freeDSP/freeDSP-OCTAVIA/SOURCES/Documents/Figures/24bitADC.png

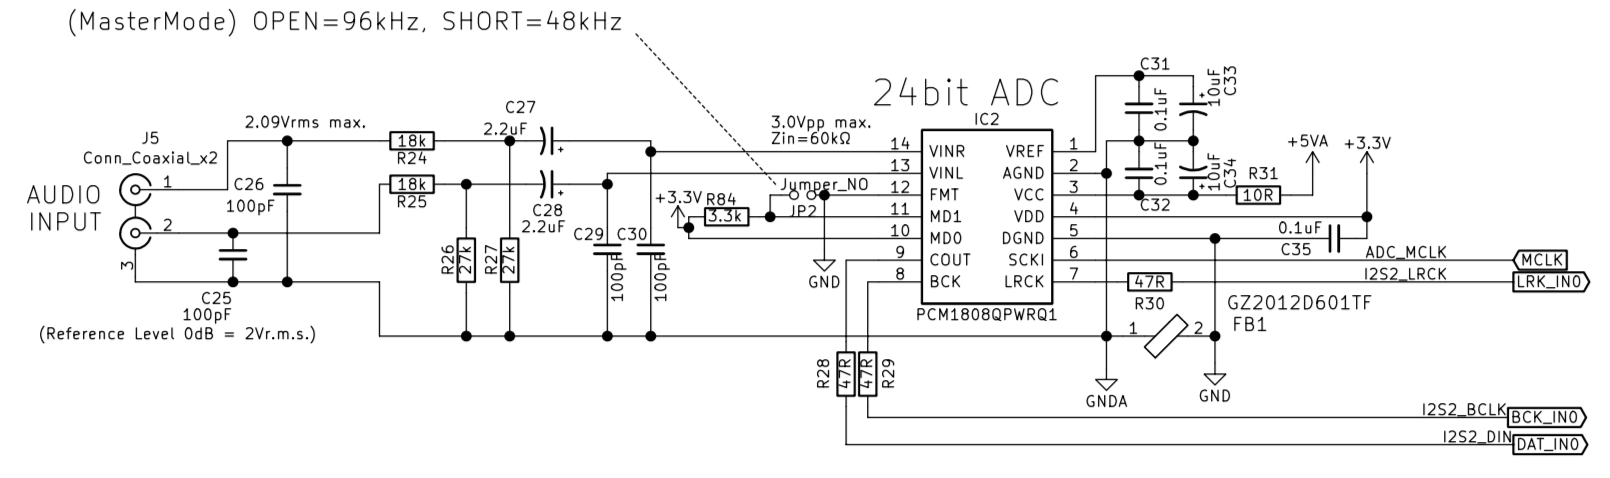
SOURCES/Documents/Figures/24bitADC.png
