freeDSP/freeDSP-OCTAVIA/SOURCES/Documents/Figures/amaneo.jpg

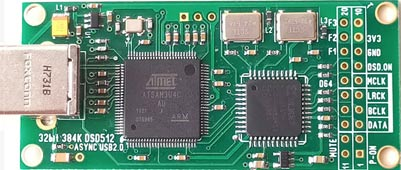
SOURCES/Documents/Figures/amaneo.jpg
