freeDSP/freeDSP-OCTAVIA/SOURCES/Documents/Figures/AnodeCommonRGB-LED.png

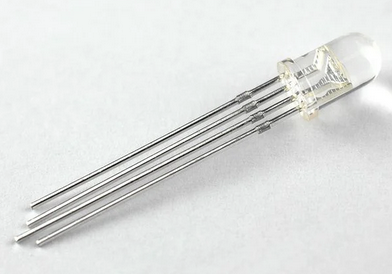
SOURCES/Documents/Figures/AnodeCommonRGB-LED.png
