freeDSP/freeDSP-OCTAVIA/SOURCES/Documents/Figures/ASRC_Setting.gif

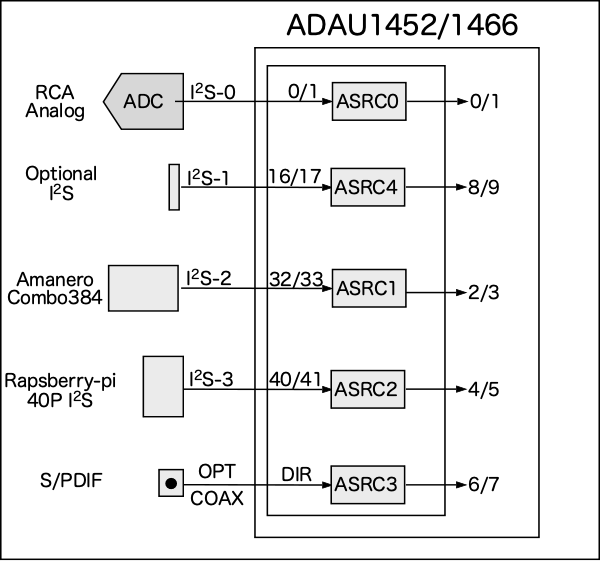
SOURCES/Documents/Figures/ASRC_Setting.gif
