freeDSP/freeDSP-OCTAVIA/SOURCES/Documents/Figures/AUX-ADC_Pots.png

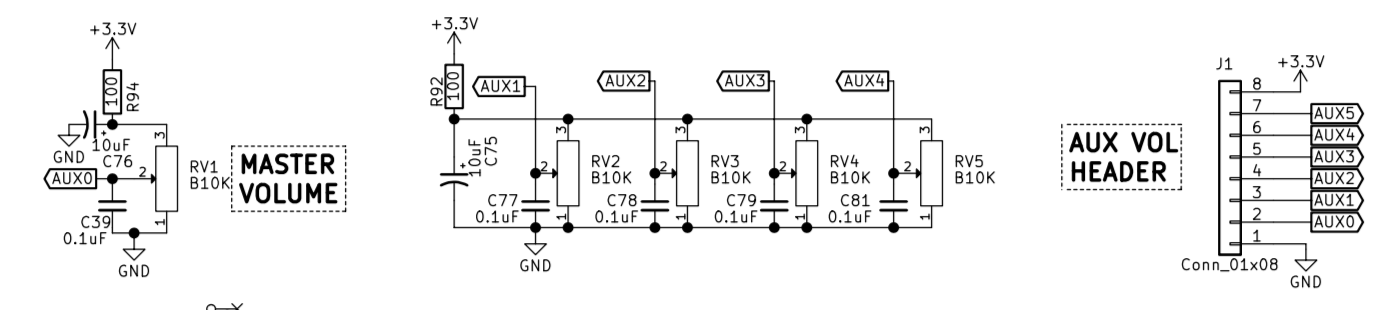
SOURCES/Documents/Figures/AUX-ADC_Pots.png
