freeDSP/freeDSP-OCTAVIA/SOURCES/Documents/Figures/Block_AmaneroCombo384Slot.png

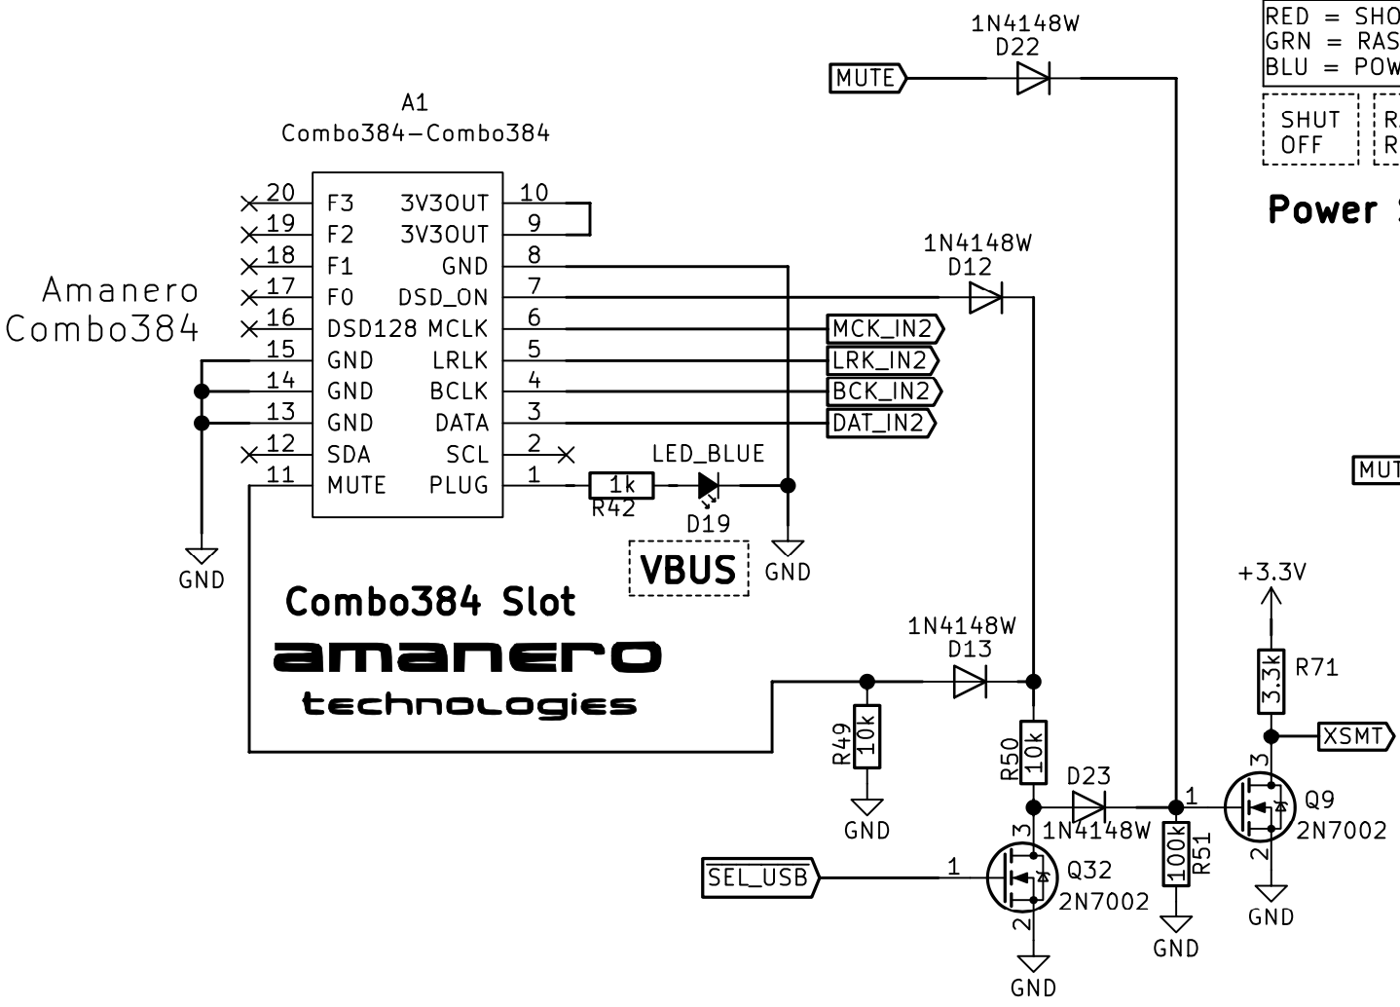
SOURCES/Documents/Figures/Block_AmaneroCombo384Slot.png
