freeDSP/freeDSP-OCTAVIA/SOURCES/Documents/Figures/Block_PowerStatusLED.png

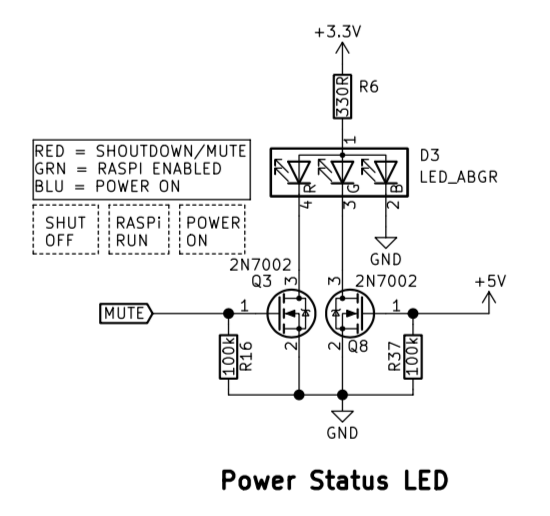
SOURCES/Documents/Figures/Block_PowerStatusLED.png
