freeDSP/freeDSP-OCTAVIA/SOURCES/Documents/Figures/Block_PSU2.png

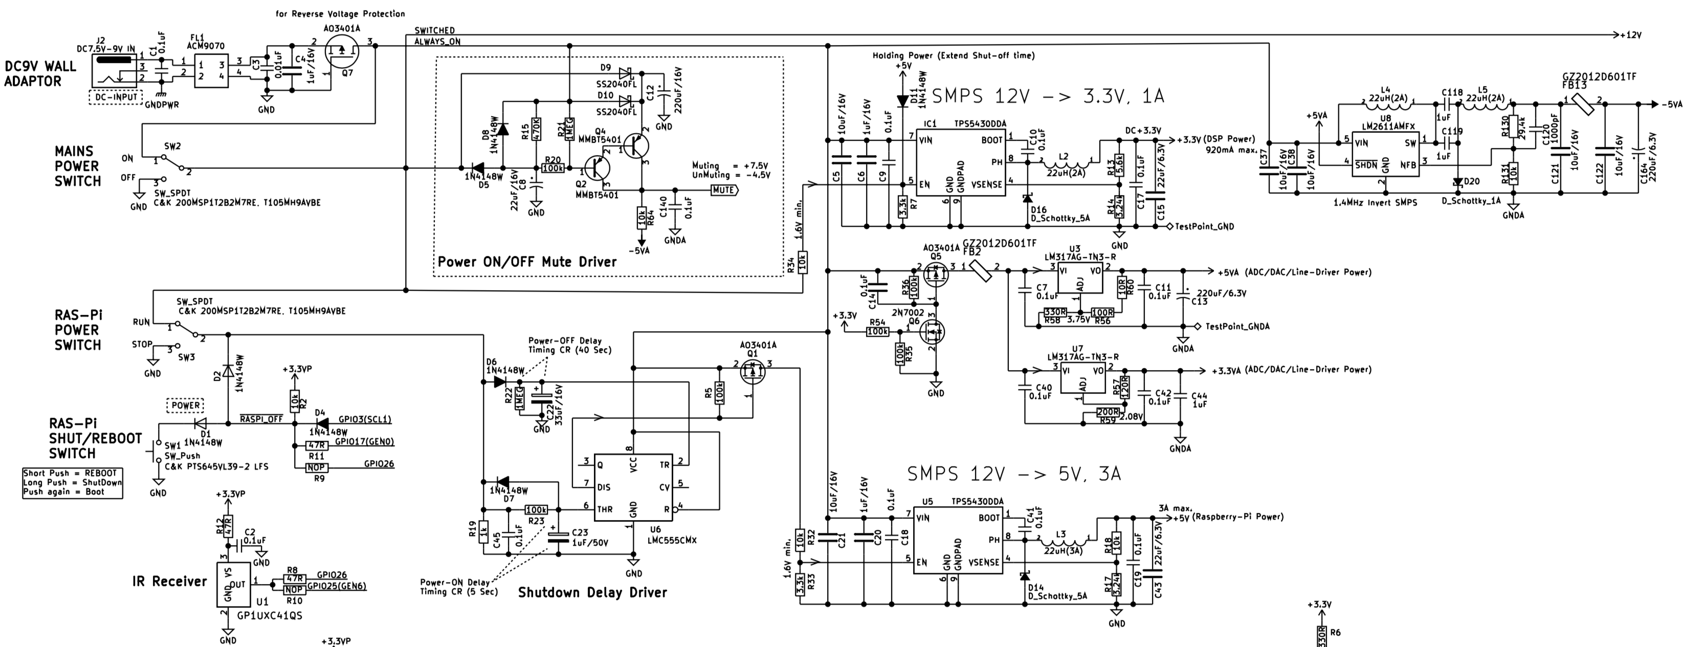
SOURCES/Documents/Figures/Block_PSU2.png
