freeDSP/freeDSP-OCTAVIA/SOURCES/Documents/Figures/Block_PSU.png

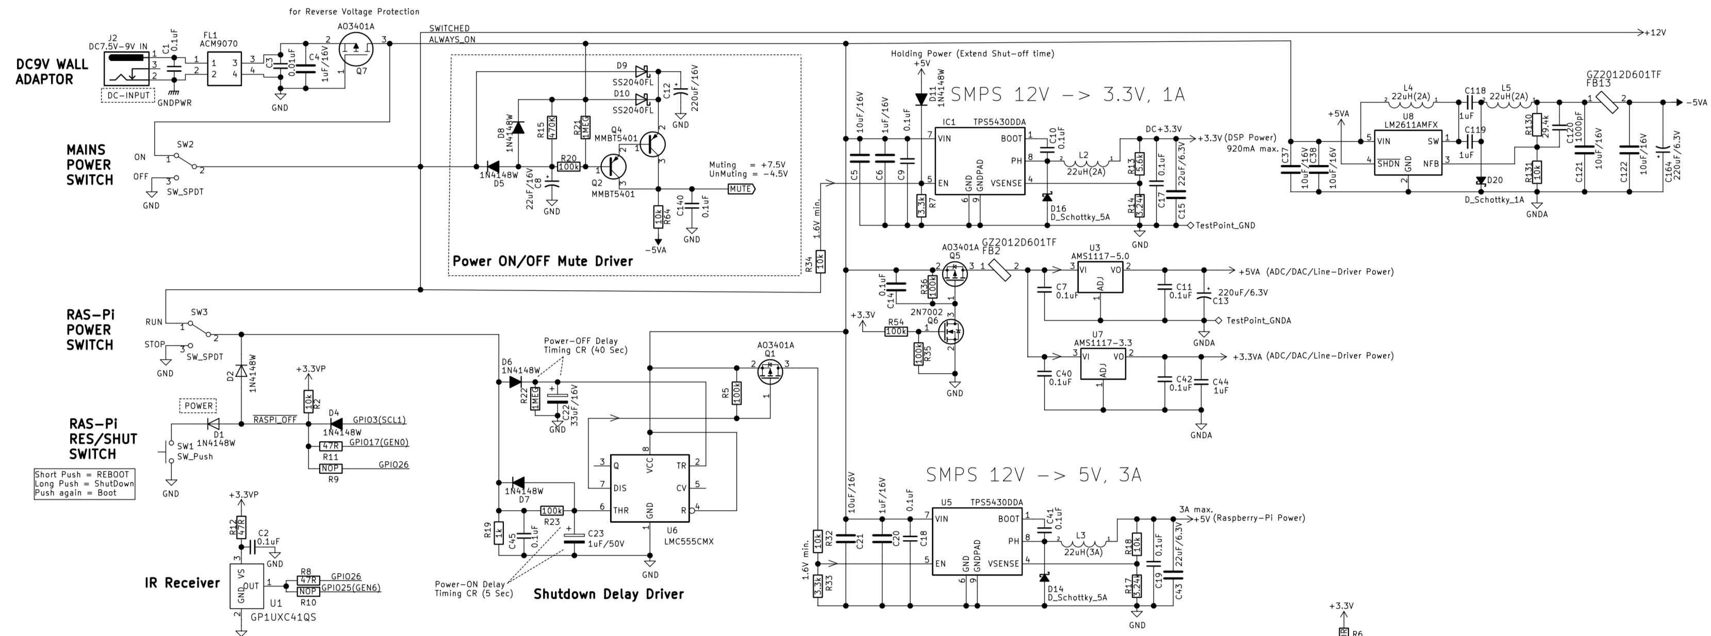
SOURCES/Documents/Figures/Block_PSU.png
