freeDSP/freeDSP-OCTAVIA/SOURCES/Documents/Figures/Block_RaspberryPiSolot.png

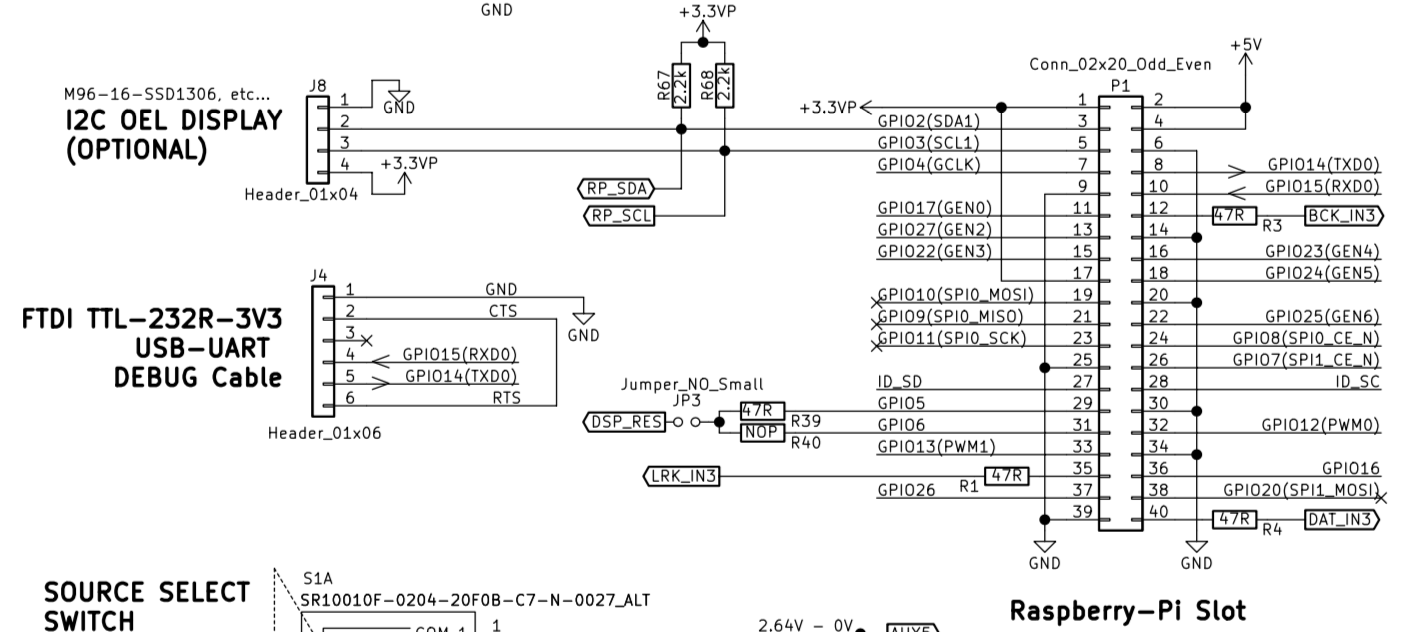
SOURCES/Documents/Figures/Block_RaspberryPiSolot.png
