freeDSP/freeDSP-OCTAVIA/SOURCES/Documents/Figures/bravo.jpg

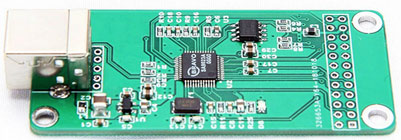
SOURCES/Documents/Figures/bravo.jpg
