freeDSP/freeDSP-OCTAVIA/SOURCES/Documents/Figures/Brovo2.jpg

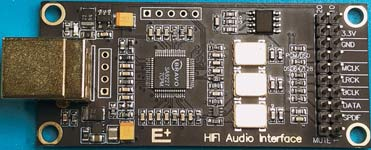
SOURCES/Documents/Figures/Brovo2.jpg
