freeDSP/freeDSP-OCTAVIA/SOURCES/Documents/Figures/C24Removed.jpg

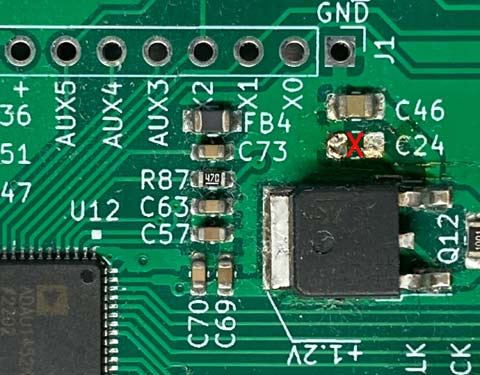
SOURCES/Documents/Figures/C24Removed.jpg
