freeDSP/freeDSP-OCTAVIA/SOURCES/Documents/Figures/Changed_R7_R33.jpg

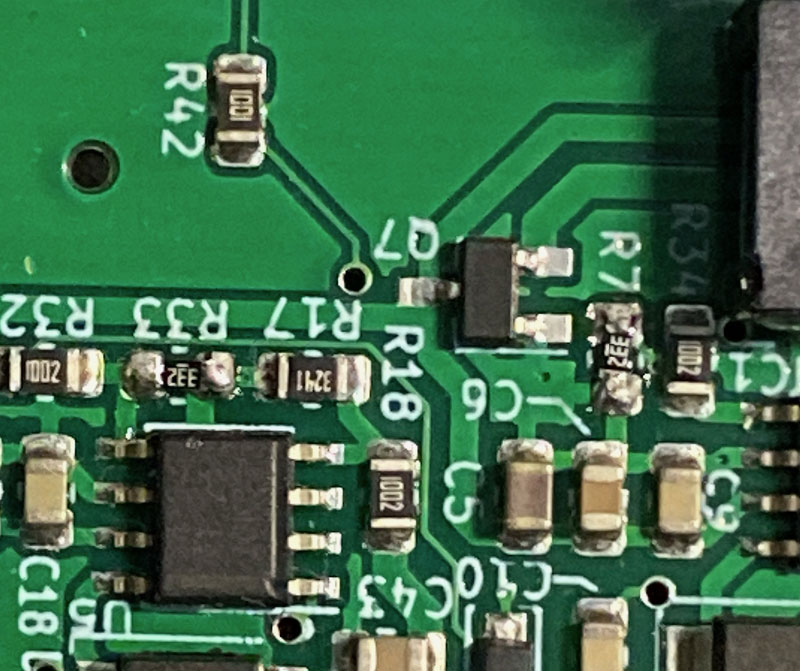
SOURCES/Documents/Figures/Changed_R7_R33.jpg
