freeDSP/freeDSP-OCTAVIA/SOURCES/Documents/Figures/ChangeR76.jpg

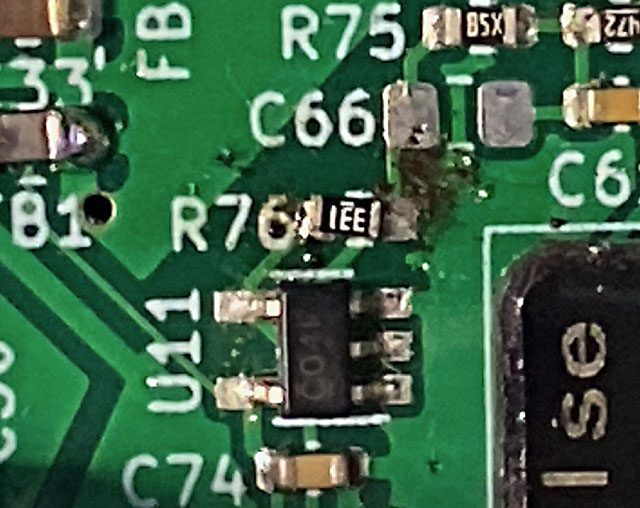
SOURCES/Documents/Figures/ChangeR76.jpg
