freeDSP/freeDSP-OCTAVIA/SOURCES/Documents/Figures/CompileLinkDownloadButton.gif

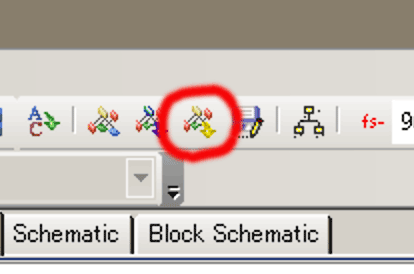
SOURCES/Documents/Figures/CompileLinkDownloadButton.gif
