freeDSP/freeDSP-OCTAVIA/SOURCES/Documents/Figures/DAC_Output.png

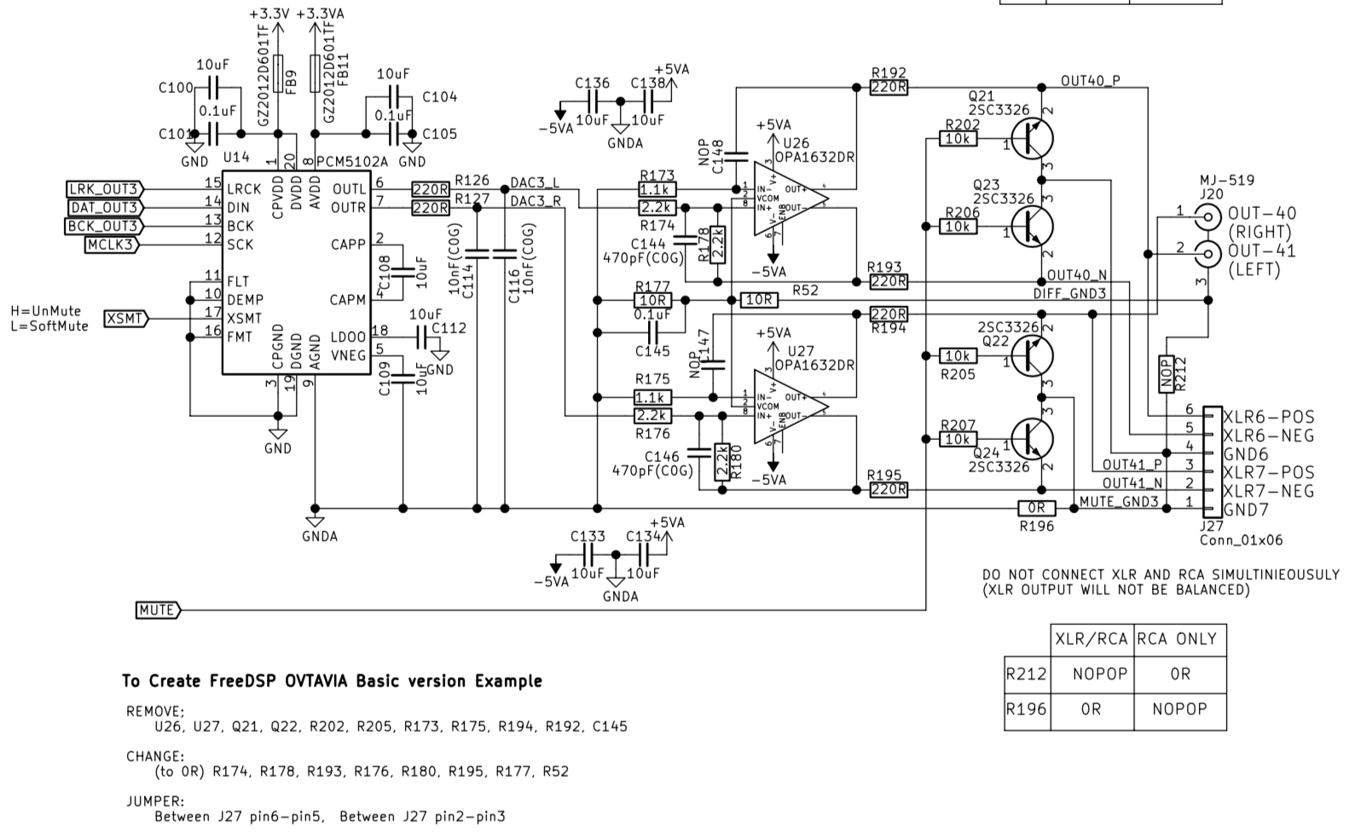
SOURCES/Documents/Figures/DAC_Output.png
