freeDSP/freeDSP-OCTAVIA/SOURCES/Documents/Figures/Diode_D4.png

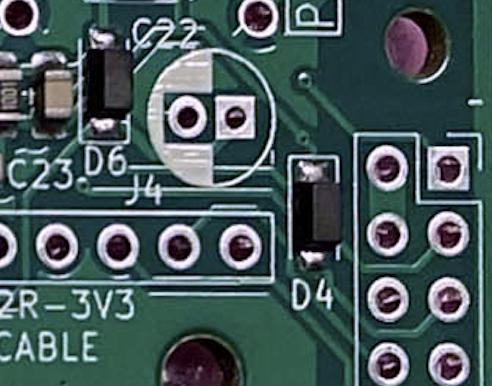
SOURCES/Documents/Figures/Diode_D4.png
