freeDSP/freeDSP-OCTAVIA/SOURCES/Documents/Figures/DSP-OCTAVIA_2wayCrossover_Trim.gif

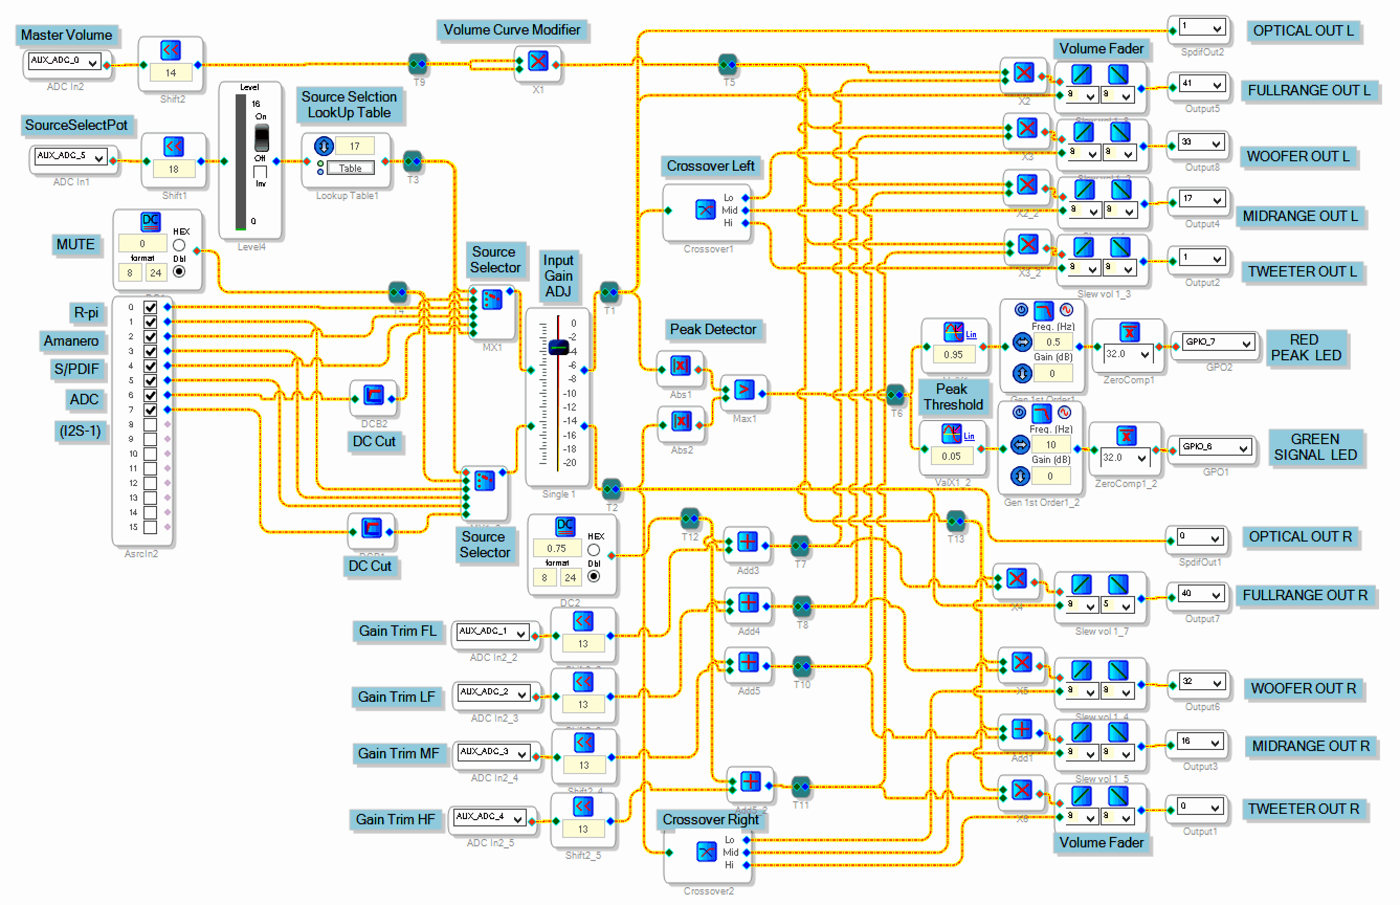
SOURCES/Documents/Figures/DSP-OCTAVIA_2wayCrossover_Trim.gif
