freeDSP/freeDSP-OCTAVIA/SOURCES/Documents/Figures/DSP-OCTAVIA_2wayCrossover_with_Sub_DelayTrim.gif

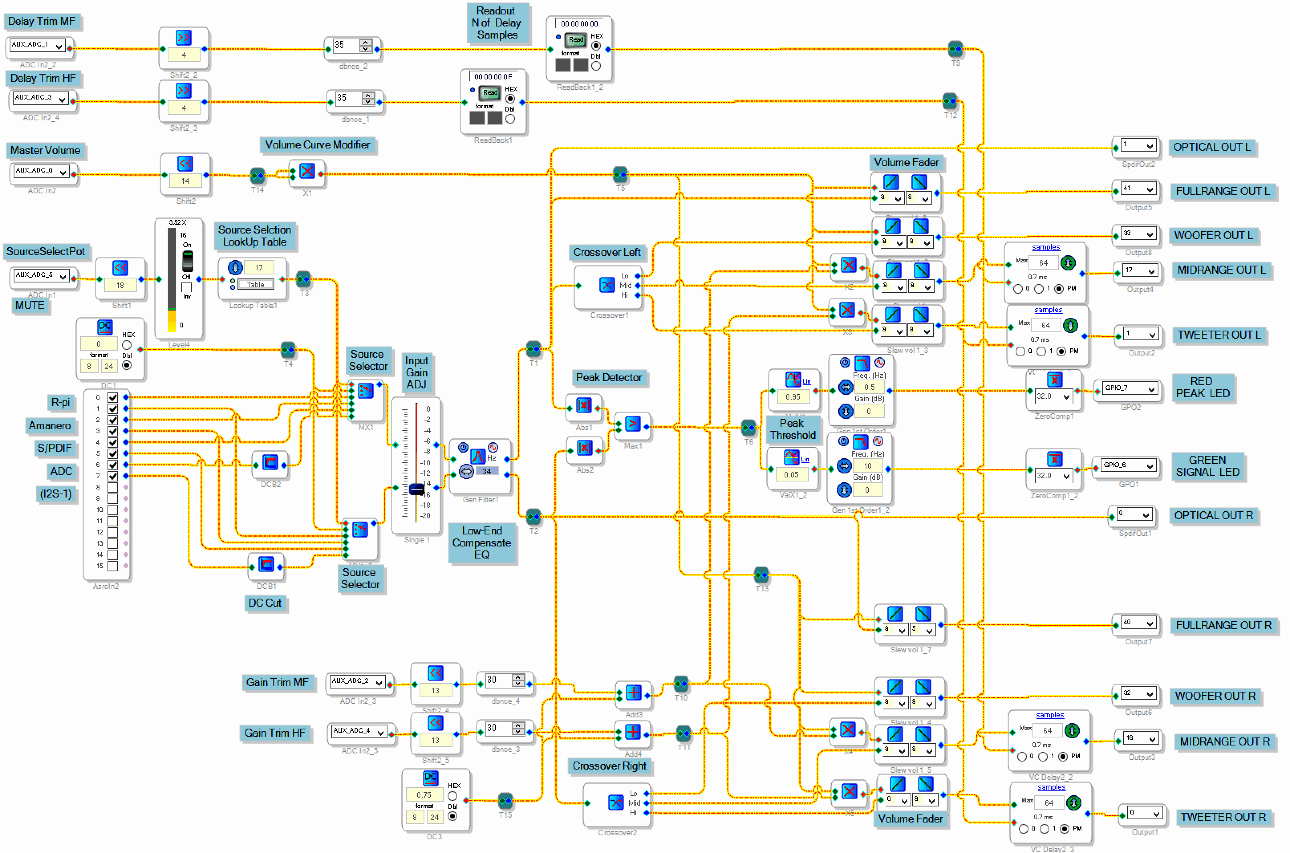
SOURCES/Documents/Figures/DSP-OCTAVIA_2wayCrossover_with_Sub_DelayTrim.gif
