freeDSP/freeDSP-OCTAVIA/SOURCES/Documents/Figures/DSP-OCTAVIA_3wayCrossover_DelayTrim.gif

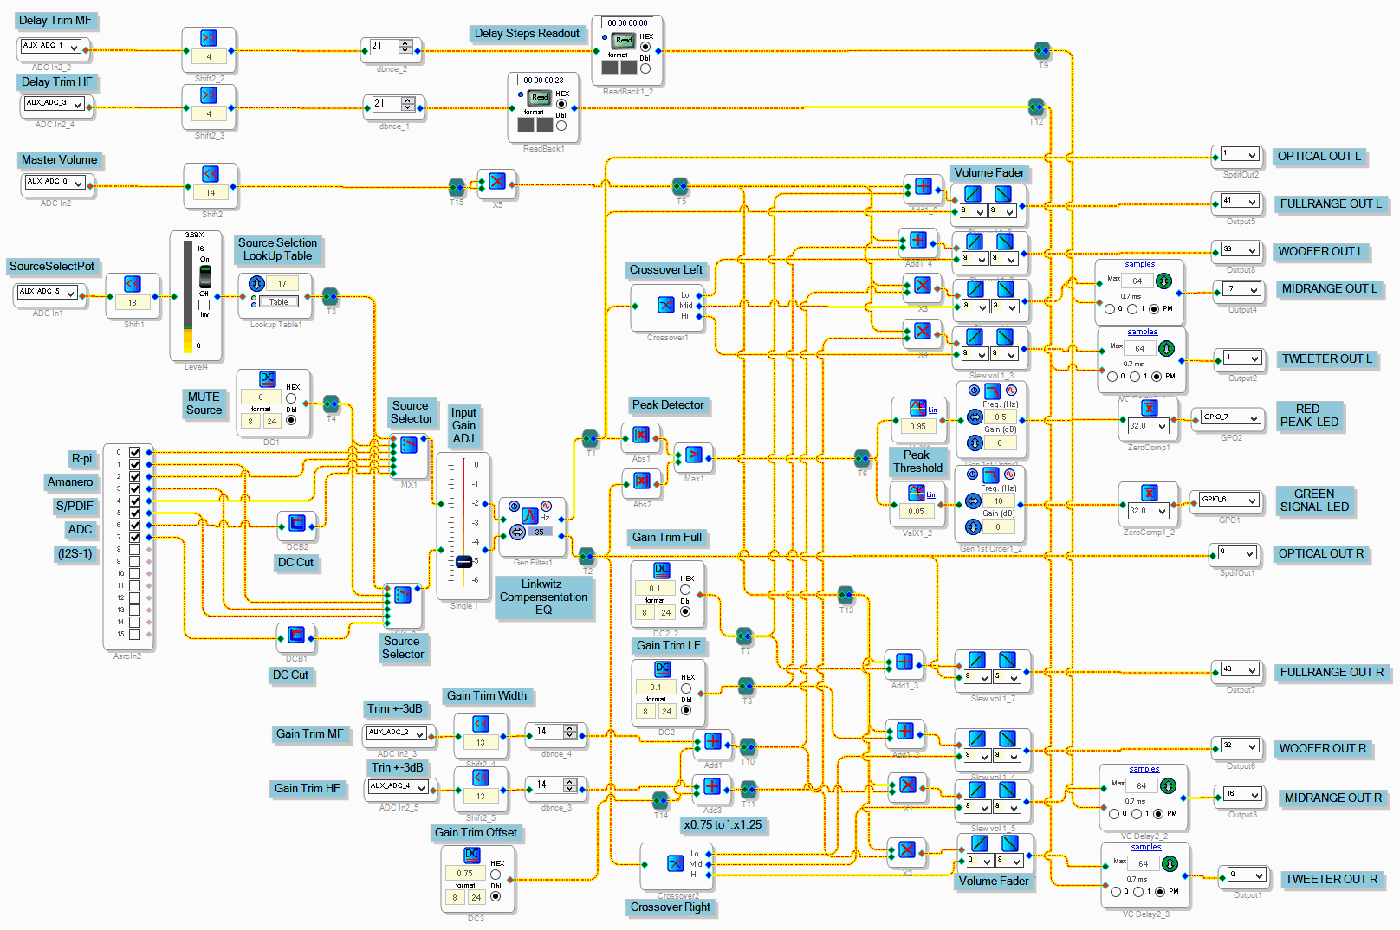
SOURCES/Documents/Figures/DSP-OCTAVIA_3wayCrossover_DelayTrim.gif
