freeDSP/freeDSP-OCTAVIA/SOURCES/Documents/Figures/DSP-OCTAVIA_3wayCrossover_Trim.gif

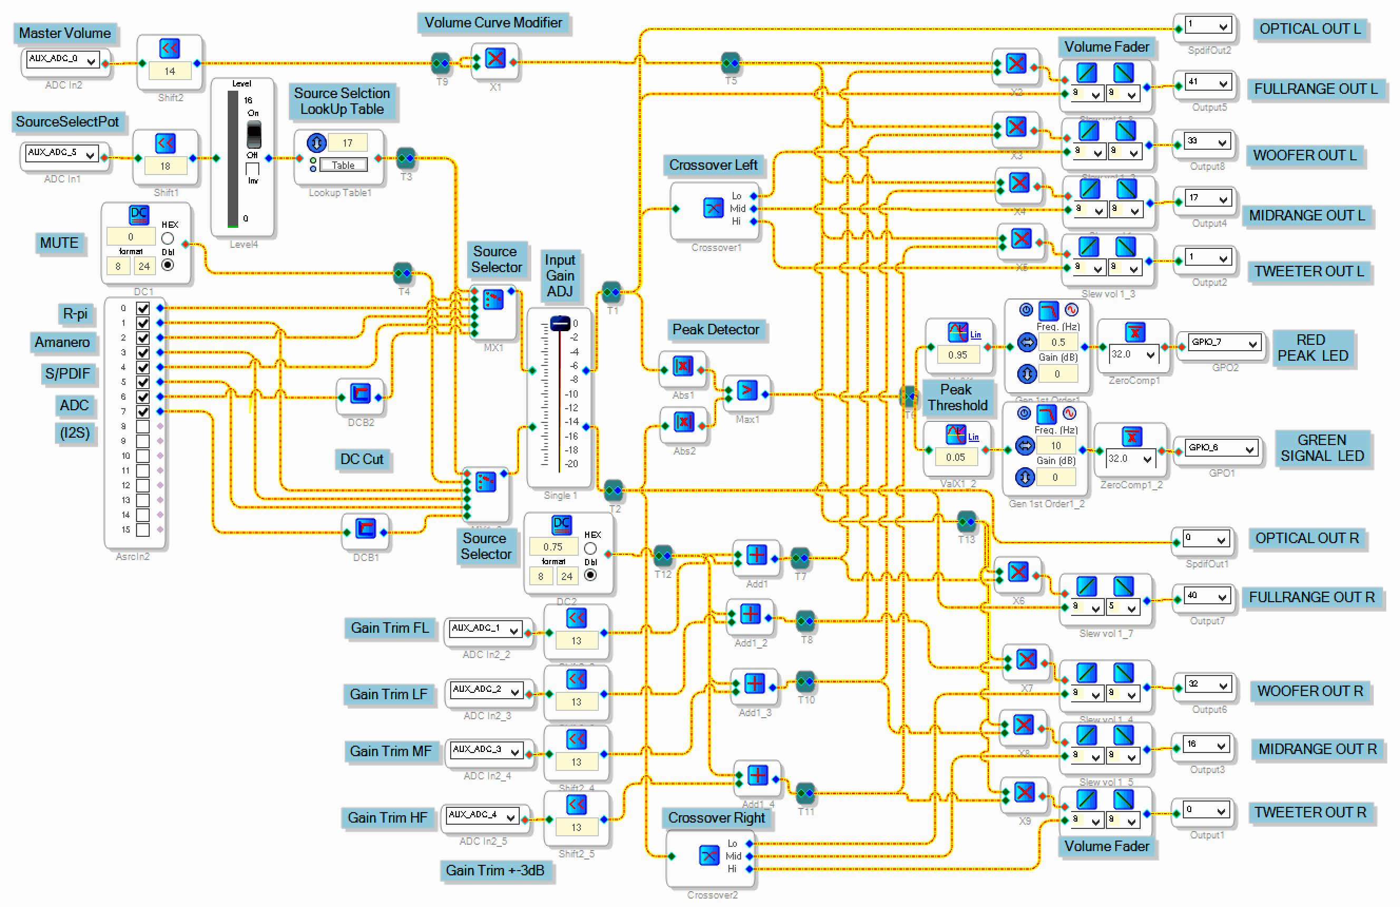
SOURCES/Documents/Figures/DSP-OCTAVIA_3wayCrossover_Trim.gif
