freeDSP/freeDSP-OCTAVIA/SOURCES/Documents/Figures/DSP-OCTAVIA_Thru-Trim.gif

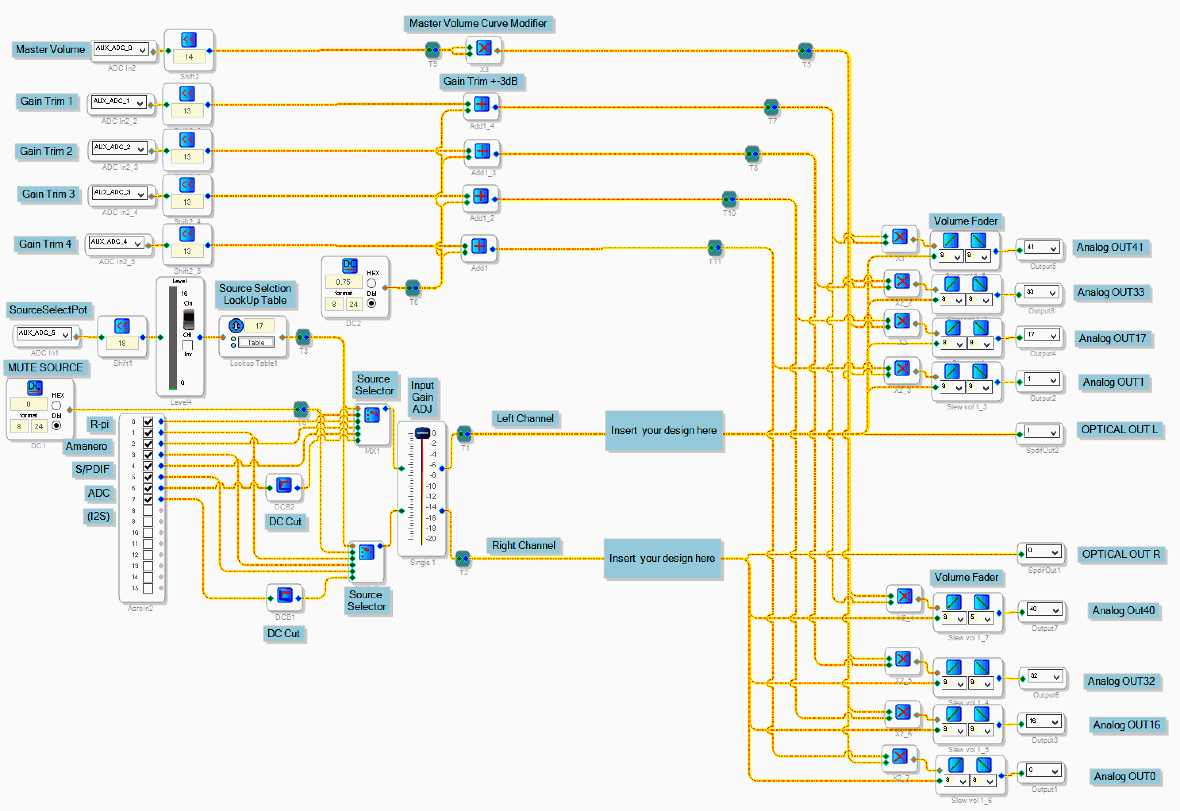
SOURCES/Documents/Figures/DSP-OCTAVIA_Thru-Trim.gif
