freeDSP/freeDSP-OCTAVIA/SOURCES/Documents/Figures/DSP-ResetButton.png

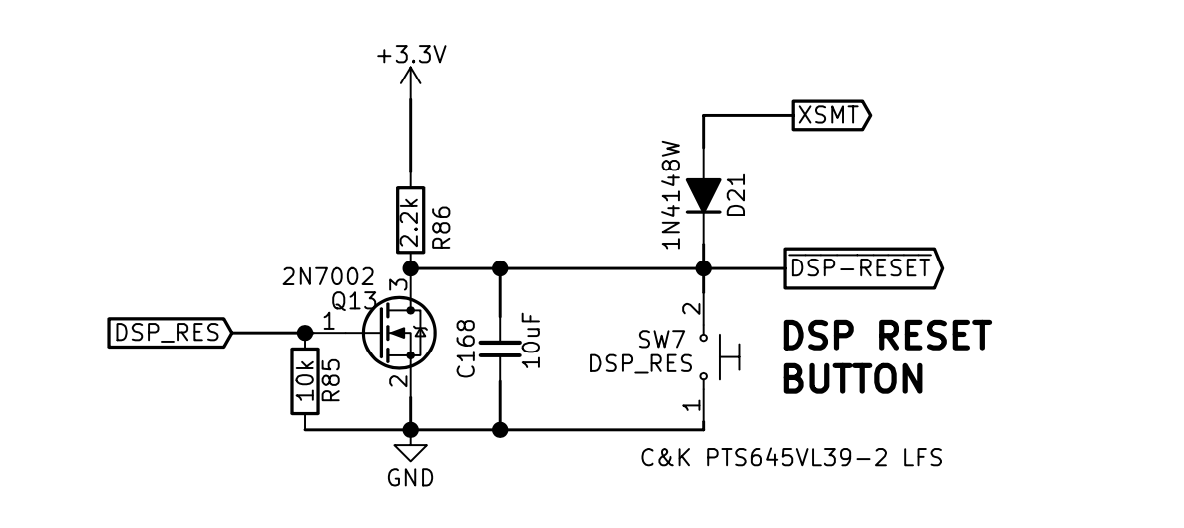
SOURCES/Documents/Figures/DSP-ResetButton.png
