freeDSP/freeDSP-OCTAVIA/SOURCES/Documents/Figures/EEPROM-I2C-USBi.png

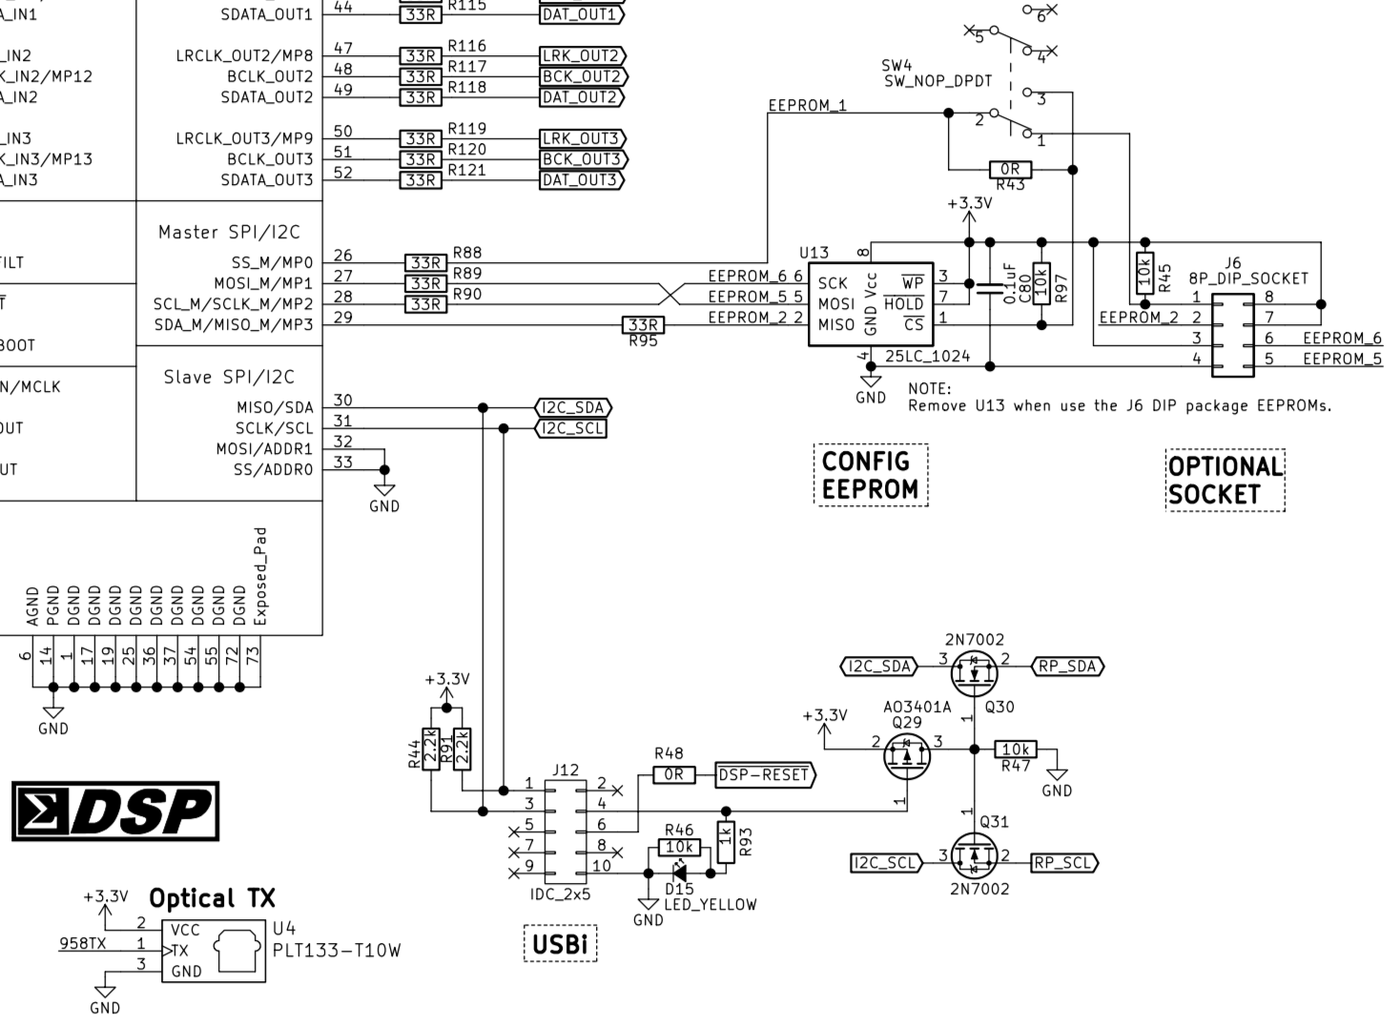
SOURCES/Documents/Figures/EEPROM-I2C-USBi.png
