freeDSP/freeDSP-OCTAVIA/SOURCES/Documents/Figures/Enclosure Coner Photo.JPG

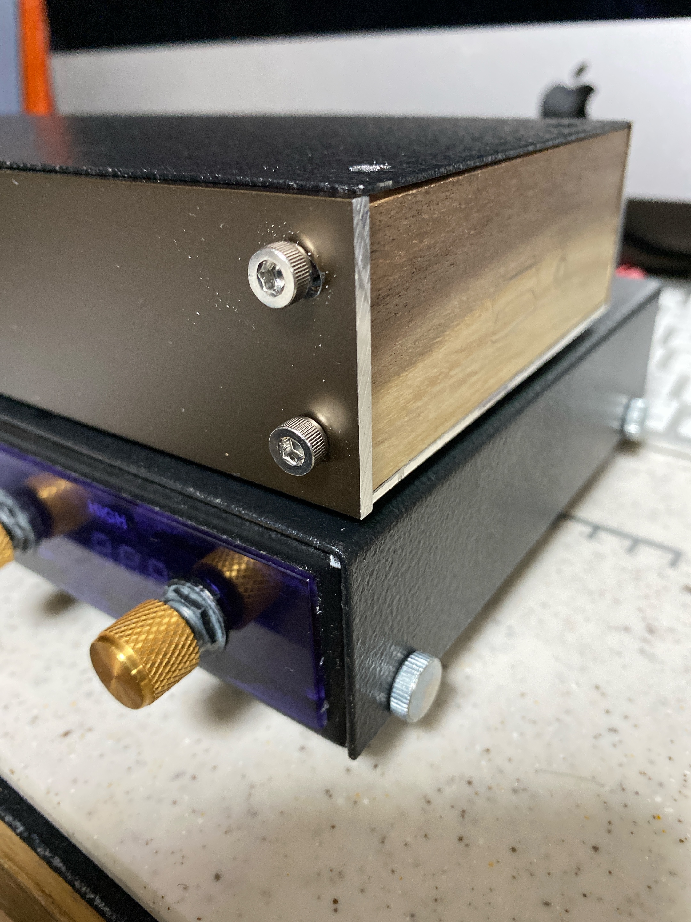
SOURCES/Documents/Figures/Enclosure Coner Photo.JPG
