freeDSP/freeDSP-OCTAVIA/SOURCES/Documents/Figures/Extra-I2S_Input.png

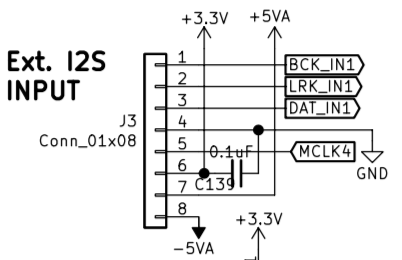
SOURCES/Documents/Figures/Extra-I2S_Input.png
