freeDSP/freeDSP-OCTAVIA/SOURCES/Documents/Figures/FillingResinIntoLED-Hall.JPG

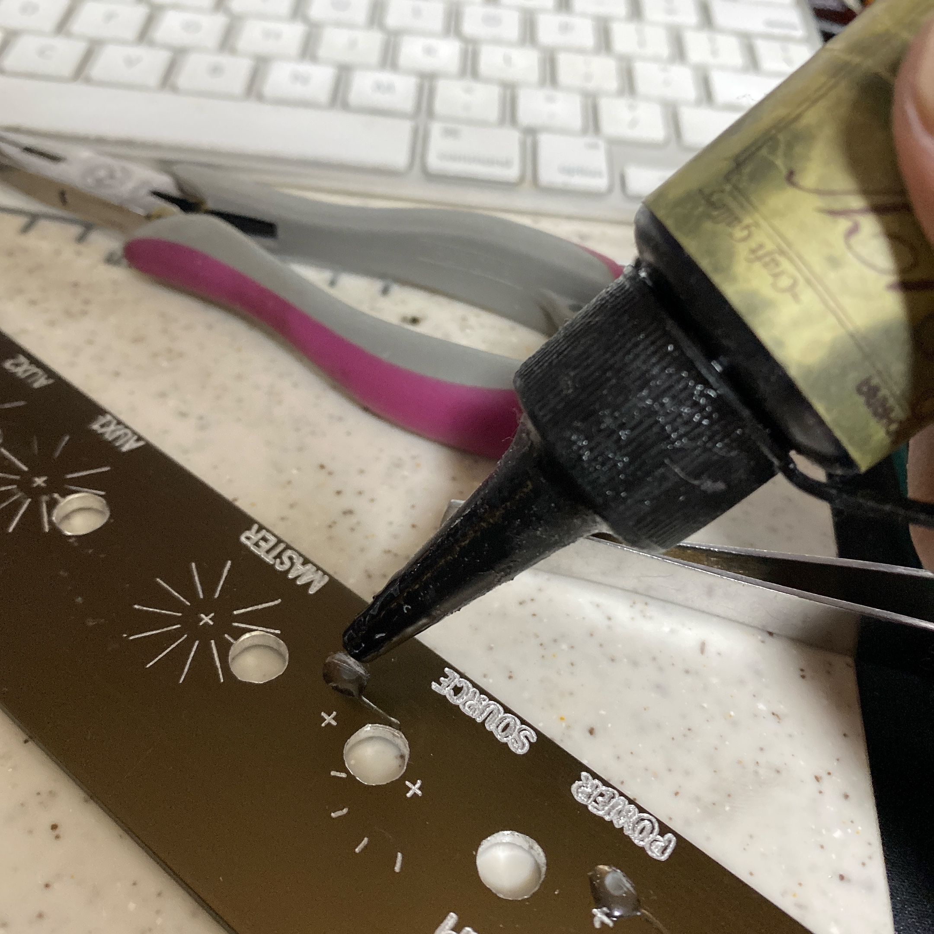
SOURCES/Documents/Figures/FillingResinIntoLED-Hall.JPG
