freeDSP/freeDSP-OCTAVIA/SOURCES/Documents/Figures/FreeDSP OCTAVIA Blanced-out Block Diagram2.gif

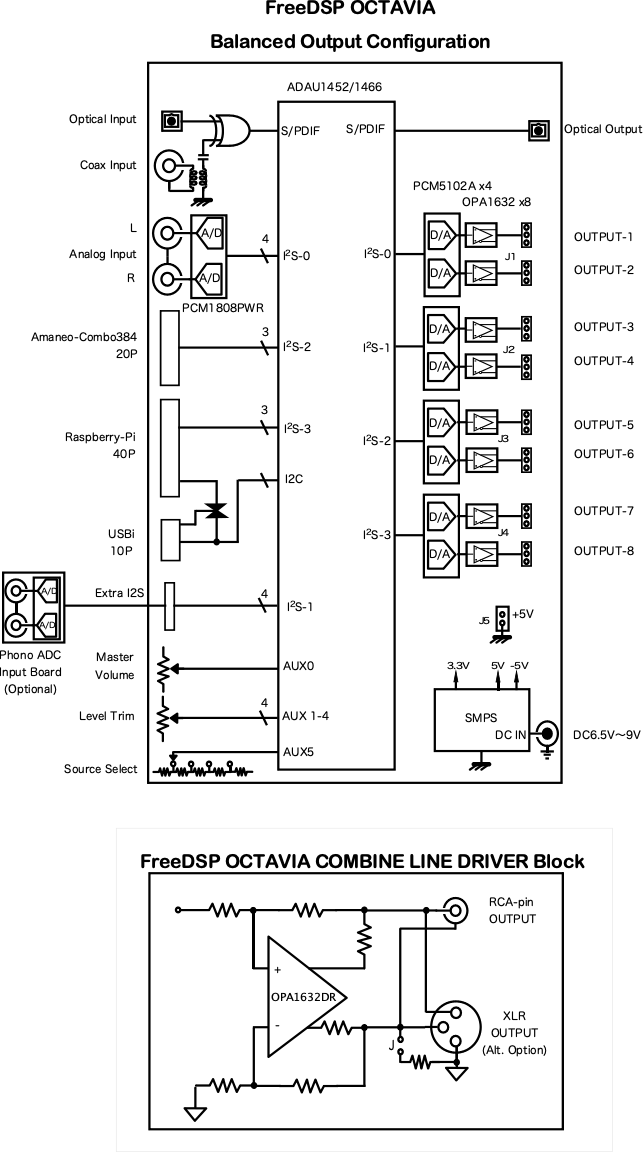
SOURCES/Documents/Figures/FreeDSP OCTAVIA Blanced-out Block Diagram2.gif
