freeDSP/freeDSP-OCTAVIA/SOURCES/Documents/Figures/FreeDSP OCTAVIA Combined-out Block Diagram.png

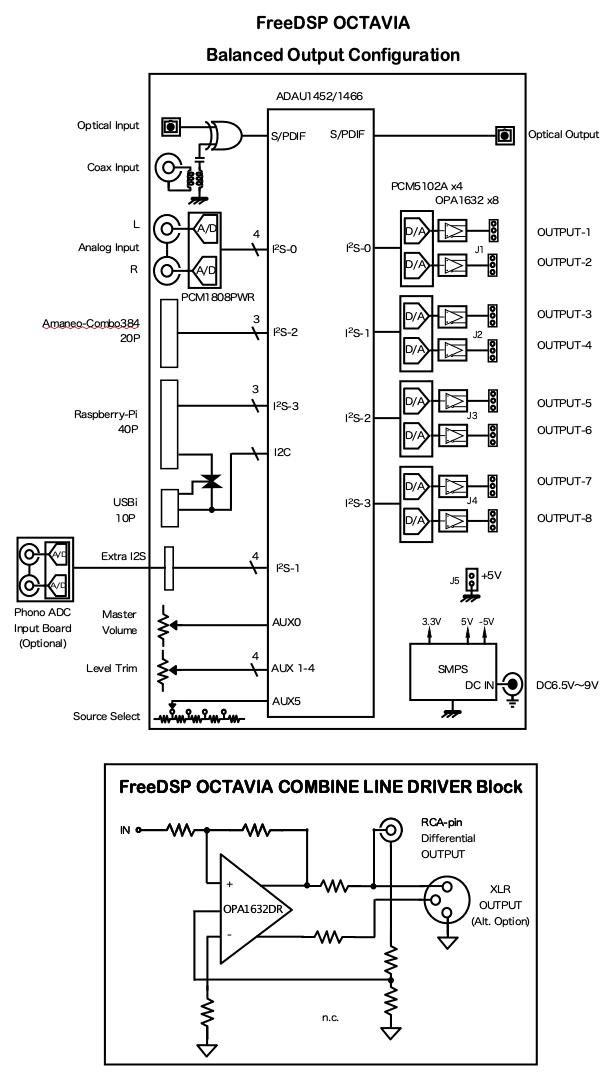
SOURCES/Documents/Figures/FreeDSP OCTAVIA Combined-out Block Diagram.png
