freeDSP/freeDSP-OCTAVIA/SOURCES/Documents/Figures/FreeDSP OCTAVIA Differential-out Block Diagram2.gif

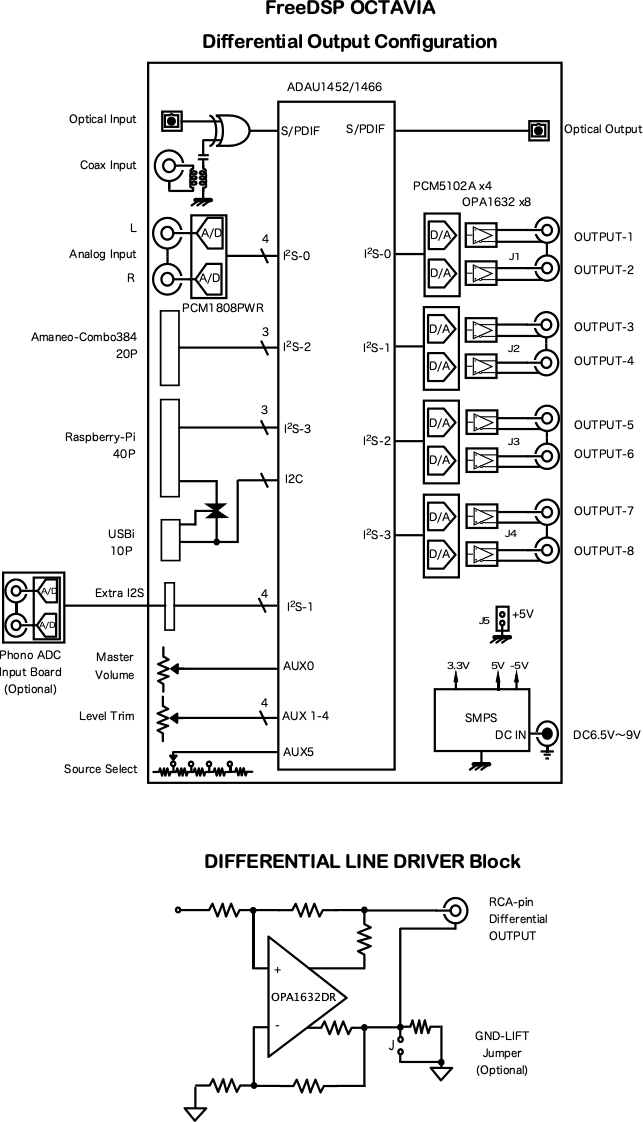
SOURCES/Documents/Figures/FreeDSP OCTAVIA Differential-out Block Diagram2.gif
