freeDSP/freeDSP-OCTAVIA/SOURCES/Documents/Figures/FreeDSP OCTAVIA Differential-out Block Diagram2.png

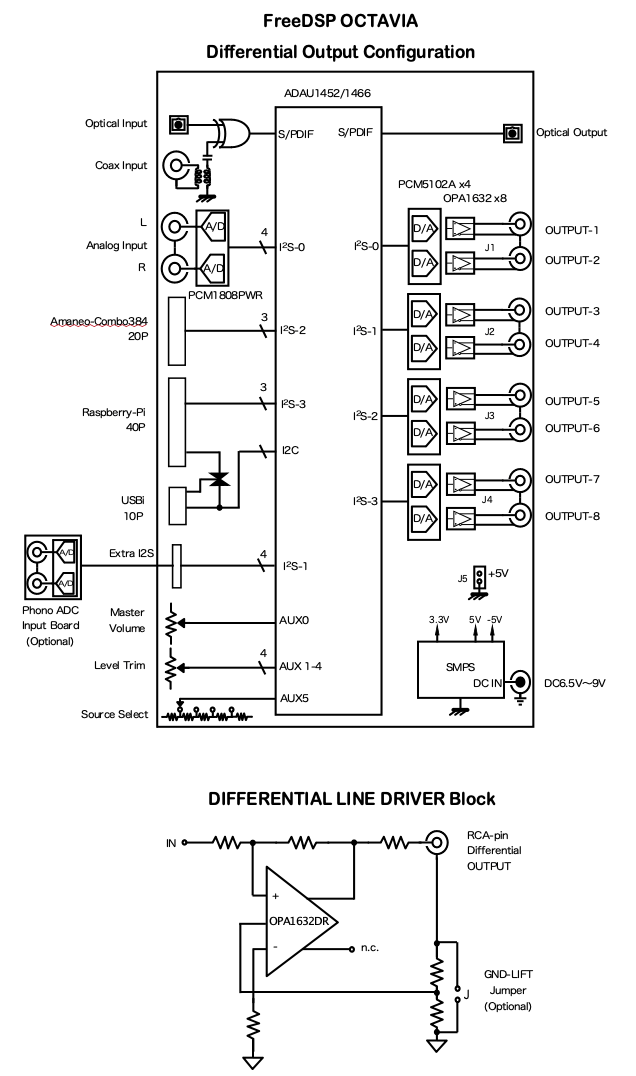
SOURCES/Documents/Figures/FreeDSP OCTAVIA Differential-out Block Diagram2.png
