freeDSP/freeDSP-OCTAVIA/SOURCES/Documents/Figures/FreeDSP OCTAVIA Line Driver Block Diagram.gif

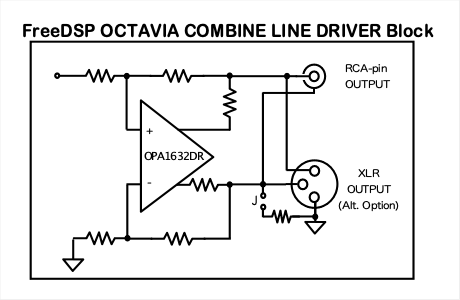
SOURCES/Documents/Figures/FreeDSP OCTAVIA Line Driver Block Diagram.gif
