freeDSP/freeDSP-OCTAVIA/SOURCES/Documents/Figures/FreeDSP OCTAVIA Main Block Diagram.gif

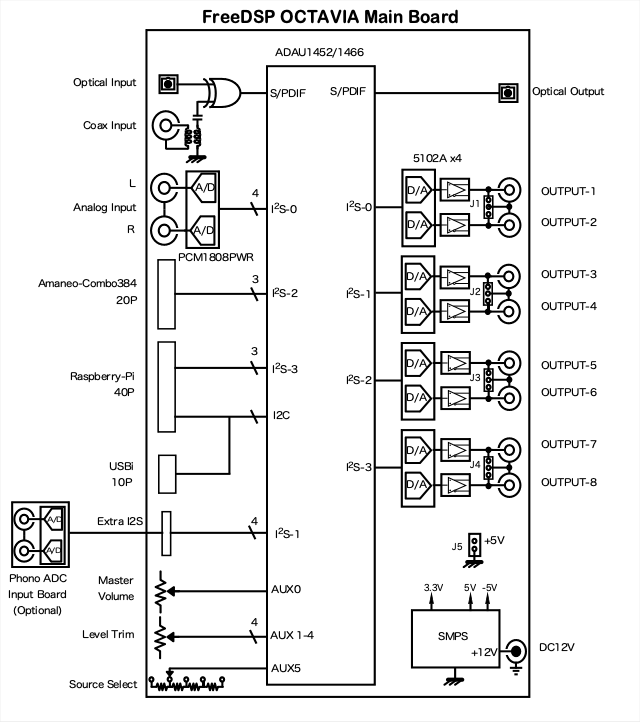
SOURCES/Documents/Figures/FreeDSP OCTAVIA Main Block Diagram.gif
