freeDSP/freeDSP-OCTAVIA/SOURCES/Documents/Figures/FreeDSP OCTAVIA QuadStereoDAC Block Diagram2.gif

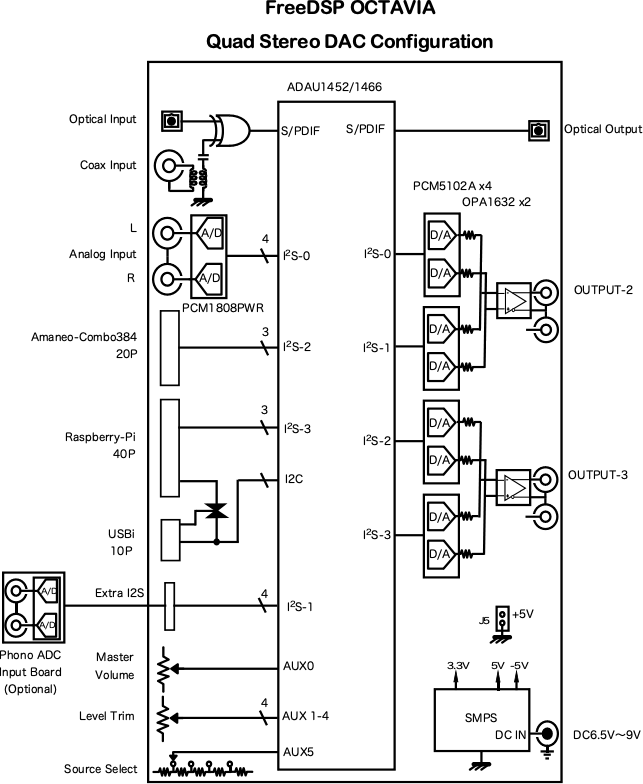
SOURCES/Documents/Figures/FreeDSP OCTAVIA QuadStereoDAC Block Diagram2.gif
