freeDSP/freeDSP-OCTAVIA/SOURCES/Documents/Figures/FreeDSP_OCTAVIA_0v2_PCB-BOTTOMVIEW.jpg

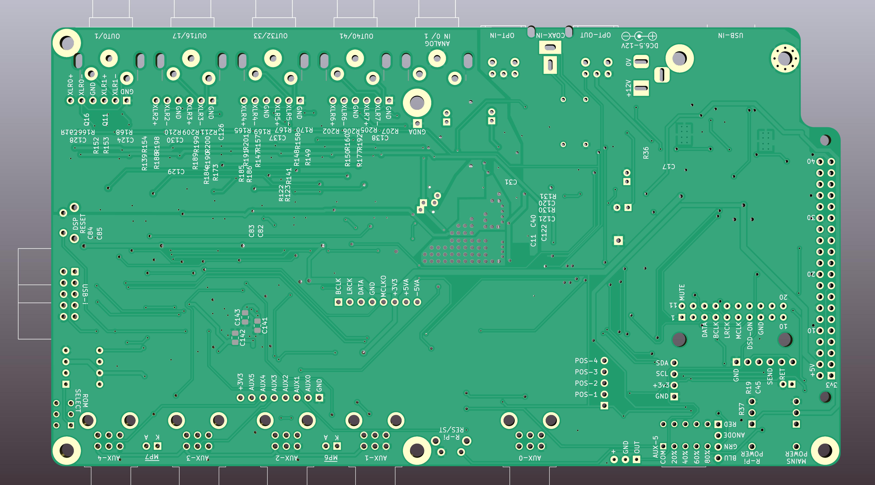
SOURCES/Documents/Figures/FreeDSP_OCTAVIA_0v2_PCB-BOTTOMVIEW.jpg
