freeDSP/freeDSP-OCTAVIA/SOURCES/Documents/Figures/FreeDSP_OCTAVIA_0v2_PCB-TOPVIEW.jpg

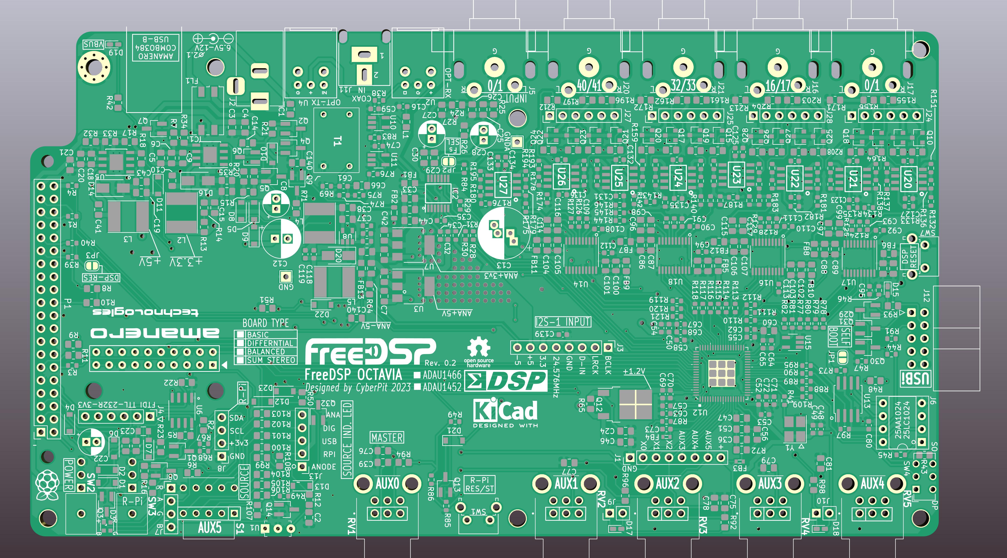
SOURCES/Documents/Figures/FreeDSP_OCTAVIA_0v2_PCB-TOPVIEW.jpg
