freeDSP/freeDSP-OCTAVIA/SOURCES/Documents/Figures/FreeDSP_OCTAVIA_0v3_ParseView.jpg

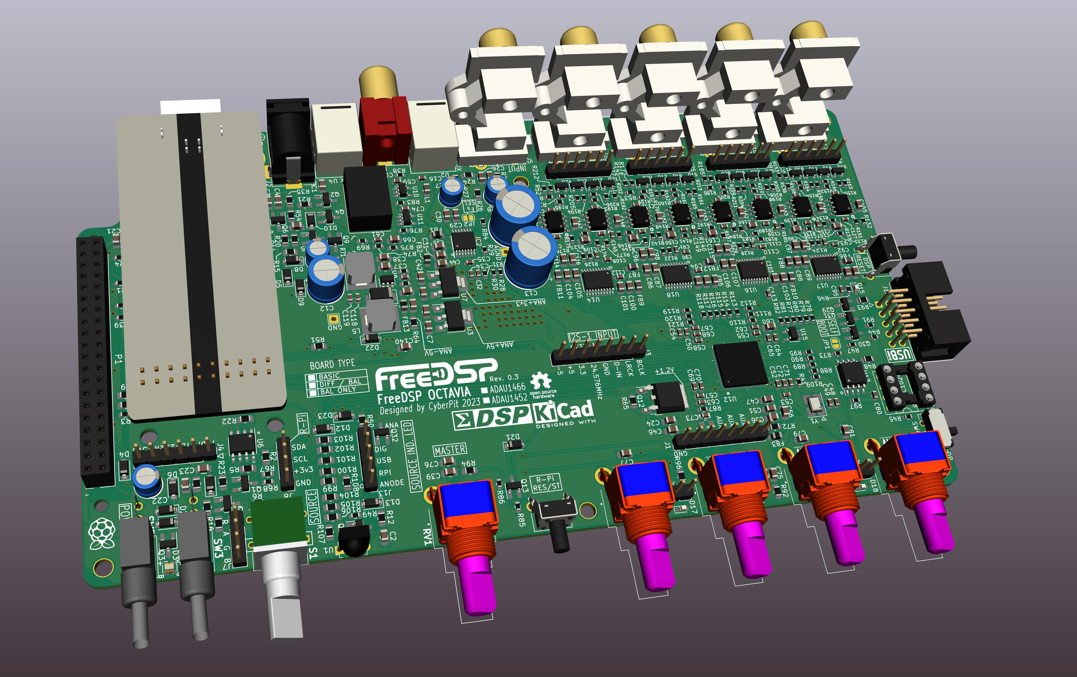
SOURCES/Documents/Figures/FreeDSP_OCTAVIA_0v3_ParseView.jpg
