freeDSP/freeDSP-OCTAVIA/SOURCES/Documents/Figures/FreeDSP_OCTAVIA_0v3_TopVIewPatterns.png

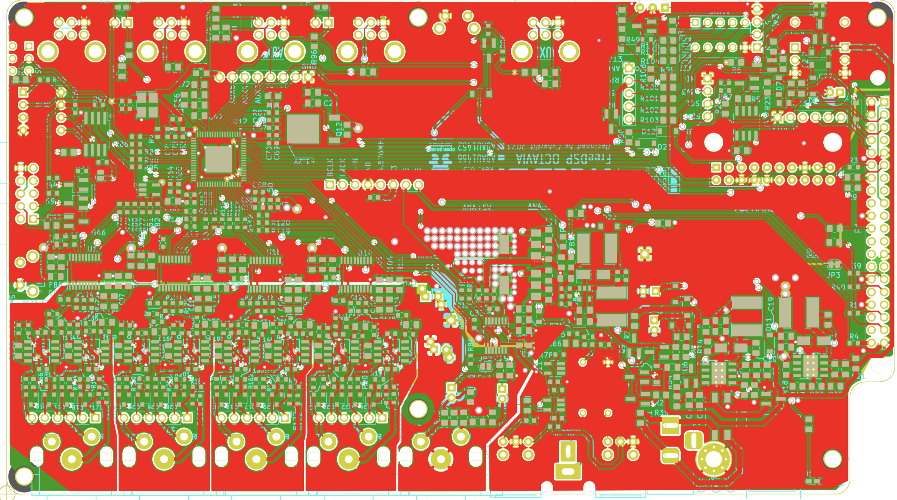
SOURCES/Documents/Figures/FreeDSP_OCTAVIA_0v3_TopVIewPatterns.png
