freeDSP/freeDSP-OCTAVIA/SOURCES/Documents/Figures/FreeDSP_OCTAVIA_0v3_TopVIewRender.jpg

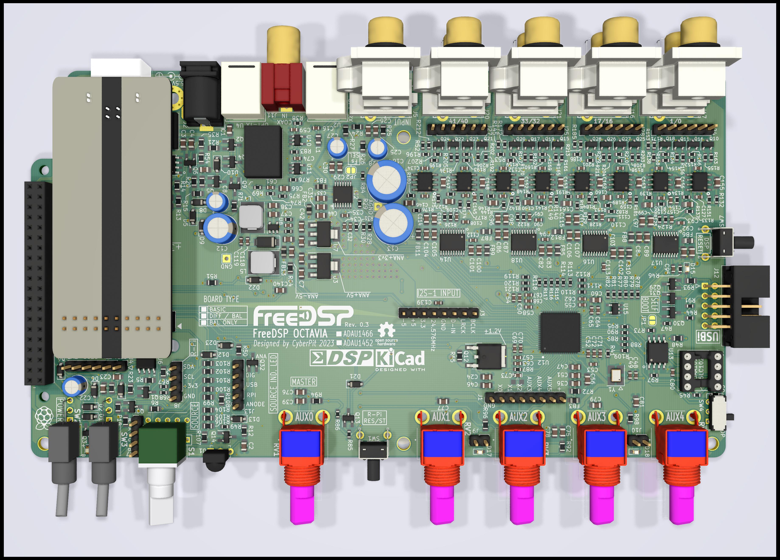
SOURCES/Documents/Figures/FreeDSP_OCTAVIA_0v3_TopVIewRender.jpg
