freeDSP/freeDSP-OCTAVIA/SOURCES/Documents/Figures/HeatsinkAdded_U3U7.jpg

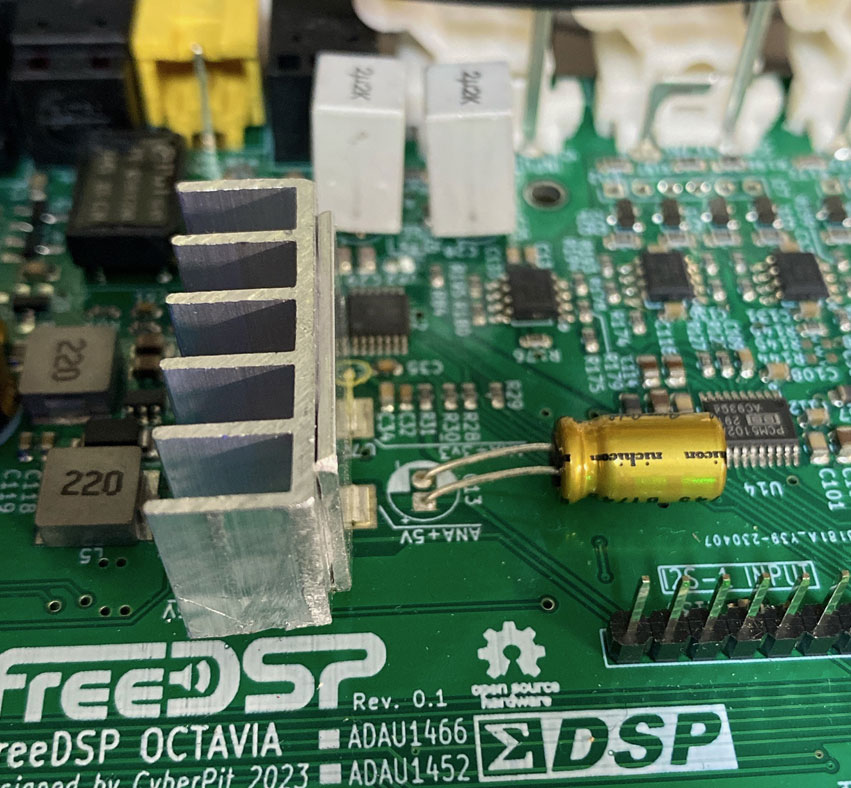
SOURCES/Documents/Figures/HeatsinkAdded_U3U7.jpg
