freeDSP/freeDSP-OCTAVIA/SOURCES/Documents/Figures/IMG_6224.jpg

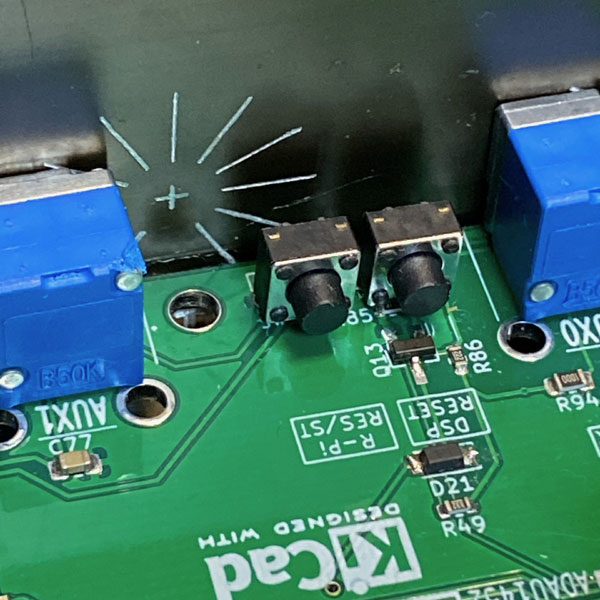
SOURCES/Documents/Figures/IMG_6224.jpg
