freeDSP/freeDSP-OCTAVIA/SOURCES/Documents/Figures/IR_Image.png

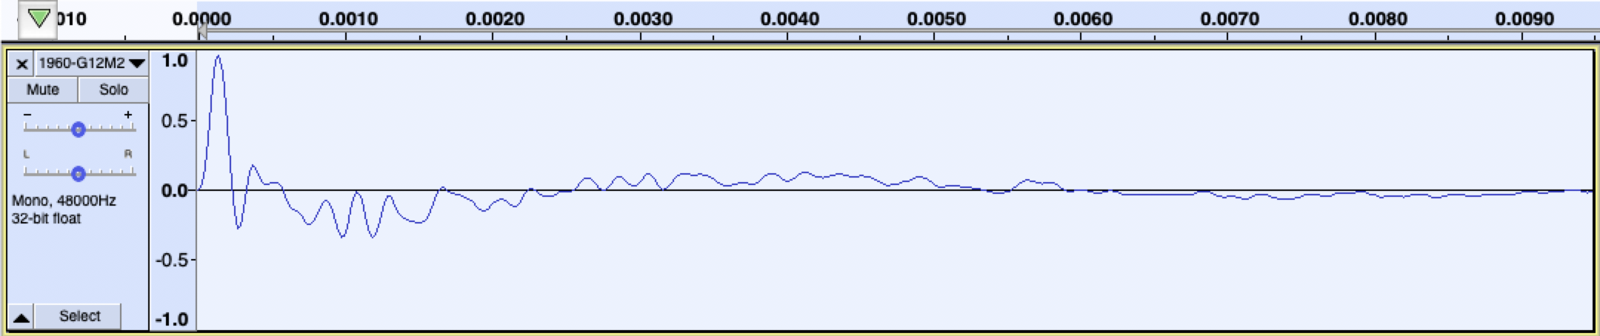
SOURCES/Documents/Figures/IR_Image.png
