freeDSP/freeDSP-OCTAVIA/SOURCES/Documents/Figures/LED-Indicators.png

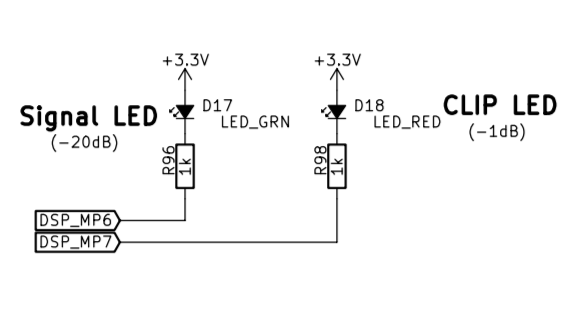
SOURCES/Documents/Figures/LED-Indicators.png
