freeDSP/freeDSP-OCTAVIA/SOURCES/Documents/Figures/MasterClockDriver.png

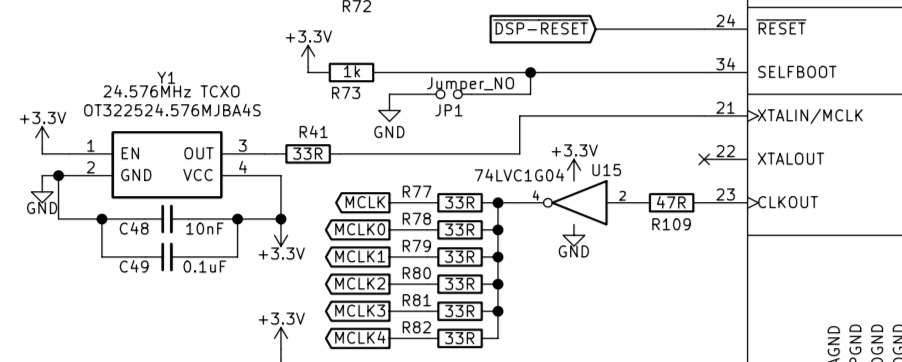
SOURCES/Documents/Figures/MasterClockDriver.png
