freeDSP/freeDSP-OCTAVIA/SOURCES/Documents/Figures/MilledPanels.JPG

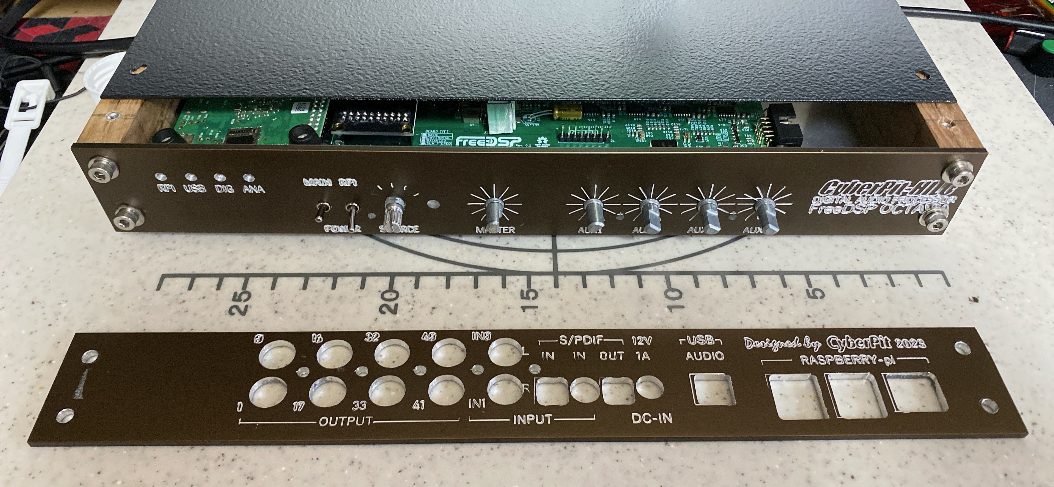
SOURCES/Documents/Figures/MilledPanels.JPG
