freeDSP/freeDSP-OCTAVIA/SOURCES/Documents/Figures/OCTAVIA_3wayp1_1k9_9K6_EQ_BalanceTimeAdj.png

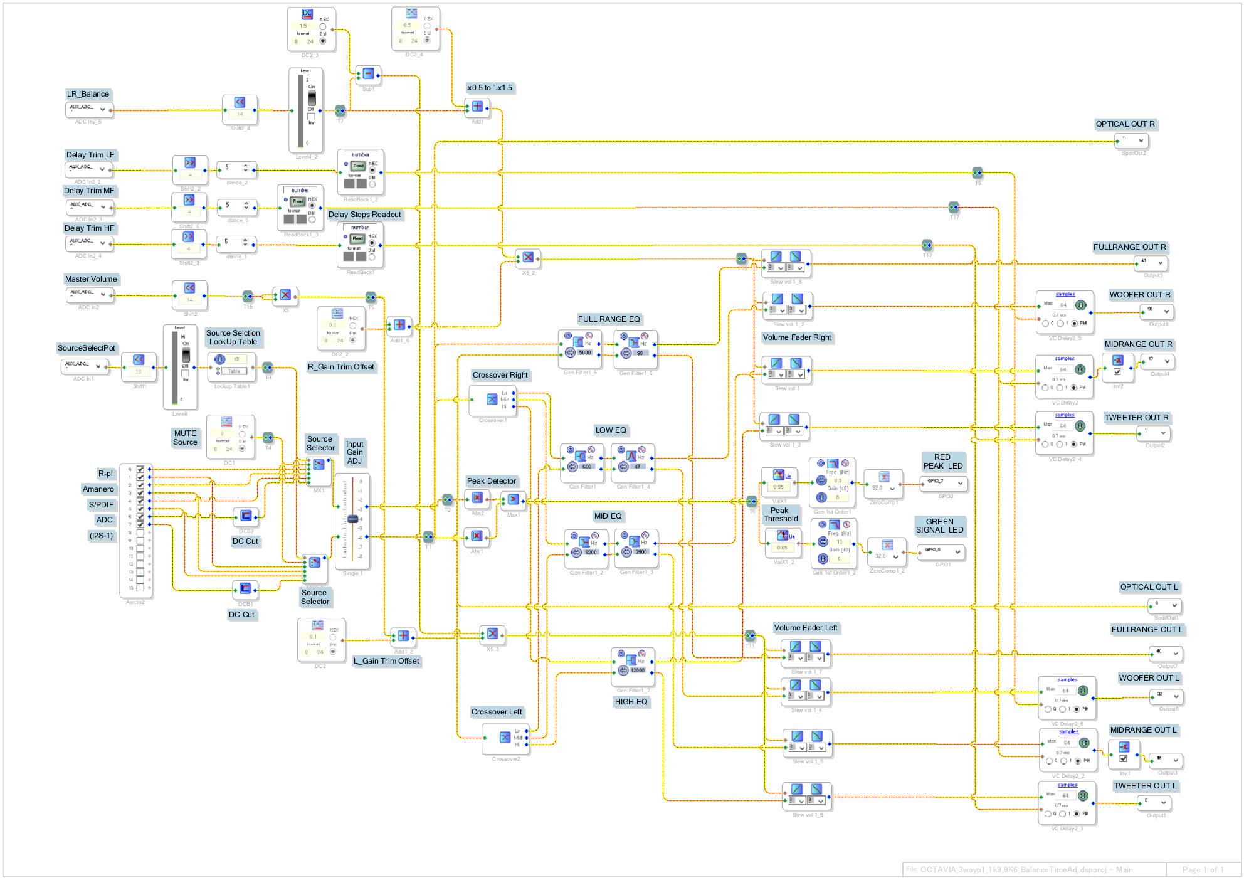
SOURCES/Documents/Figures/OCTAVIA_3wayp1_1k9_9K6_EQ_BalanceTimeAdj.png
