freeDSP/freeDSP-OCTAVIA/SOURCES/Documents/Figures/Offset_C13.jpg

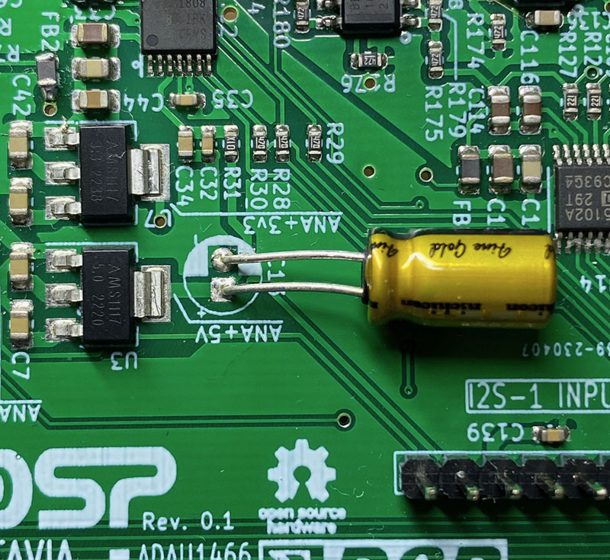
SOURCES/Documents/Figures/Offset_C13.jpg
