freeDSP/freeDSP-OCTAVIA/SOURCES/Documents/Figures/OLED_0inch91.jpg

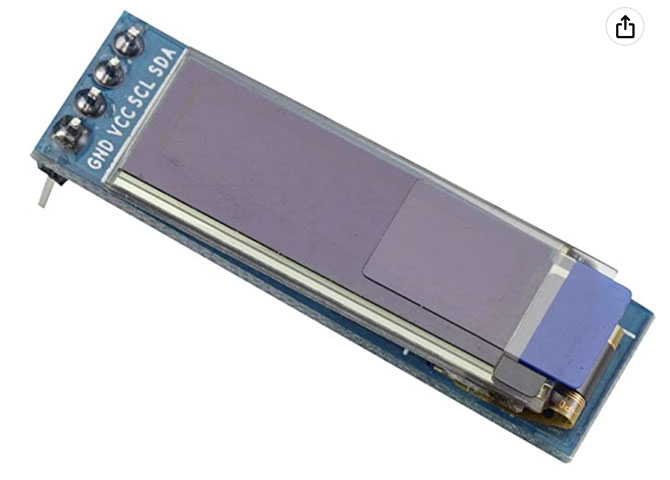
SOURCES/Documents/Figures/OLED_0inch91.jpg
