freeDSP/freeDSP-OCTAVIA/SOURCES/Documents/Figures/OLED_0inchi95.jpg

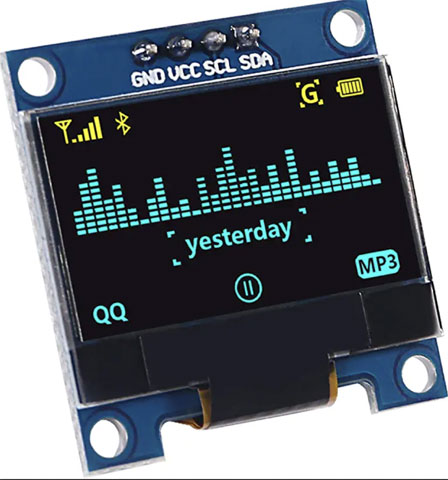
SOURCES/Documents/Figures/OLED_0inchi95.jpg
