freeDSP/freeDSP-OCTAVIA/SOURCES/Documents/Figures/paarameter_for_25AA1024.png

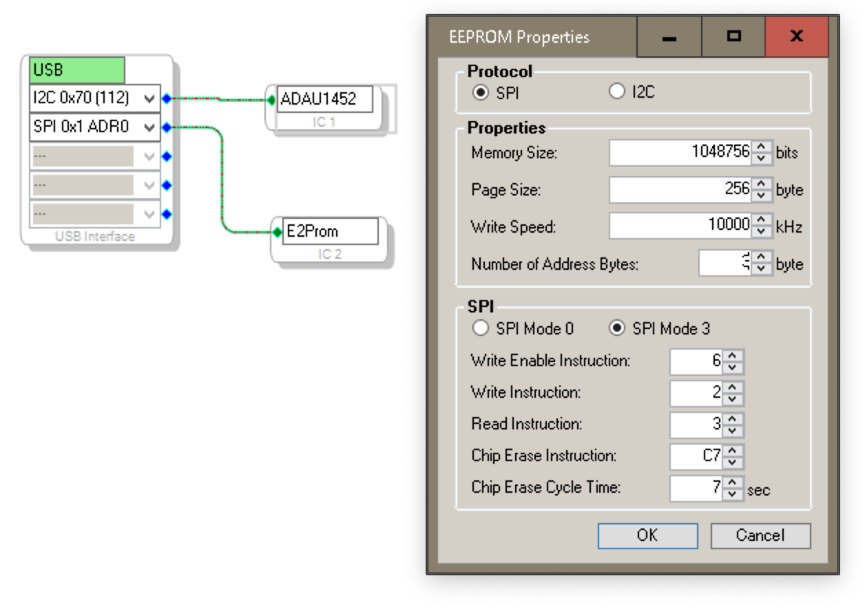
SOURCES/Documents/Figures/paarameter_for_25AA1024.png
