freeDSP/freeDSP-OCTAVIA/SOURCES/Documents/Figures/PCBA基板画像.jpg

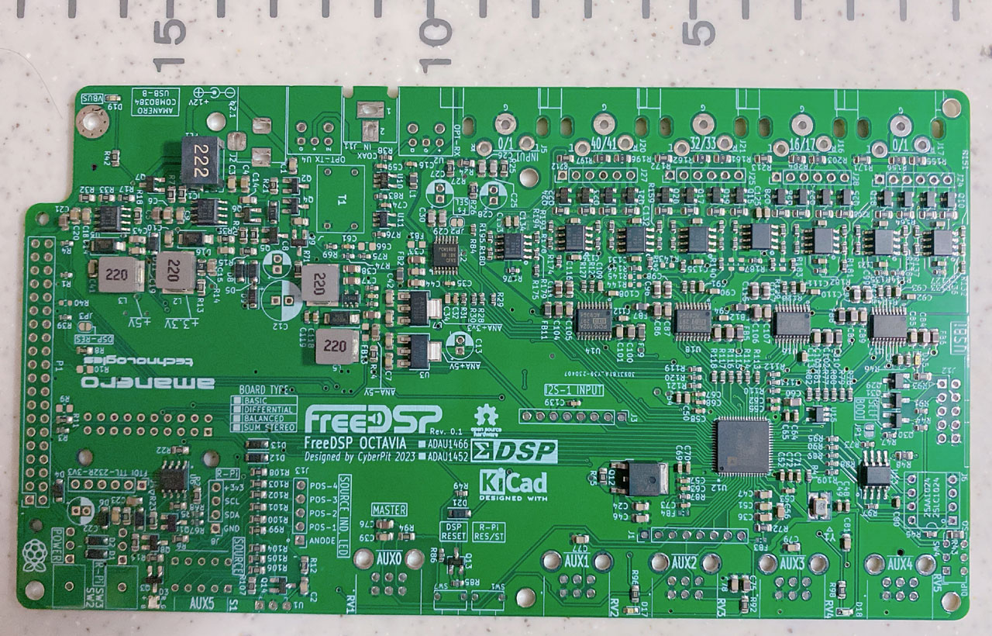
SOURCES/Documents/Figures/PCBA基板画像.jpg
