freeDSP/freeDSP-OCTAVIA/SOURCES/Documents/Figures/PowerRailCheck.jpg

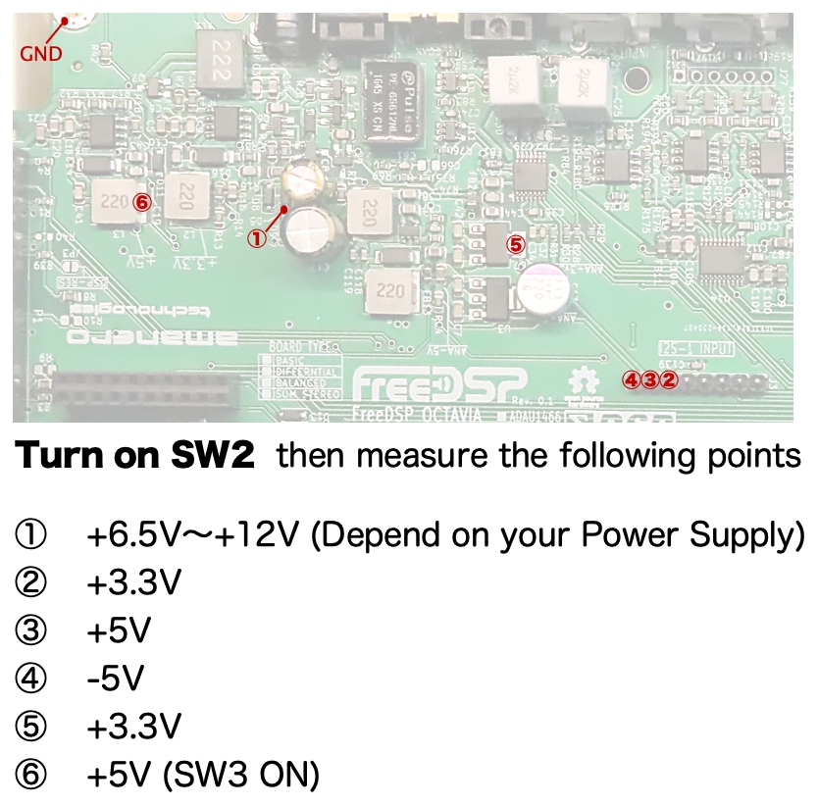
SOURCES/Documents/Figures/PowerRailCheck.jpg
