freeDSP/freeDSP-OCTAVIA/SOURCES/Documents/Figures/Removed_D13.jpg

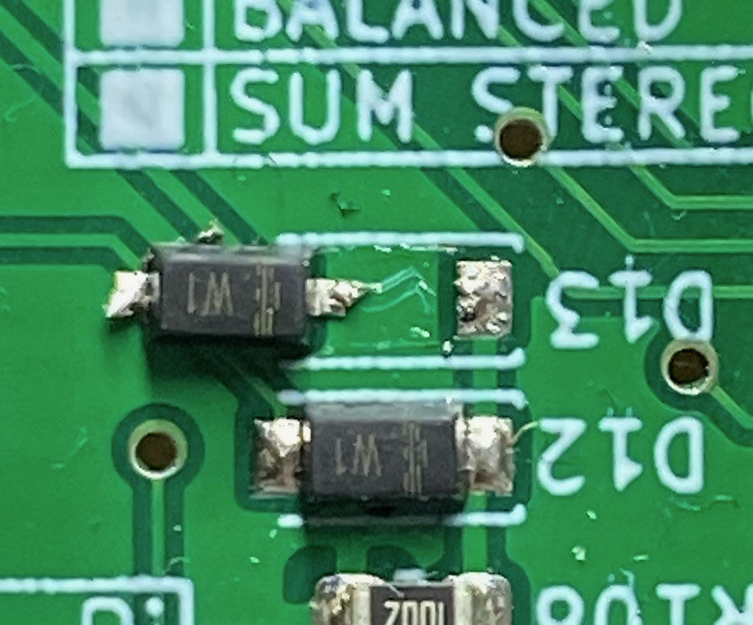
SOURCES/Documents/Figures/Removed_D13.jpg
