freeDSP/freeDSP-OCTAVIA/SOURCES/Documents/Figures/Reversed_D21.jpg

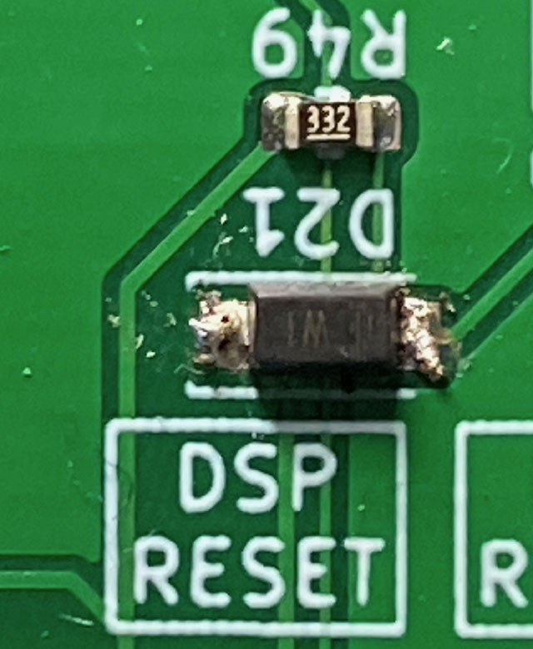
SOURCES/Documents/Figures/Reversed_D21.jpg
