freeDSP/freeDSP-OCTAVIA/SOURCES/Documents/Figures/SDPIF-Inputs.png

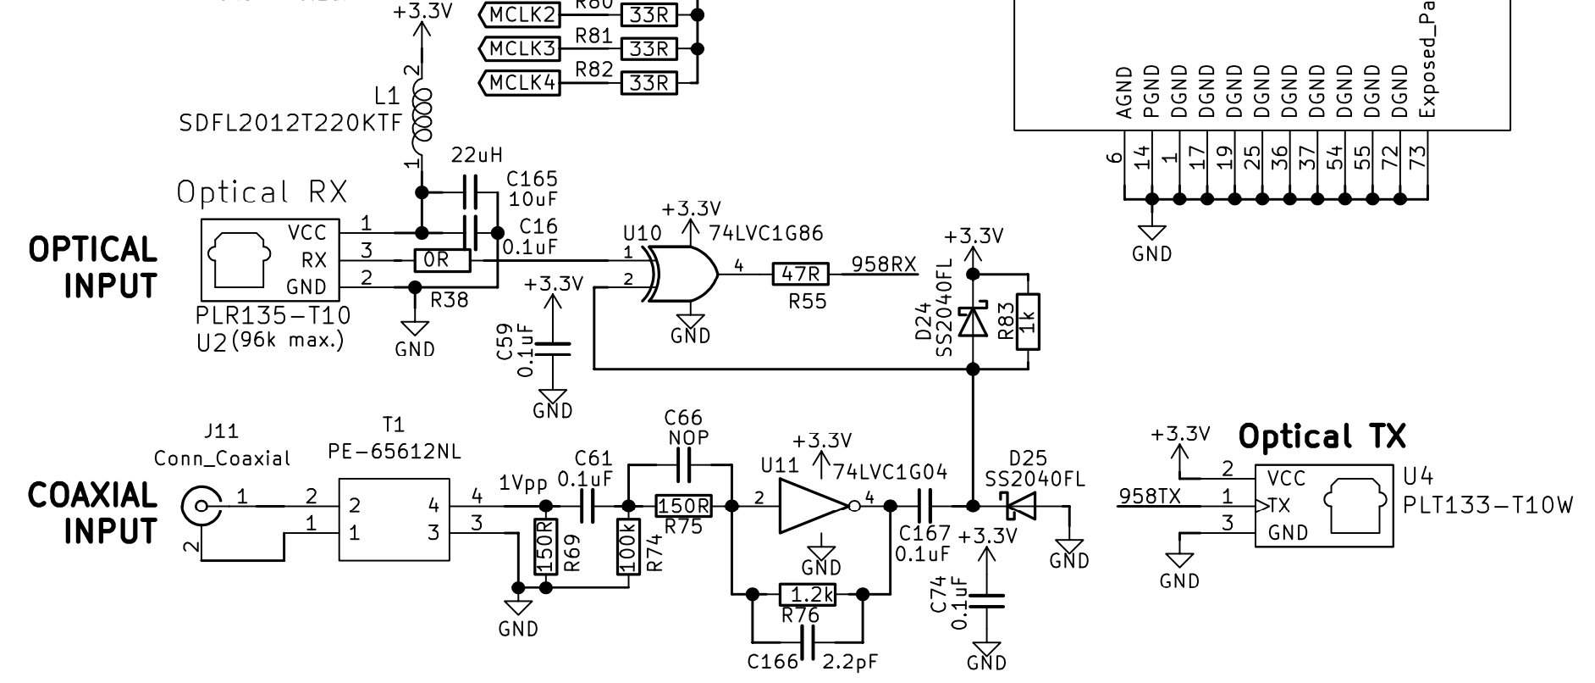
SOURCES/Documents/Figures/SDPIF-Inputs.png
