freeDSP/freeDSP-OCTAVIA/SOURCES/Documents/Figures/Select_USBi_I2C.gif

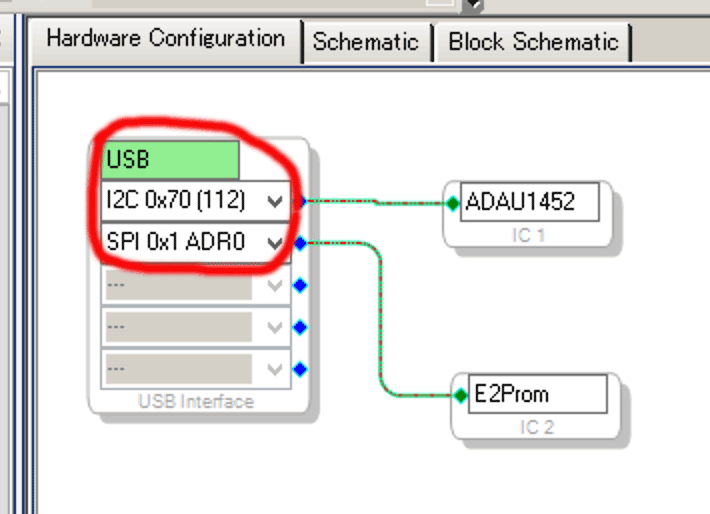
SOURCES/Documents/Figures/Select_USBi_I2C.gif
