freeDSP/freeDSP-OCTAVIA/SOURCES/Documents/Figures/SelectingWriteMenu.gif

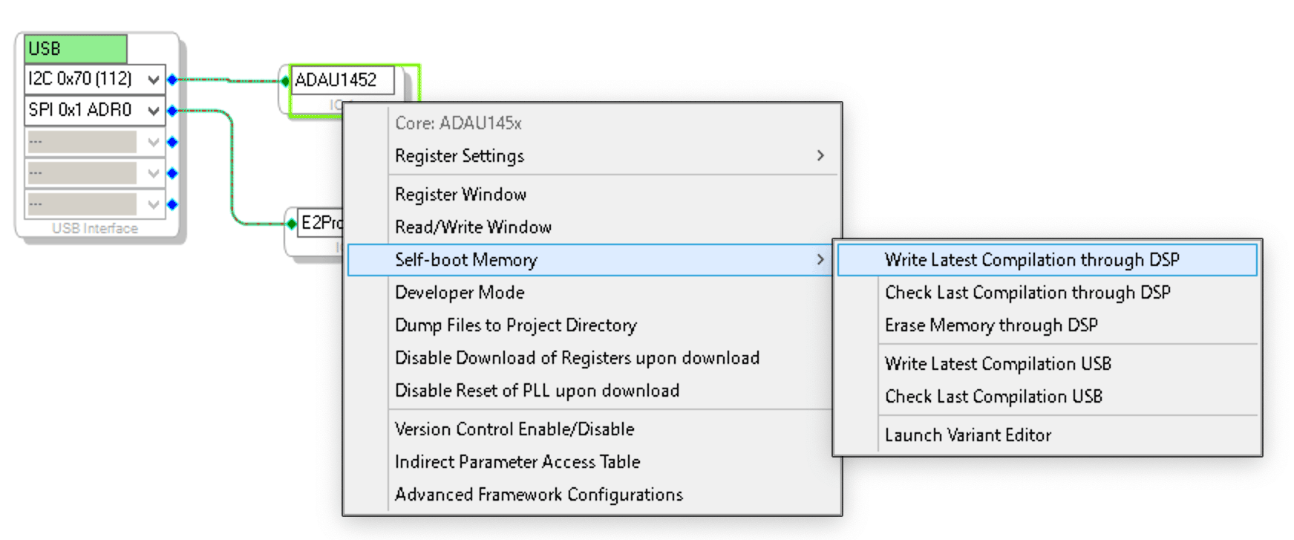
SOURCES/Documents/Figures/SelectingWriteMenu.gif
