freeDSP/freeDSP-OCTAVIA/SOURCES/Documents/Figures/Source-Position-Indicator-L.jpg

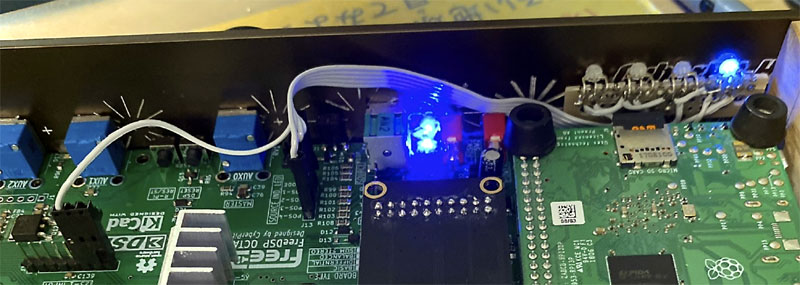
SOURCES/Documents/Figures/Source-Position-Indicator-L.jpg
