freeDSP/freeDSP-OCTAVIA/SOURCES/Documents/Figures/SourceSelectswitch.png

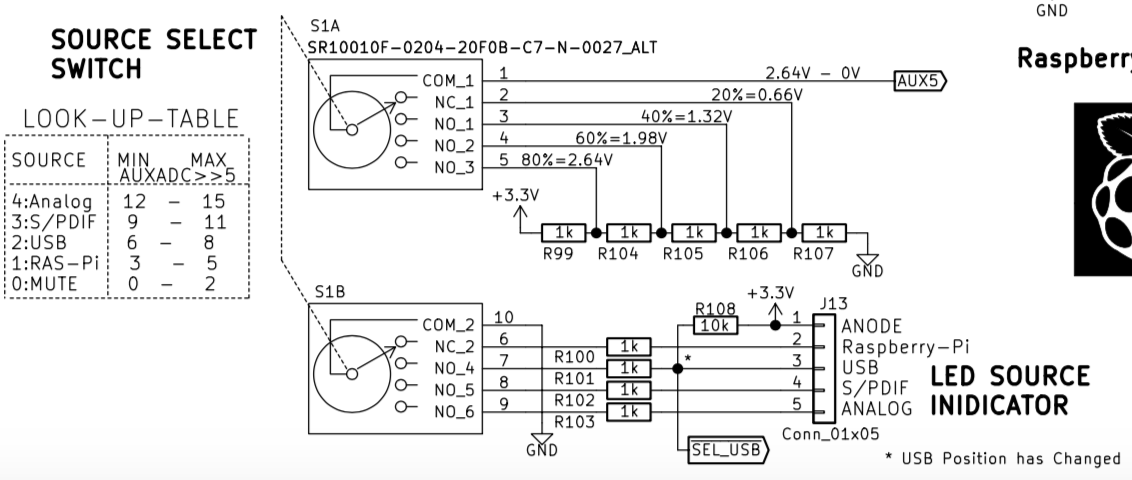
SOURCES/Documents/Figures/SourceSelectswitch.png
