freeDSP/freeDSP-OCTAVIA/SOURCES/Documents/Figures/Using_M95256_EEPROM.png

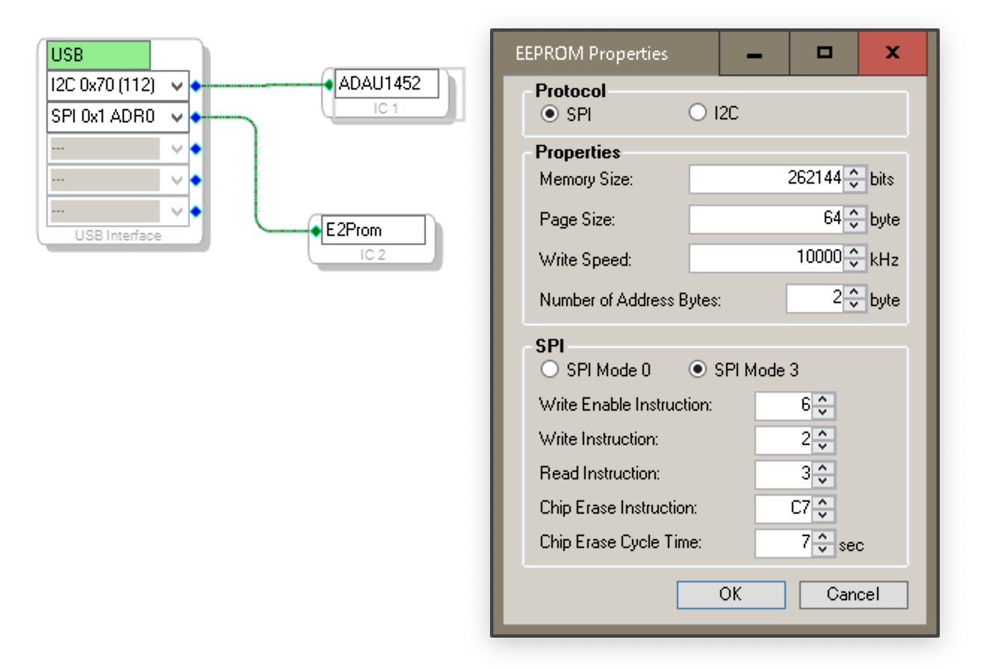
SOURCES/Documents/Figures/Using_M95256_EEPROM.png
