freeDSP/freeDSP-OCTAVIA/SOURCES/Documents/Figures/xmos2.jpg

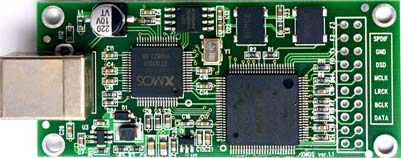
SOURCES/Documents/Figures/xmos2.jpg
