freeDSP/freeDSP-OCTAVIA/SOURCES/Documents/Figures/xmos.jpg

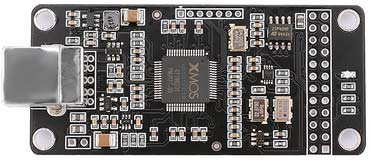
SOURCES/Documents/Figures/xmos.jpg
