freeDSP/freeDSP-OCTAVIA/SOURCES/Documents/Figures/サクル製7v5アダプタ2.jpg

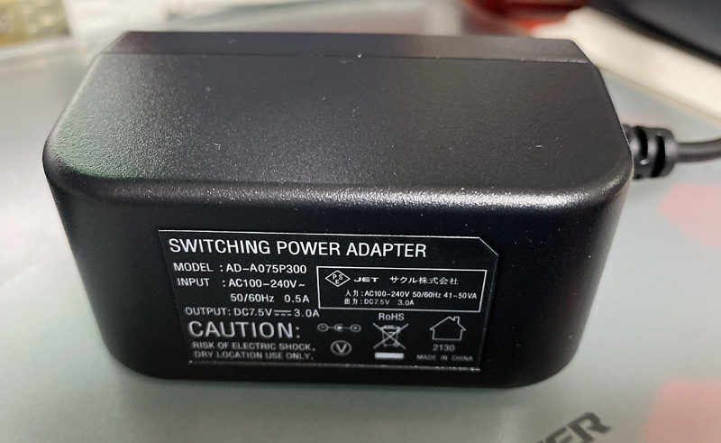
SOURCES/Documents/Figures/サクル製7v5アダプタ2.jpg
