freeDSP/freeDSP-OCTAVIA/SOURCES/Documents/Figures/実装済み基板画像FHD.jpg

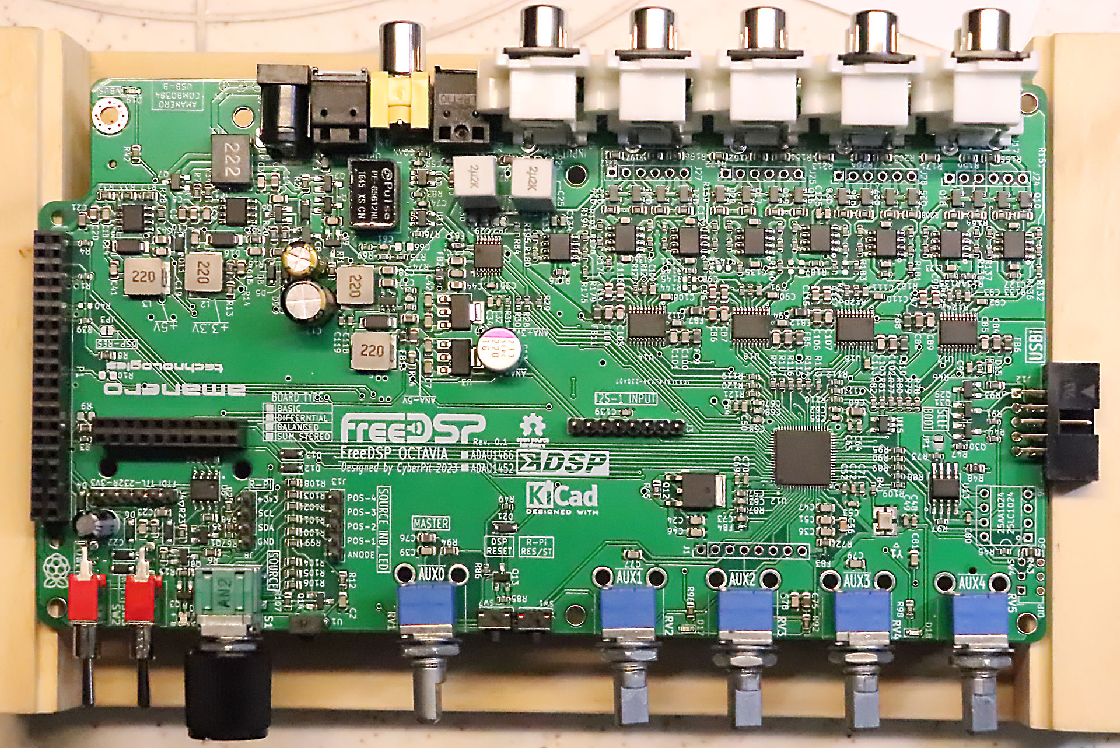
SOURCES/Documents/Figures/実装済み基板画像FHD.jpg
