freeDSP/freeDSP-OCTAVIA/SOURCES/IMAGES/FreeDSP OCTAVIA ParseRearVIew.jpg

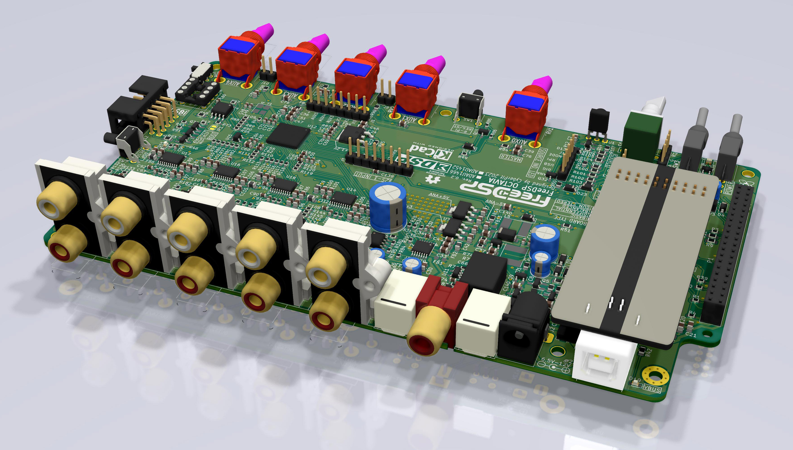
SOURCES/IMAGES/FreeDSP OCTAVIA ParseRearVIew.jpg
