freeDSP/freeDSP-OCTAVIA/SOURCES/IMAGES/FreeDSP OCTAVIA ParseVIew.jpg

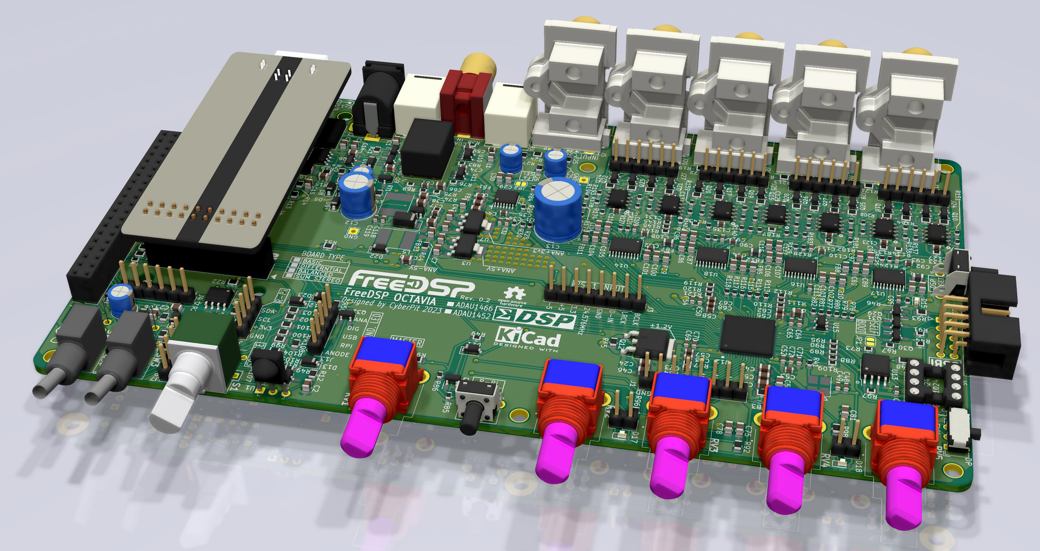
SOURCES/IMAGES/FreeDSP OCTAVIA ParseVIew.jpg
