freeDSP/freeDSP-OCTAVIA/SOURCES/IMAGES/FreeDSP OCTAVIA ParseVIew_L2.jpg

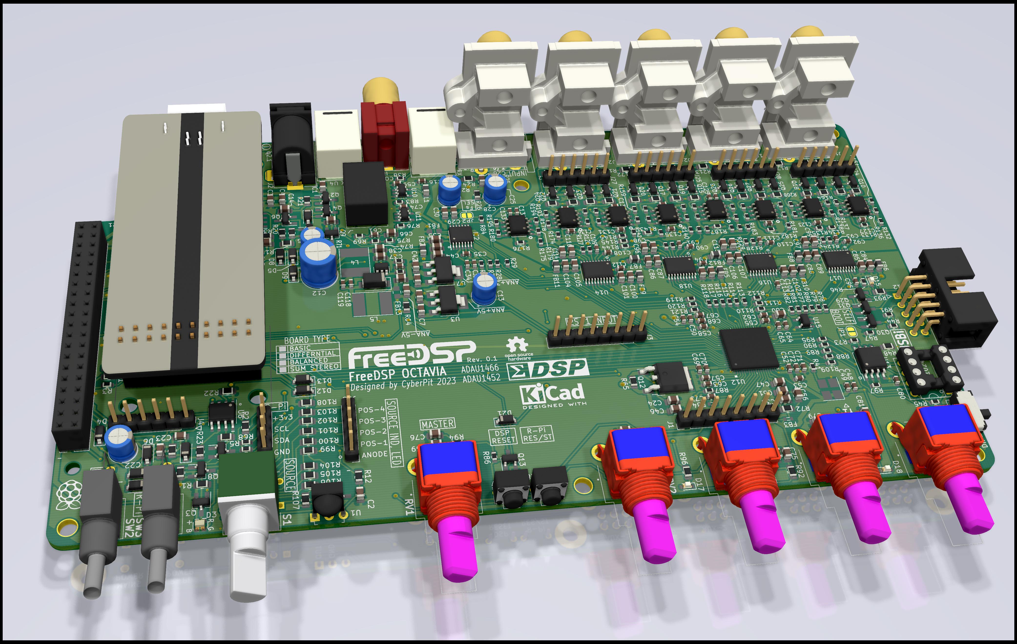
SOURCES/IMAGES/FreeDSP OCTAVIA ParseVIew_L2.jpg
