freeDSP/freeDSP-OCTAVIA/SOURCES/IMAGES/FreeDSP OCTAVIA ParseVIew_L.jpg

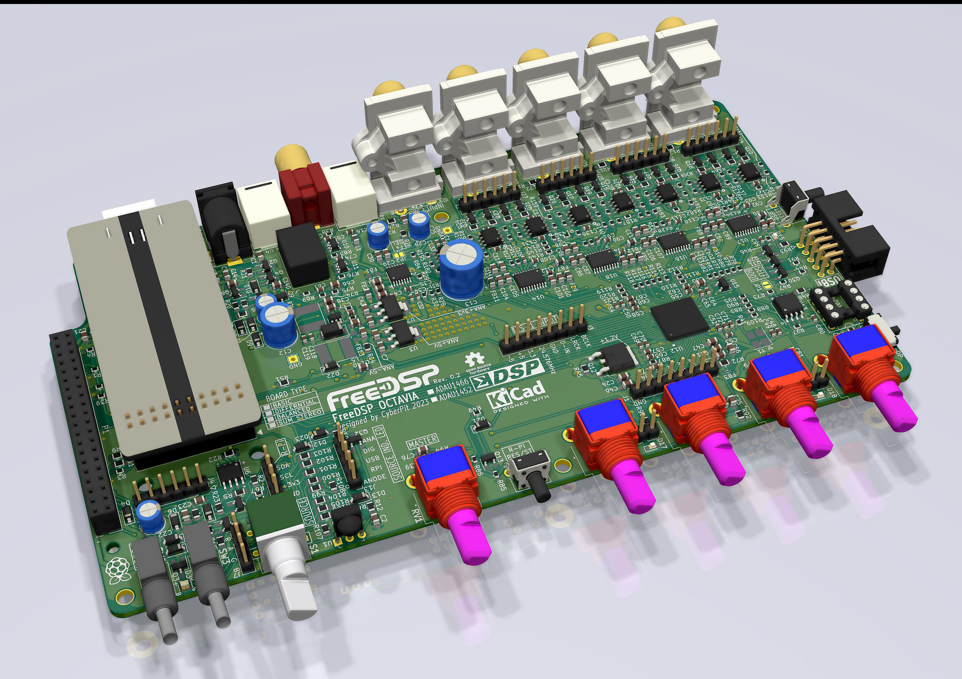
SOURCES/IMAGES/FreeDSP OCTAVIA ParseVIew_L.jpg
