freeDSP/freeDSP-OCTAVIA/SOURCES/IMAGES/FreeDSP_OCTAVIA_0v32_TopView.jpg

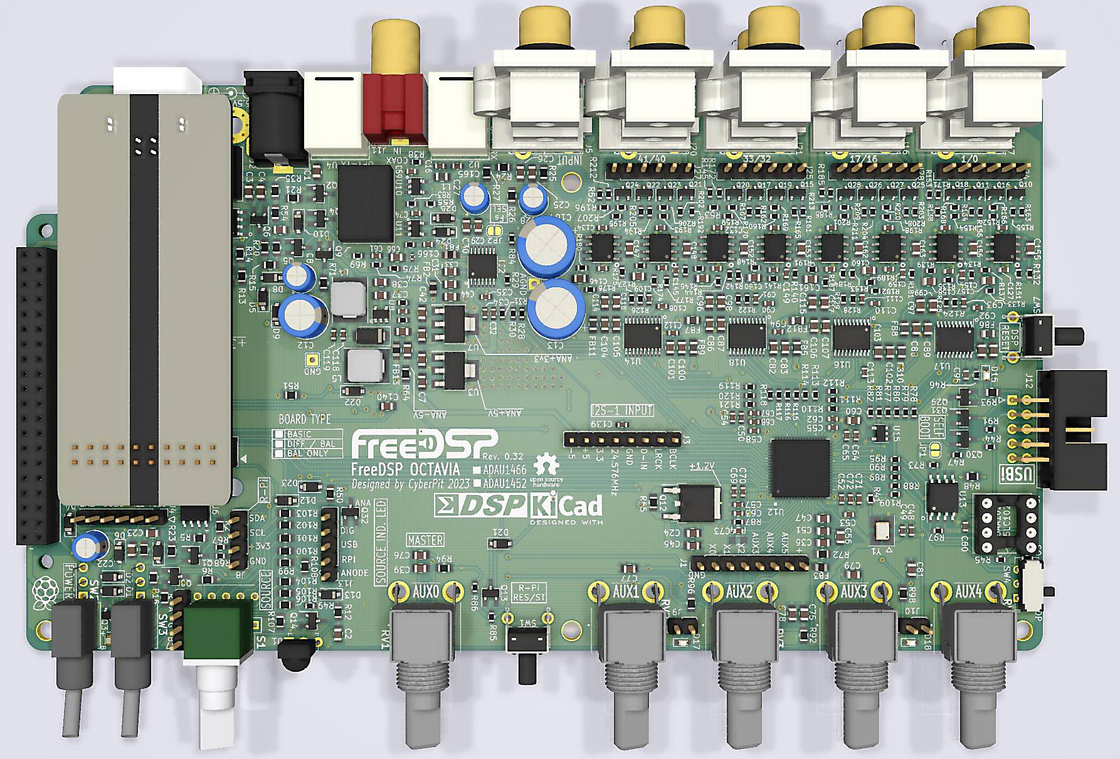
SOURCES/IMAGES/FreeDSP_OCTAVIA_0v32_TopView.jpg
