freeDSP/freeDSP-OCTAVIA/SOURCES/IMAGES/FreeDSP_OCTAVIA_BottomVIewRender.jpg

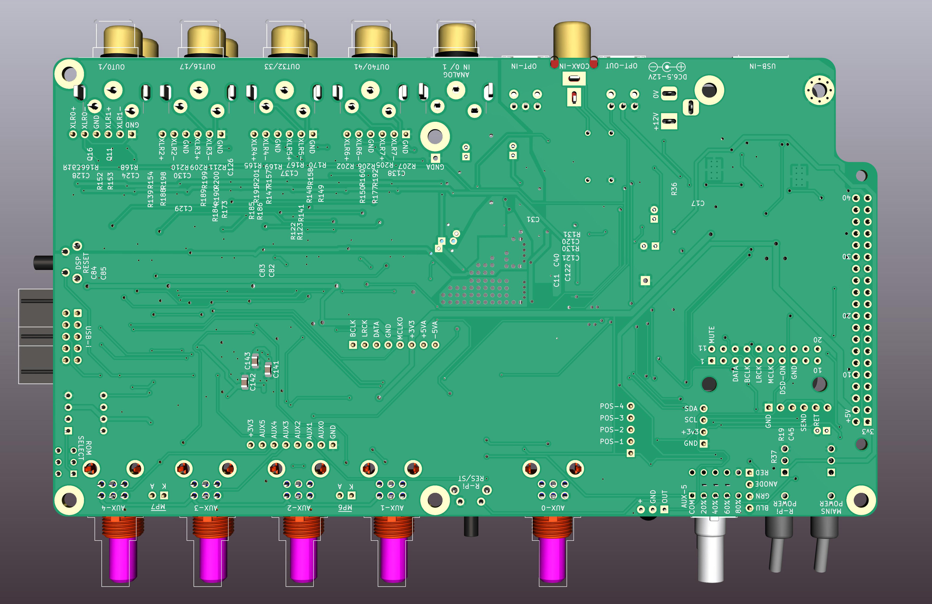
SOURCES/IMAGES/FreeDSP_OCTAVIA_BottomVIewRender.jpg
