freeDSP/freeDSP-OCTAVIA/SOURCES/IMAGES/FreeDSP_OCTAVIA_Running.JPG

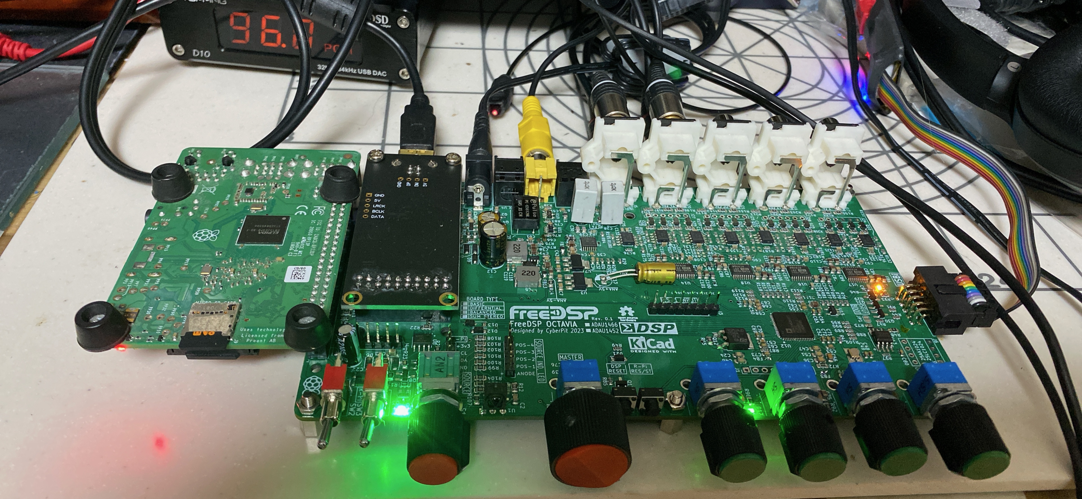
SOURCES/IMAGES/FreeDSP_OCTAVIA_Running.JPG
