freeDSP/freeDSP-OCTAVIA/SOURCES/IMAGES/FreeDSP_OCTAVIA_TopVIewRender.jpg

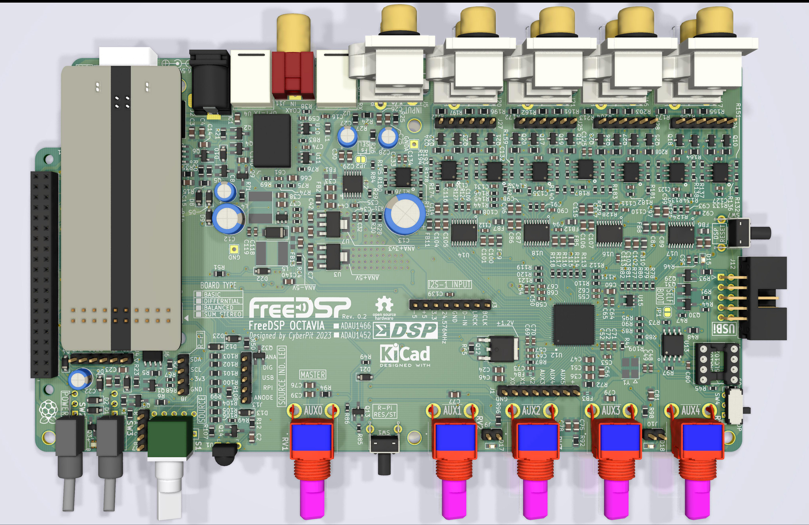
SOURCES/IMAGES/FreeDSP_OCTAVIA_TopVIewRender.jpg
