freeDSP/freeDSP-OCTAVIA/SOURCES/IMAGES/FreeDSP_OCTAVIA_withRPi.jpg

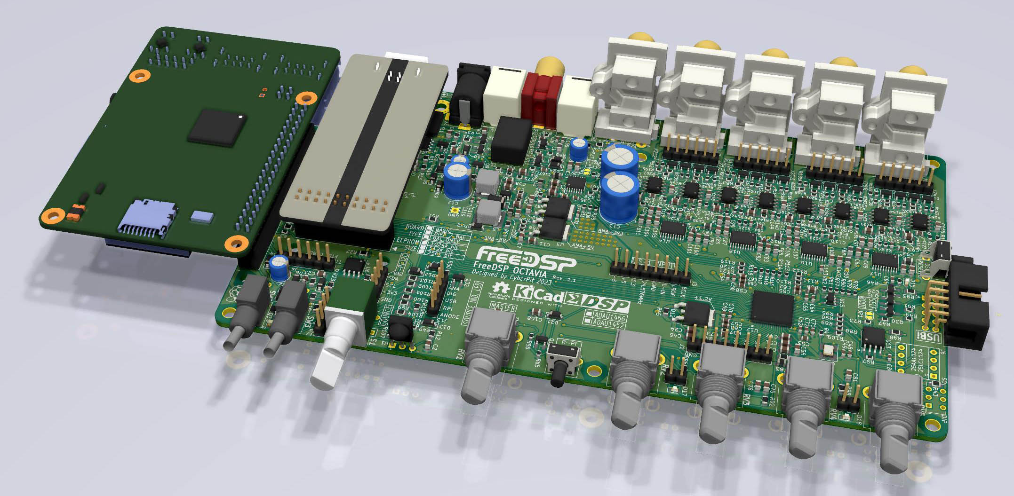
SOURCES/IMAGES/FreeDSP_OCTAVIA_withRPi.jpg
