freeDSP/freeDSP-OCTAVIA/SOURCES/IMAGES/FreeDSP_OCTAVIA_withRPi_FrontFaceView.jpg

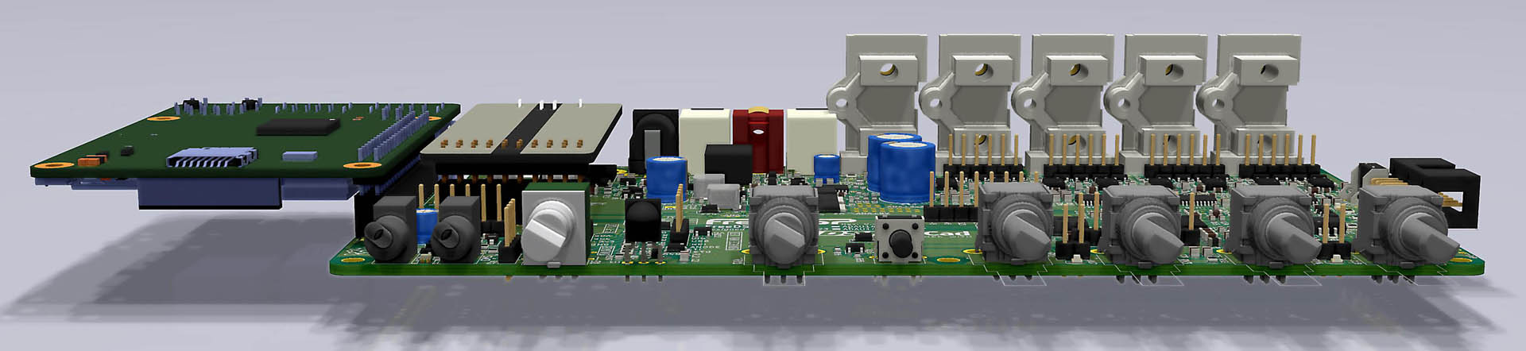
SOURCES/IMAGES/FreeDSP_OCTAVIA_withRPi_FrontFaceView.jpg
