freeDSP/freeDSP-OCTAVIA/SOURCES/IMAGES/FreeDSP_OCTAVIA_withRPi_RearFaceView.jpg

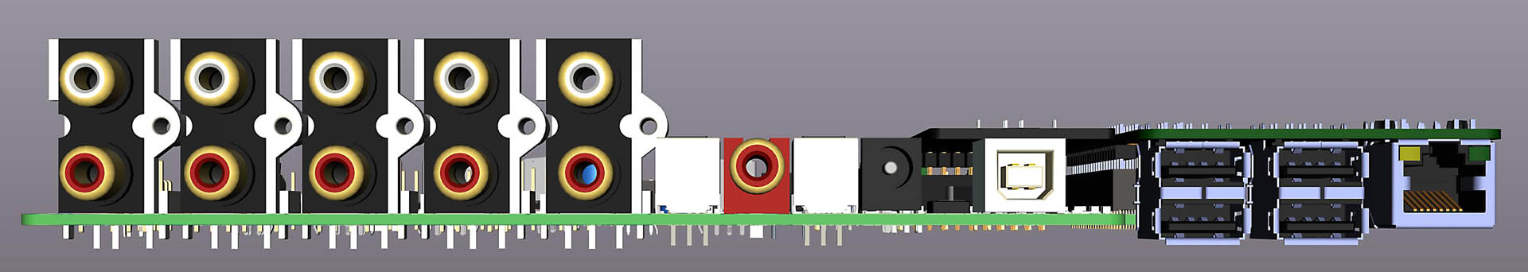
SOURCES/IMAGES/FreeDSP_OCTAVIA_withRPi_RearFaceView.jpg
