freeDSP/freeDSP-OCTAVIA/SOURCES/IMAGES/FreeDSP_OCTAVIA_withRPi_RearView.jpg

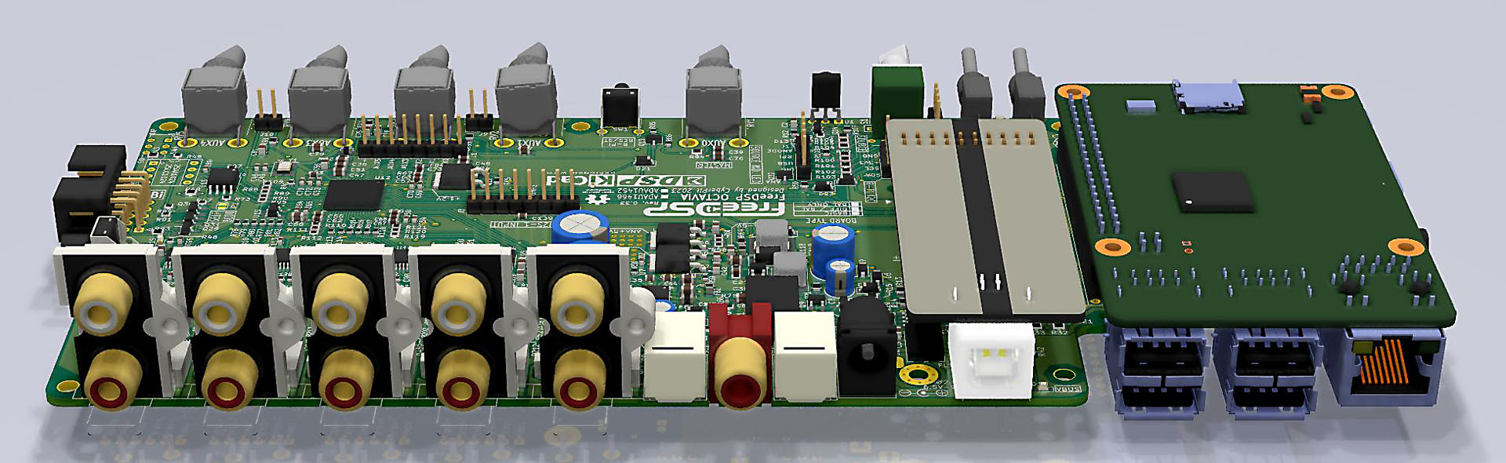
SOURCES/IMAGES/FreeDSP_OCTAVIA_withRPi_RearView.jpg
