freeDSP/freeDSP-OCTAVIA/SOURCES/kiCAD/FreeDSP_OCTAVIA_0v2_Schematic.pdf

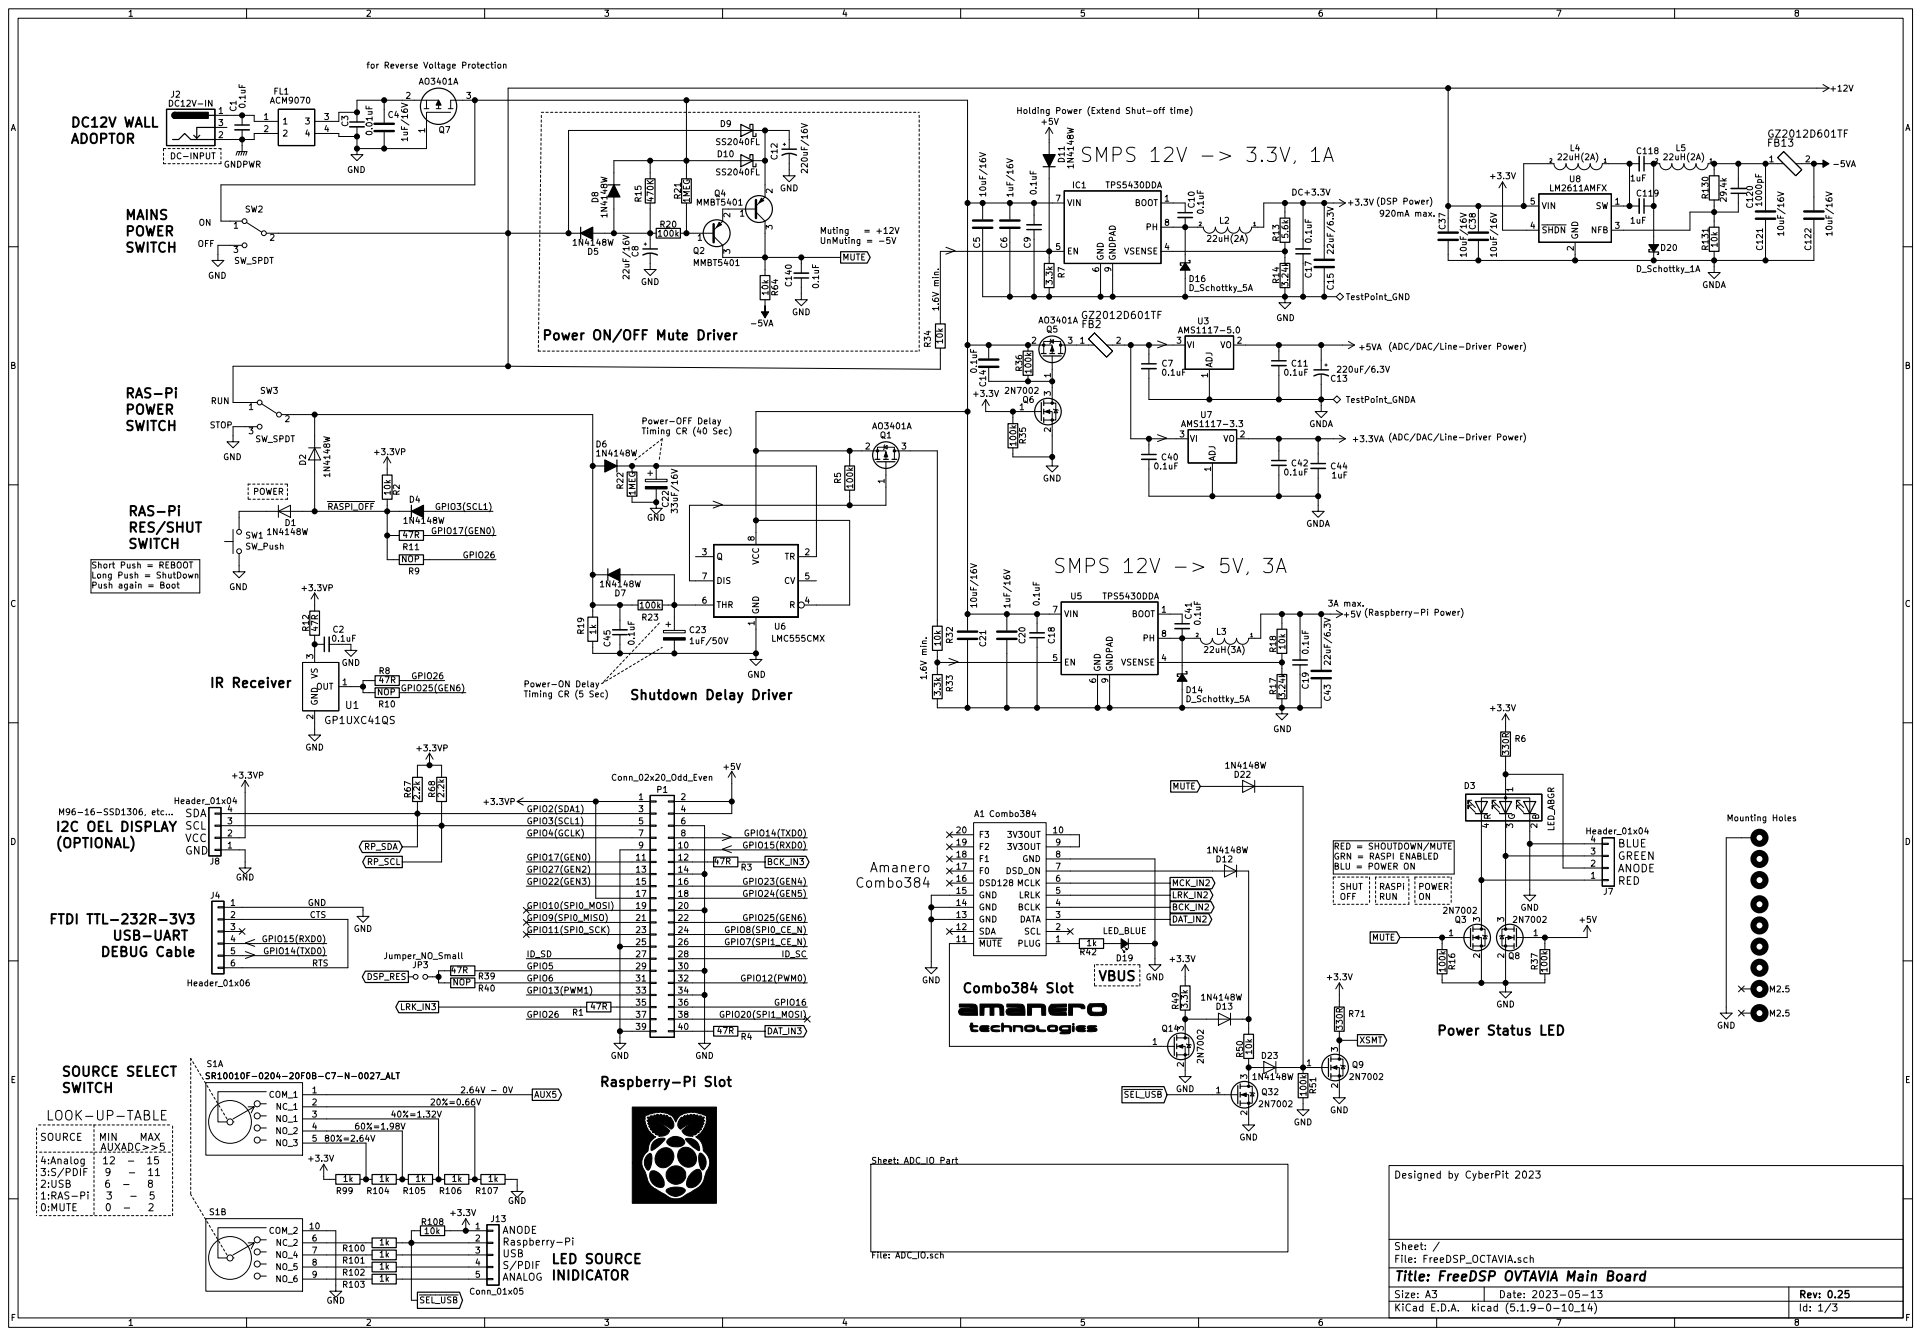
[picture p104: page 1]

for Reverse Voltage Protection

Holding Power (Extend Shut-off time)

Power ON/OFF Mute Driver

(ADC/DAC/Line-Driver Power)

RED = SHOUTDOWN/MUTE GRN = RASPI ENABLED

13 | 14
15 | 16 18 20
17

SOURCE MIN MAX | AUXADC>>5

4:Analog 12 - 15 3:S/PDIF 9 6 1:RAS-Pi 3 0:MUTE 0 - 2 | - 8 - 11 2:USB - 5

File: FreeDSP_OCTAVIA.sch Sheet: / Designed by CyberPit 2023 Sheet: ADC_IO Part File: ADC_IO.sch

Id: 1/3 Title: FreeDSP OVTAVIA Main Board

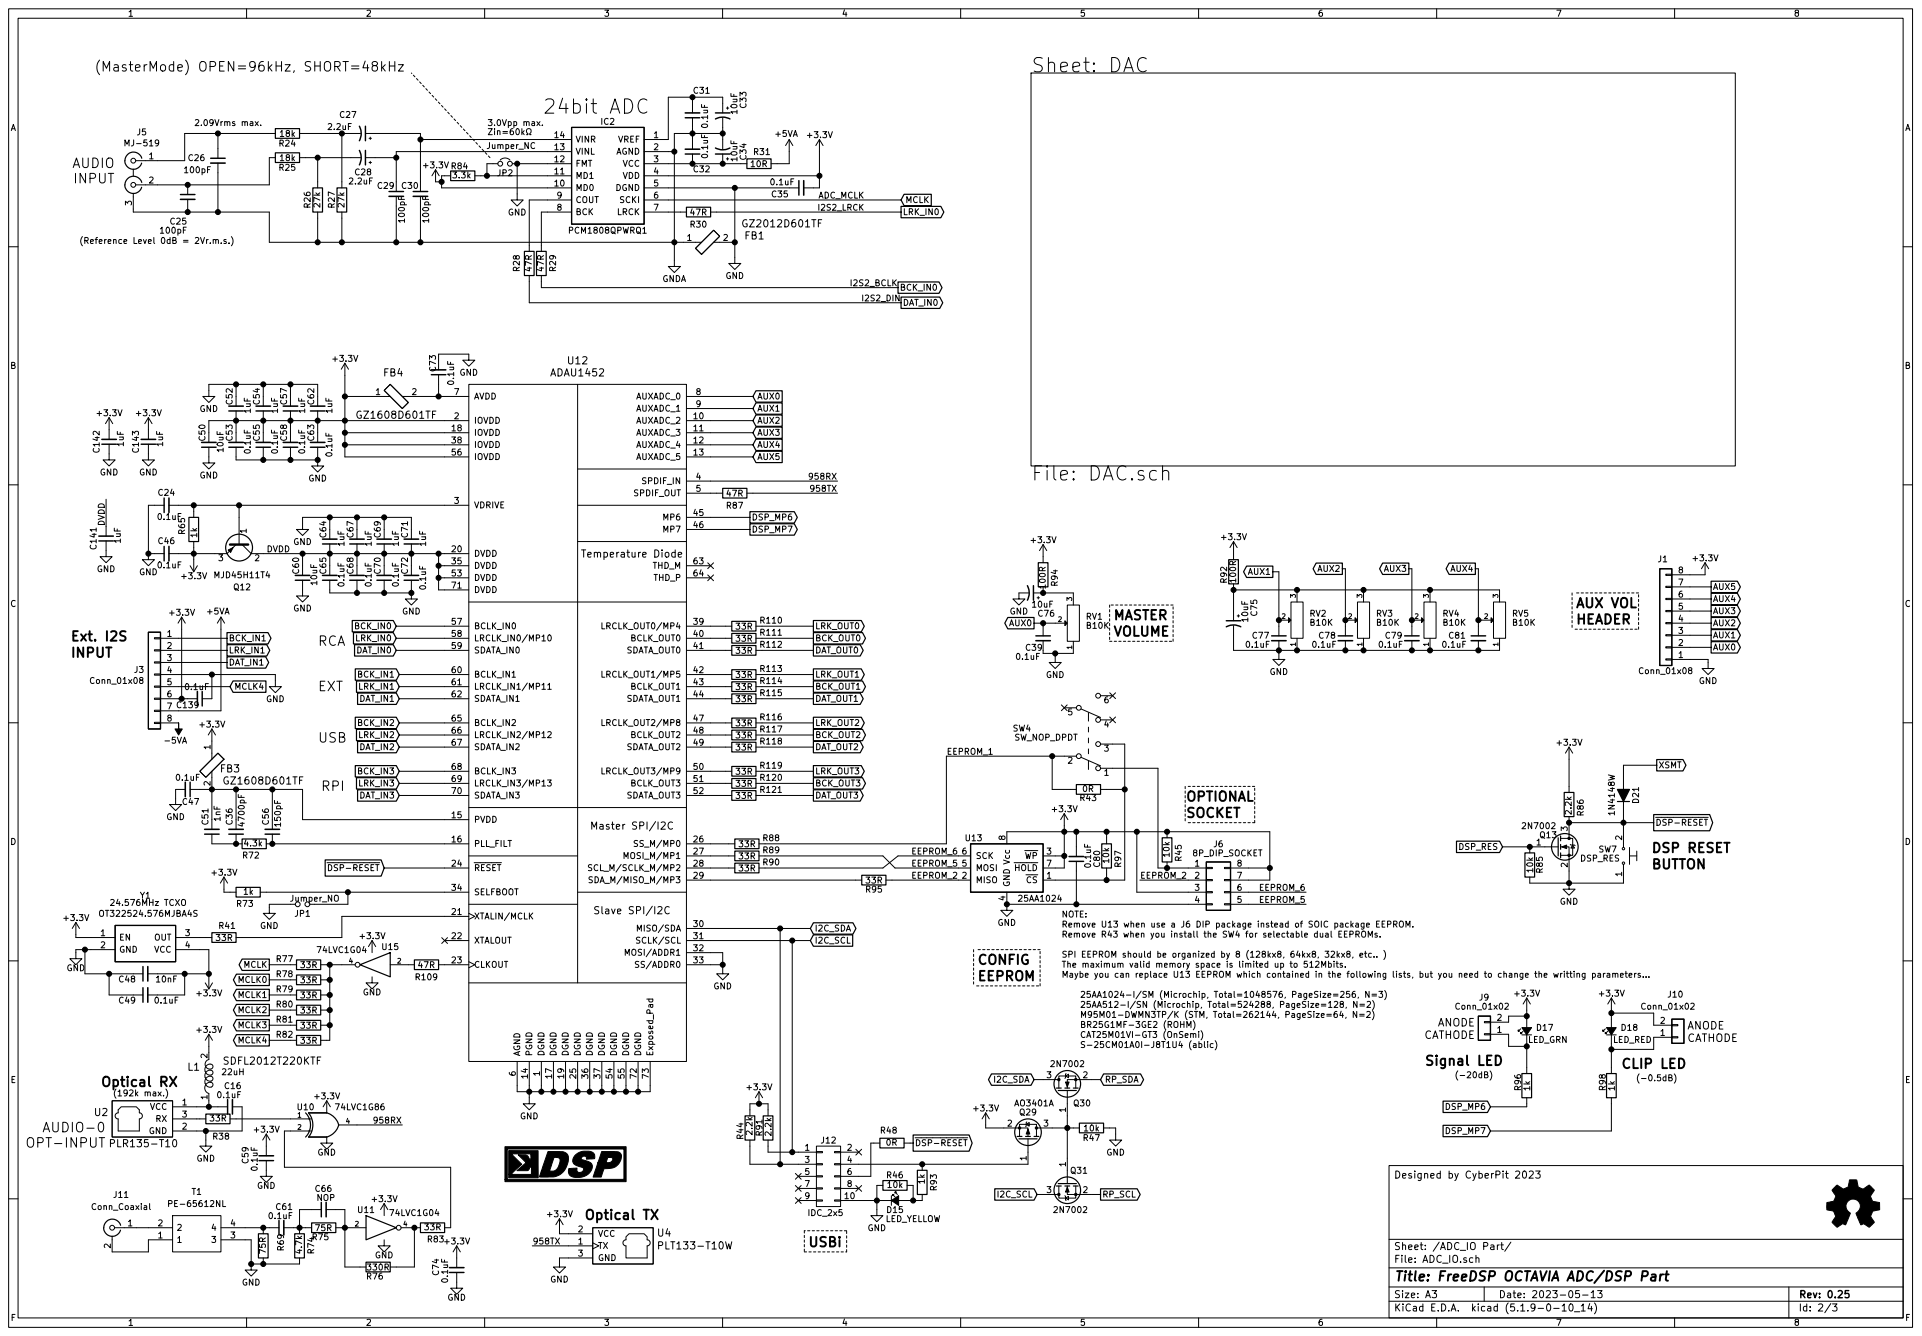
[picture p105: page 2]

6 AVDD 7 AUXADC_0 8 AUXADC_1 9 AUXADC_2 10 DVDD 20 MISO/SDA 30 BCLK_OUT0 40

5 | 0.1uF

4 MOSI 5 SCK 6 HOLD 7 Vcc U13 8

NOTE: Remove U13 when use a J6 DIP package instead of SOIC package EEPROM.

Remove R43 when you install the SW4 for selectable dual EEPROMs.

SPI EEPROM should be organized by 8 (128kx8, 64kx8, 32kx8, etc.. )
The maximum valid memory space is limited up to 512Mbits.
Maybe you can replace U13 EEPROM which contained in the following lists, but you need to change the writting parameters

25AA1024-I/SM (Microchip, Total=1048576, PageSize=256, N=3)
25AA512-I/SN (Microchip, Total=524288, PageSize=128, N=2)
M95M01-DWMN3TP/K (STM, Total=262144, PageSize=64, N=2)
BR25G1MF-3GE2 (ROHM)
CAT25M01VI-GT3 (OnSemi)
S-25CM01A0I-J8T1U4 (ablic)

Sheet: /ADC_IO Part/
File: ADC_IO.sch
Id: 2/3 Title: FreeDSP OCTAVIA ADC/DSP Part

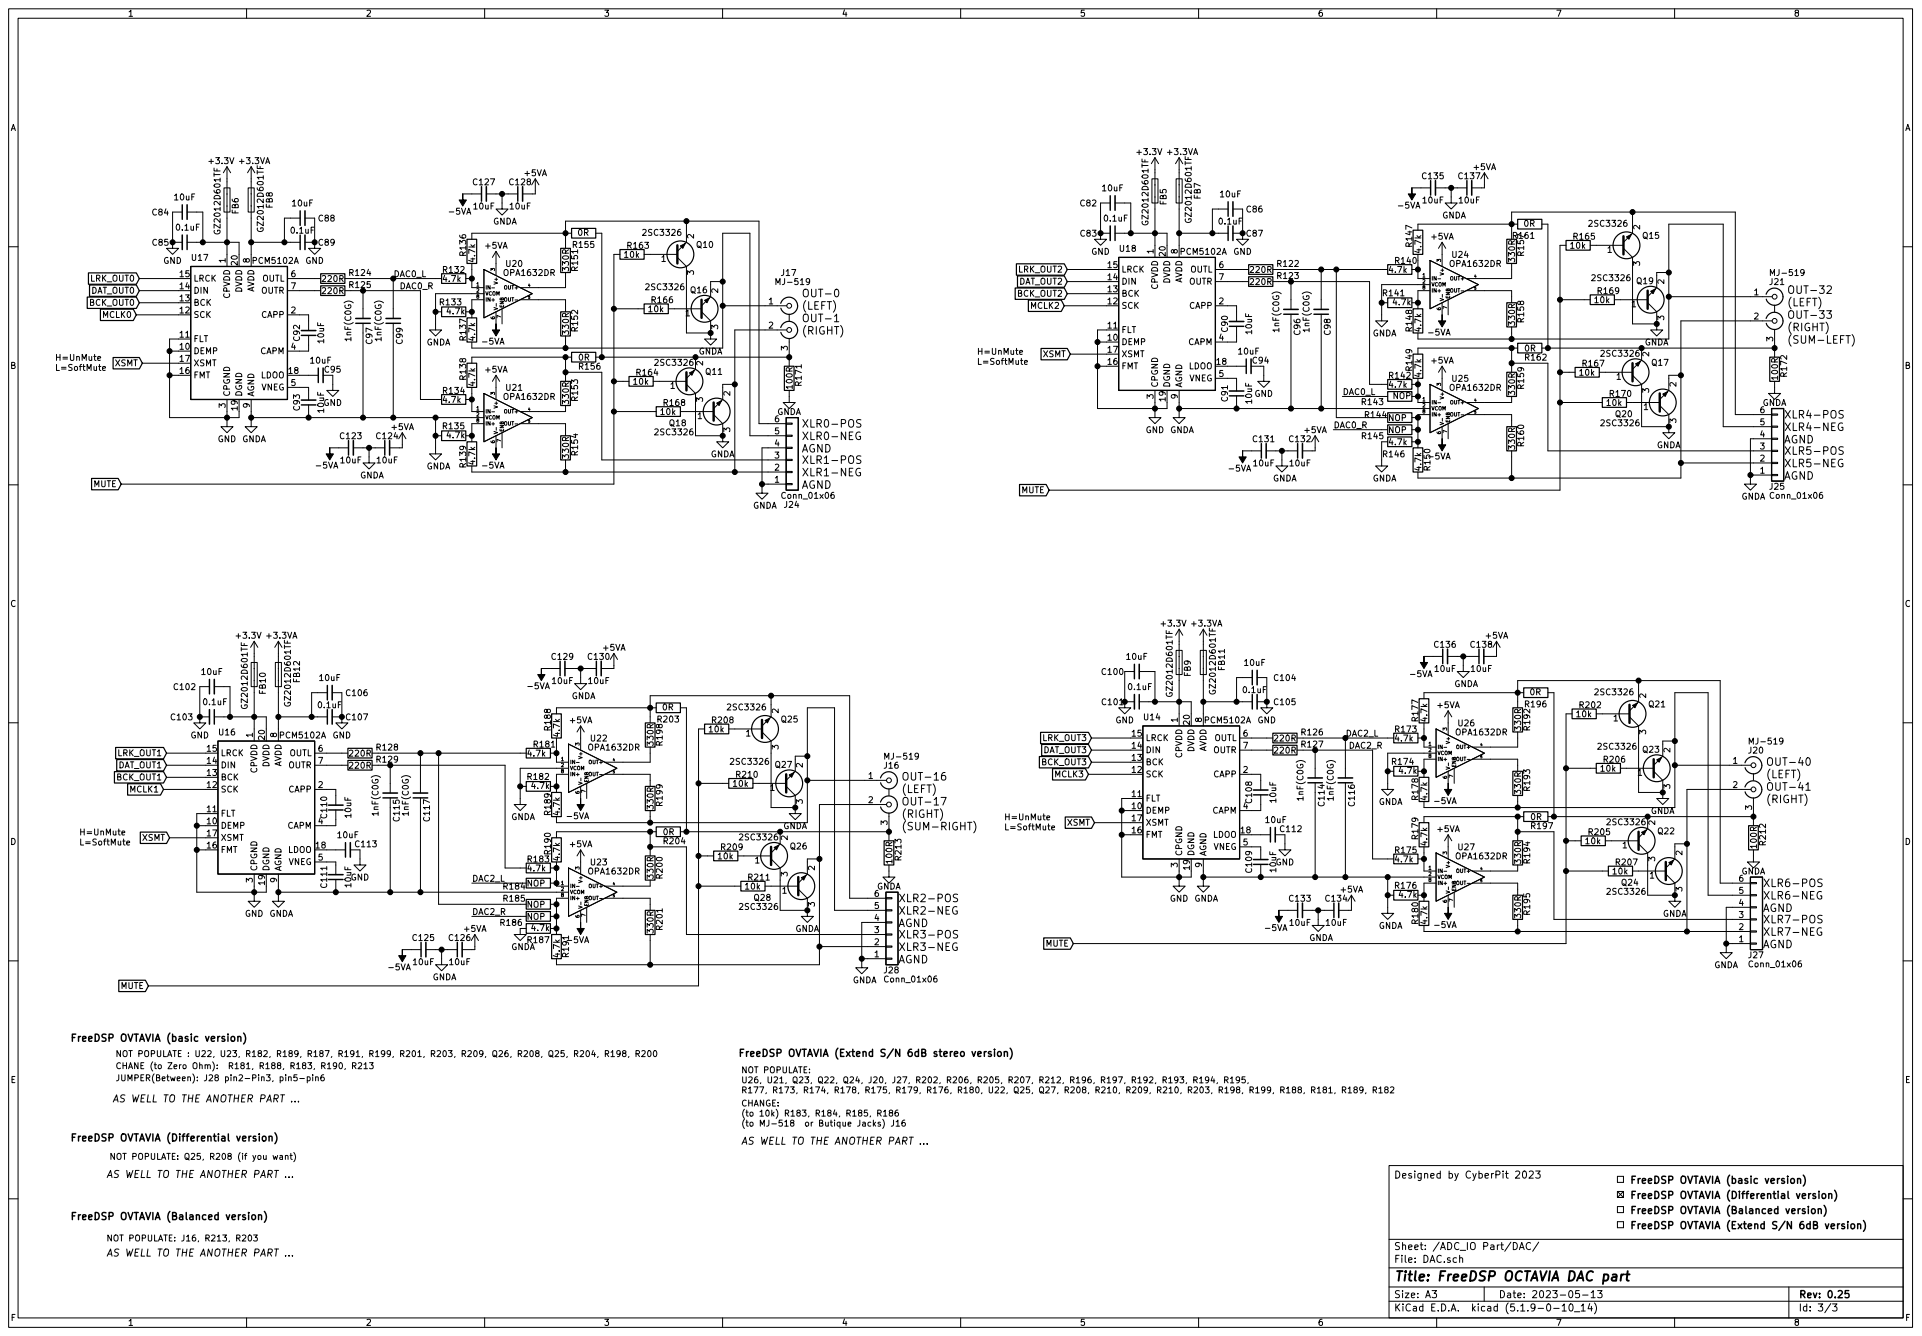
[picture p106: page 3]

1 DEMP 10 FLT 11 SCK 12 BCK 13 DIN 14

3 CAPM 4 VNEG 5 OUTL 6 OUTR 7 AVDD

CHANE (to Zero Ohm): R181, R188, R183, R190, R213 NOT POPULATE : U22, U23, R182, R189, R187, R191, R199, R201, R203, R209, Q26, R208, Q25, R204, R198, R200 FreeDSP OVTAVIA (basic version)

FreeDSP OVTAVIA (Extend S/N 6dB stereo version) NOT POPULATE: U26, U21, Q23, Q22, Q24, J20, J27, R202, R206, R205, R207, R212, R196, R197, R192, R193, R194, R195, R177, R173, R174, R178, R175, R179, R176, R180, U22, Q25, Q27, R208, R210, R209, R210, R203, R198, R199, R188, R181, R189, R182 CHANGE: (to 10k) R183, R184, R185, R186

FreeDSP OVTAVIA (Differential version) NOT POPULATE: J16, R213, R203 NOT POPULATE: Q25, R208 (if you want) AS WELL TO THE ANOTHER PART FreeDSP OVTAVIA (Differential version)

(to MJ-518 or Butique Jacks) J16

FreeDSP OVTAVIA (basic version)

Id: 3/3 Title: FreeDSP OCTAVIA DAC part File: DAC.sch Sheet: /ADC_IO Part/DAC/

AS WELL TO THE ANOTHER PART
