freeDSP/freeDSP-OCTAVIA/SOURCES/Documents/Figures/FreeDSP_OCTAVIA_0v1_Schematic_BW.pdf

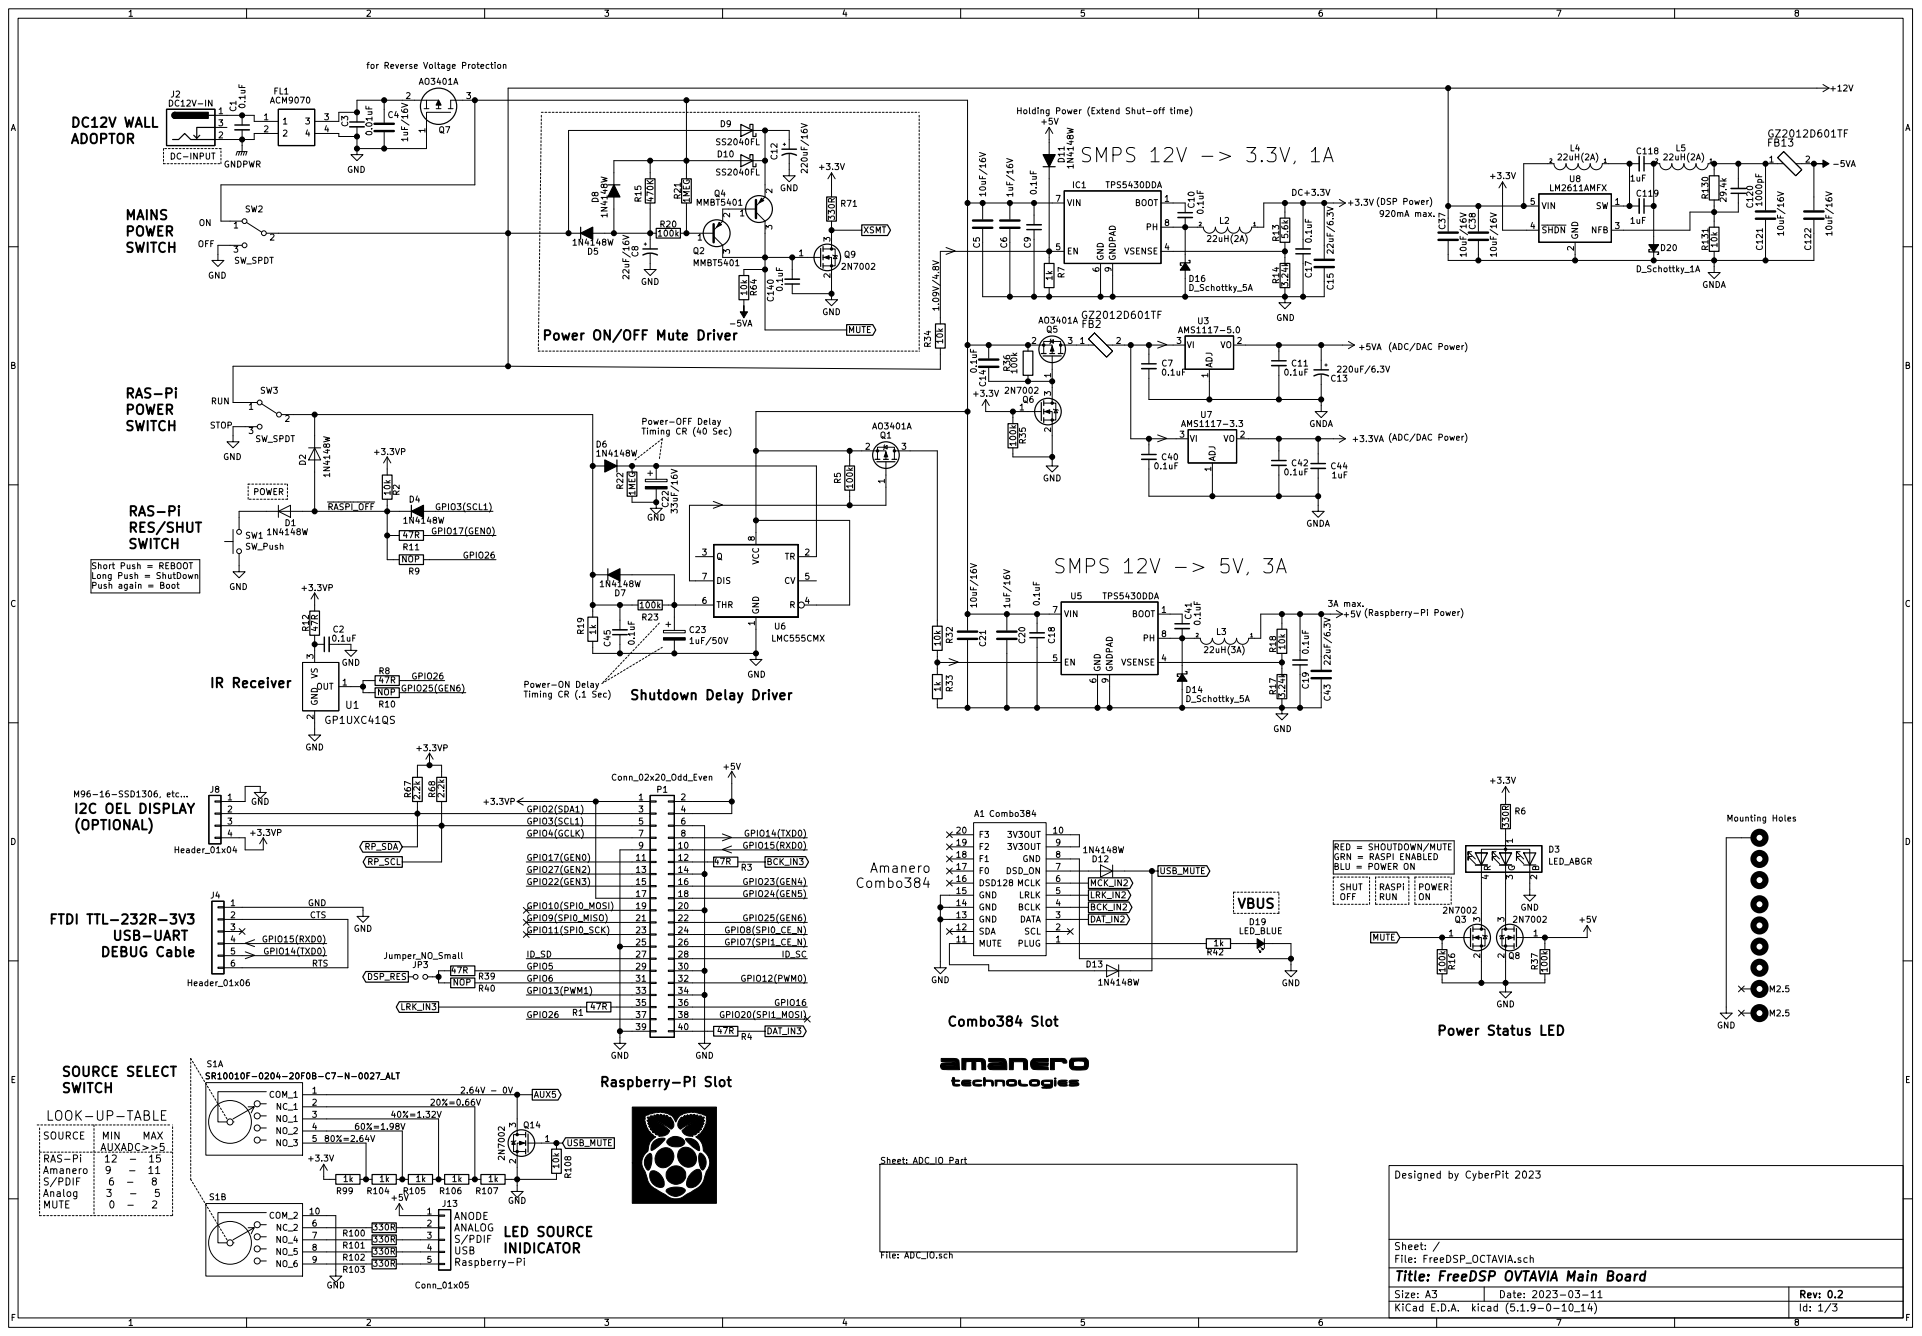
[picture p113: page 1]

for Reverse Voltage Protection

Holding Power (Extend Shut-off time)
SMPS 12V -> 3.3V, 1A

RASPi RUN RAS-Pi
POWER
SWITCH

3 | GPIO3(SCL1)

BLU = POWER ON VBUS

File: FreeDSP_OCTAVIA.sch Sheet: / Designed by CyberPit 2023 Sheet: ADC_IO Part File: ADC_IO.sch

Id: 1/3 Title: FreeDSP OVTAVIA Main Board

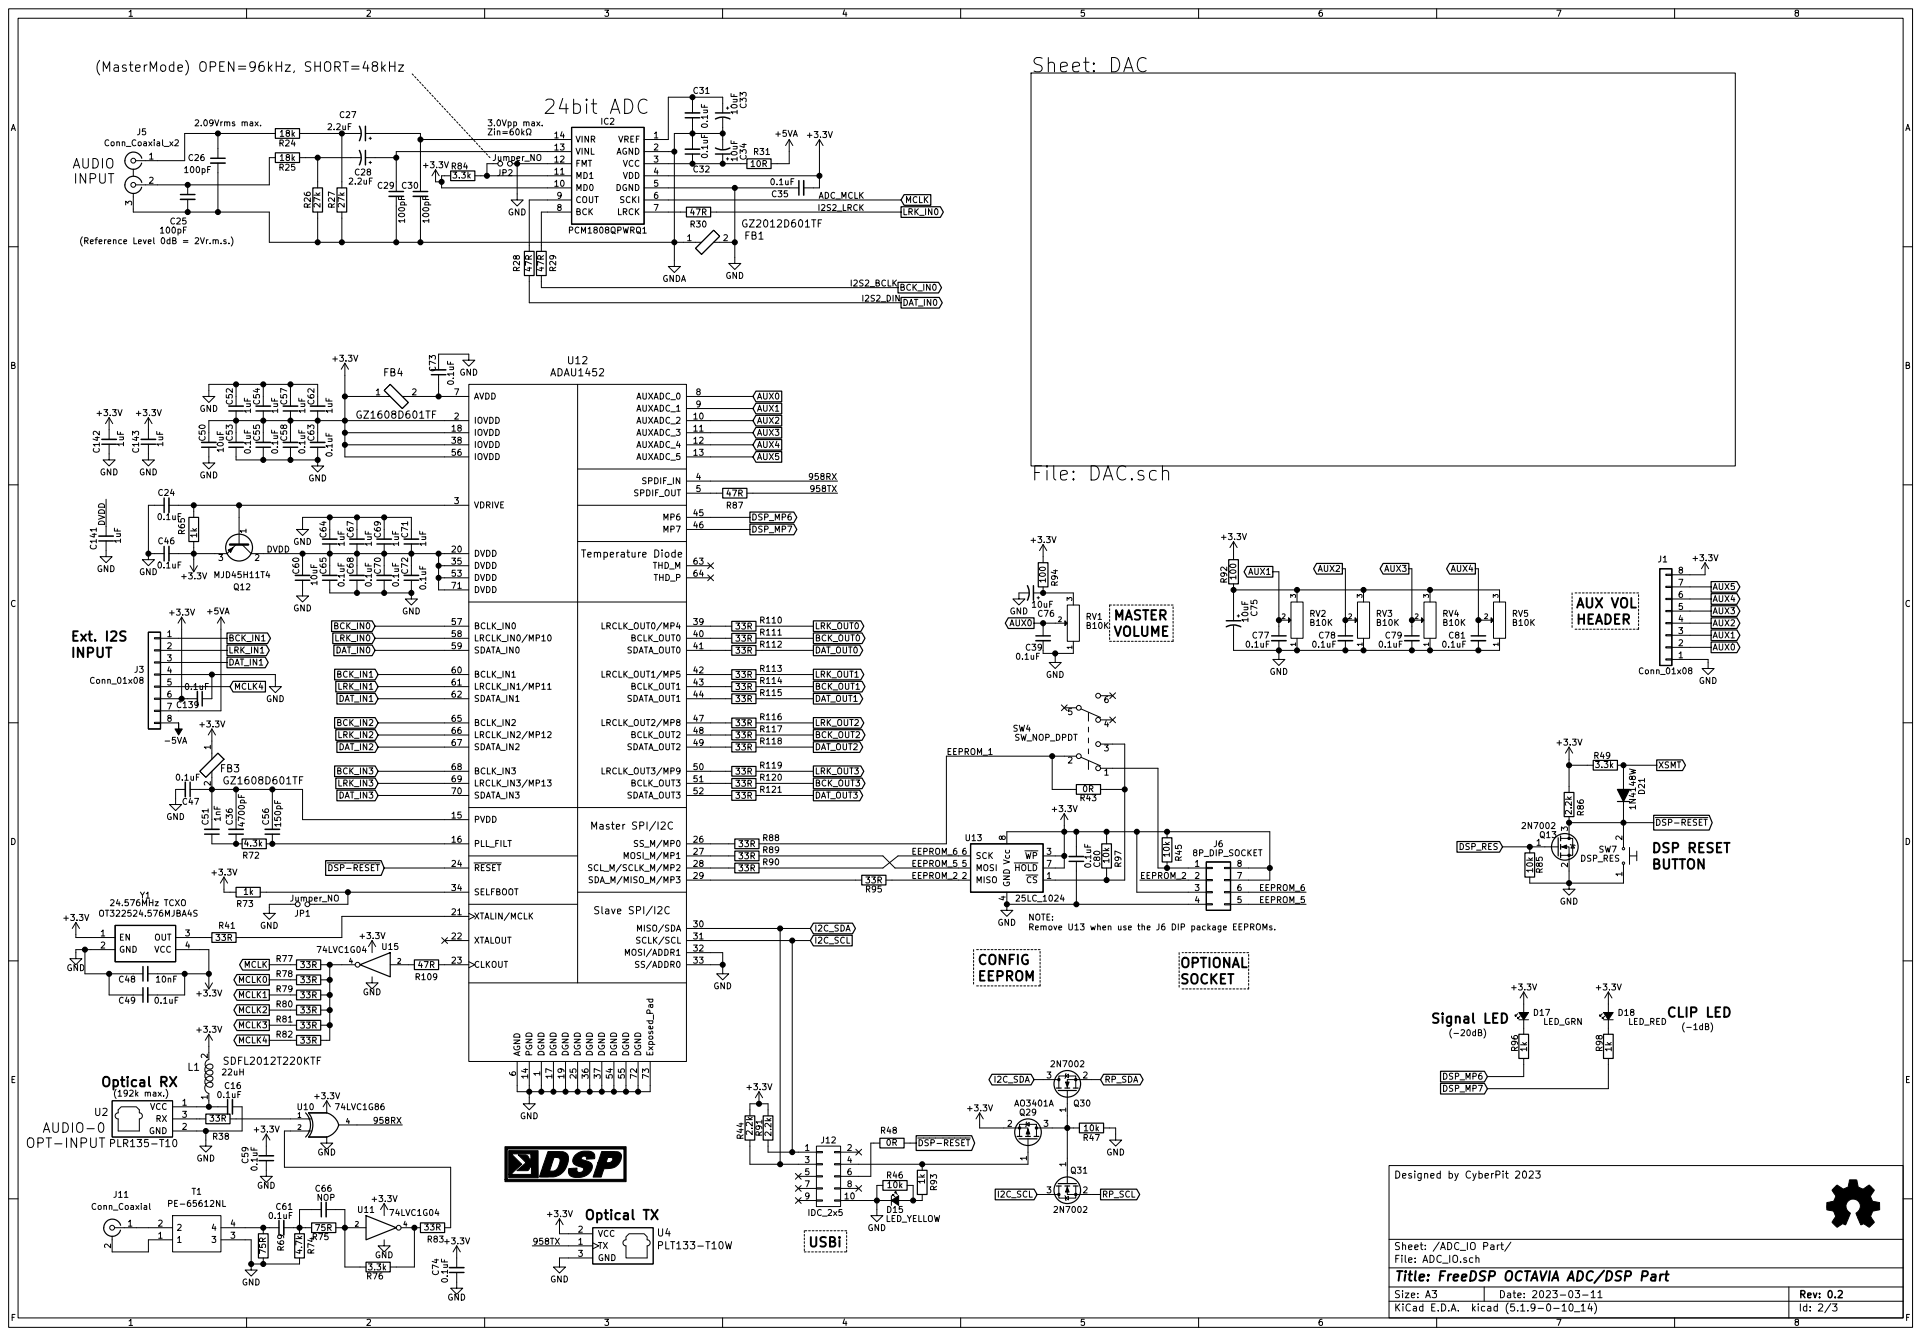
[picture p114: page 2]

6 AVDD 7 AUXADC_0 8 AUXADC_1 9 AUXADC_2 10 DVDD 20 MISO/SDA 30 BCLK_OUT0 40

5 | 0.1uF

4 MOSI 5 SCK 6 HOLD 7 Vcc U13 8

NOTE: Remove U13 when use the J6 DIP package EEPROMs.

Sheet: /ADC_IO Part/
File: ADC_IO.sch
Id: 2/3 Title: FreeDSP OCTAVIA ADC/DSP Part

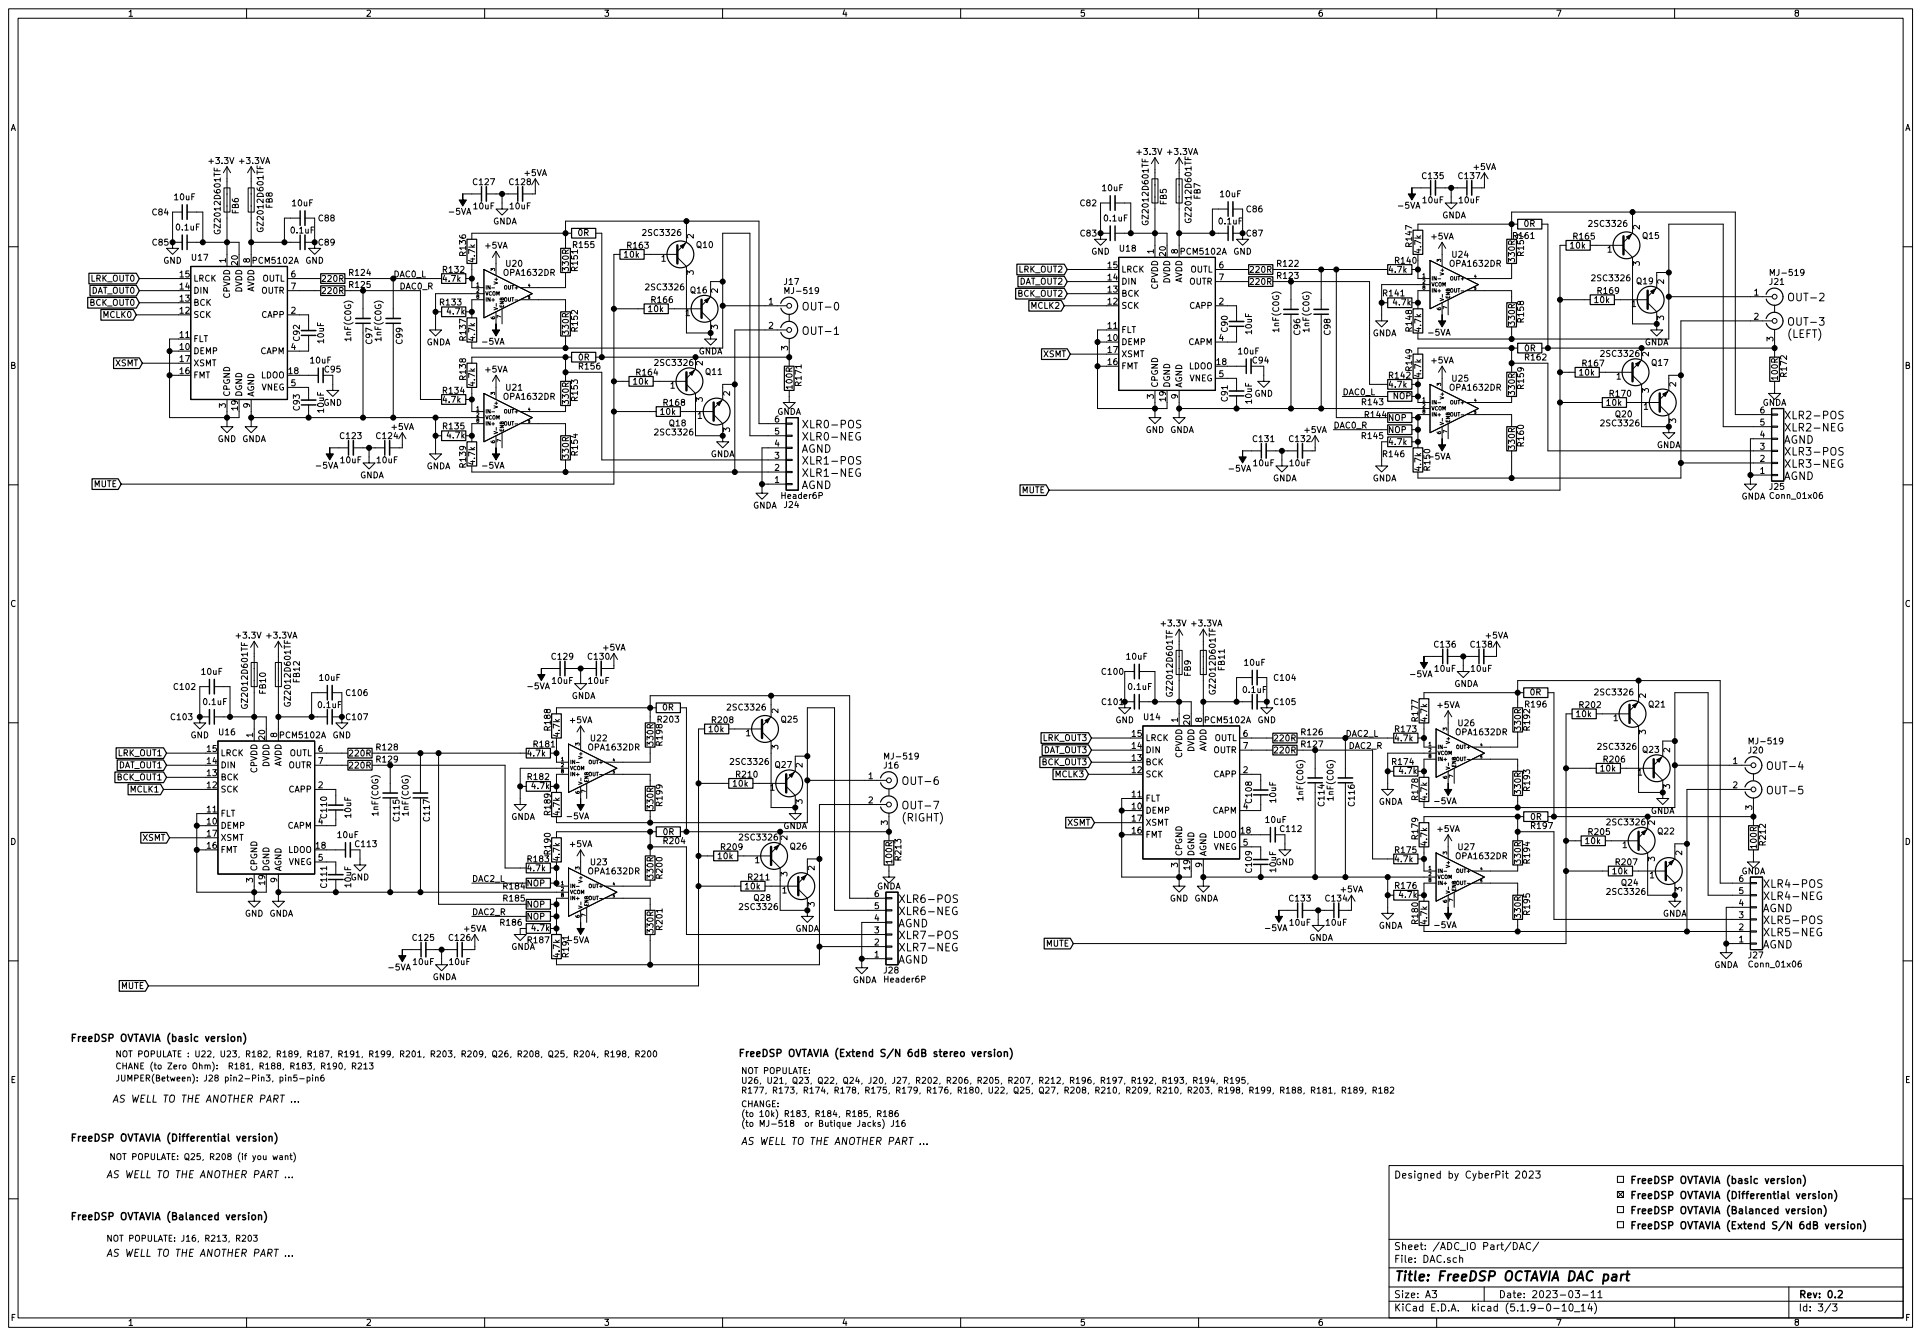
[picture p115: page 3]

1 DEMP 10 FLT 11 SCK 12 BCK 13 DIN 14

3 CAPM 4 VNEG 5 OUTL 6 OUTR 7 AVDD

DAC2_L FreeDSP OVTAVIA (basic version) NOT POPULATE : U22, U23, R182, R189, R187, R191, R199, R201, R203, R209, Q26, R208, Q25, R204, R198, R200 CHANE (to Zero Ohm): R181, R188, R183, R190, R213

FreeDSP OVTAVIA (Differential version) AS WELL TO THE ANOTHER PART NOT POPULATE: Q25, R208 (if you want)

FreeDSP OVTAVIA (basic version)
FreeDSP OVTAVIA (Differential version)

FreeDSP OVTAVIA (Balanced version)

FreeDSP OVTAVIA (Extend S/N 6dB version)

Id: 3/3 Title: FreeDSP OCTAVIA DAC part File: DAC.sch Sheet: /ADC_IO Part/DAC/
