freeDSP/freeDSP-OCTAVIA/SOURCES/Chassis/FreeDSP_OCTAVIA_TopOverlay_0v2.pdf

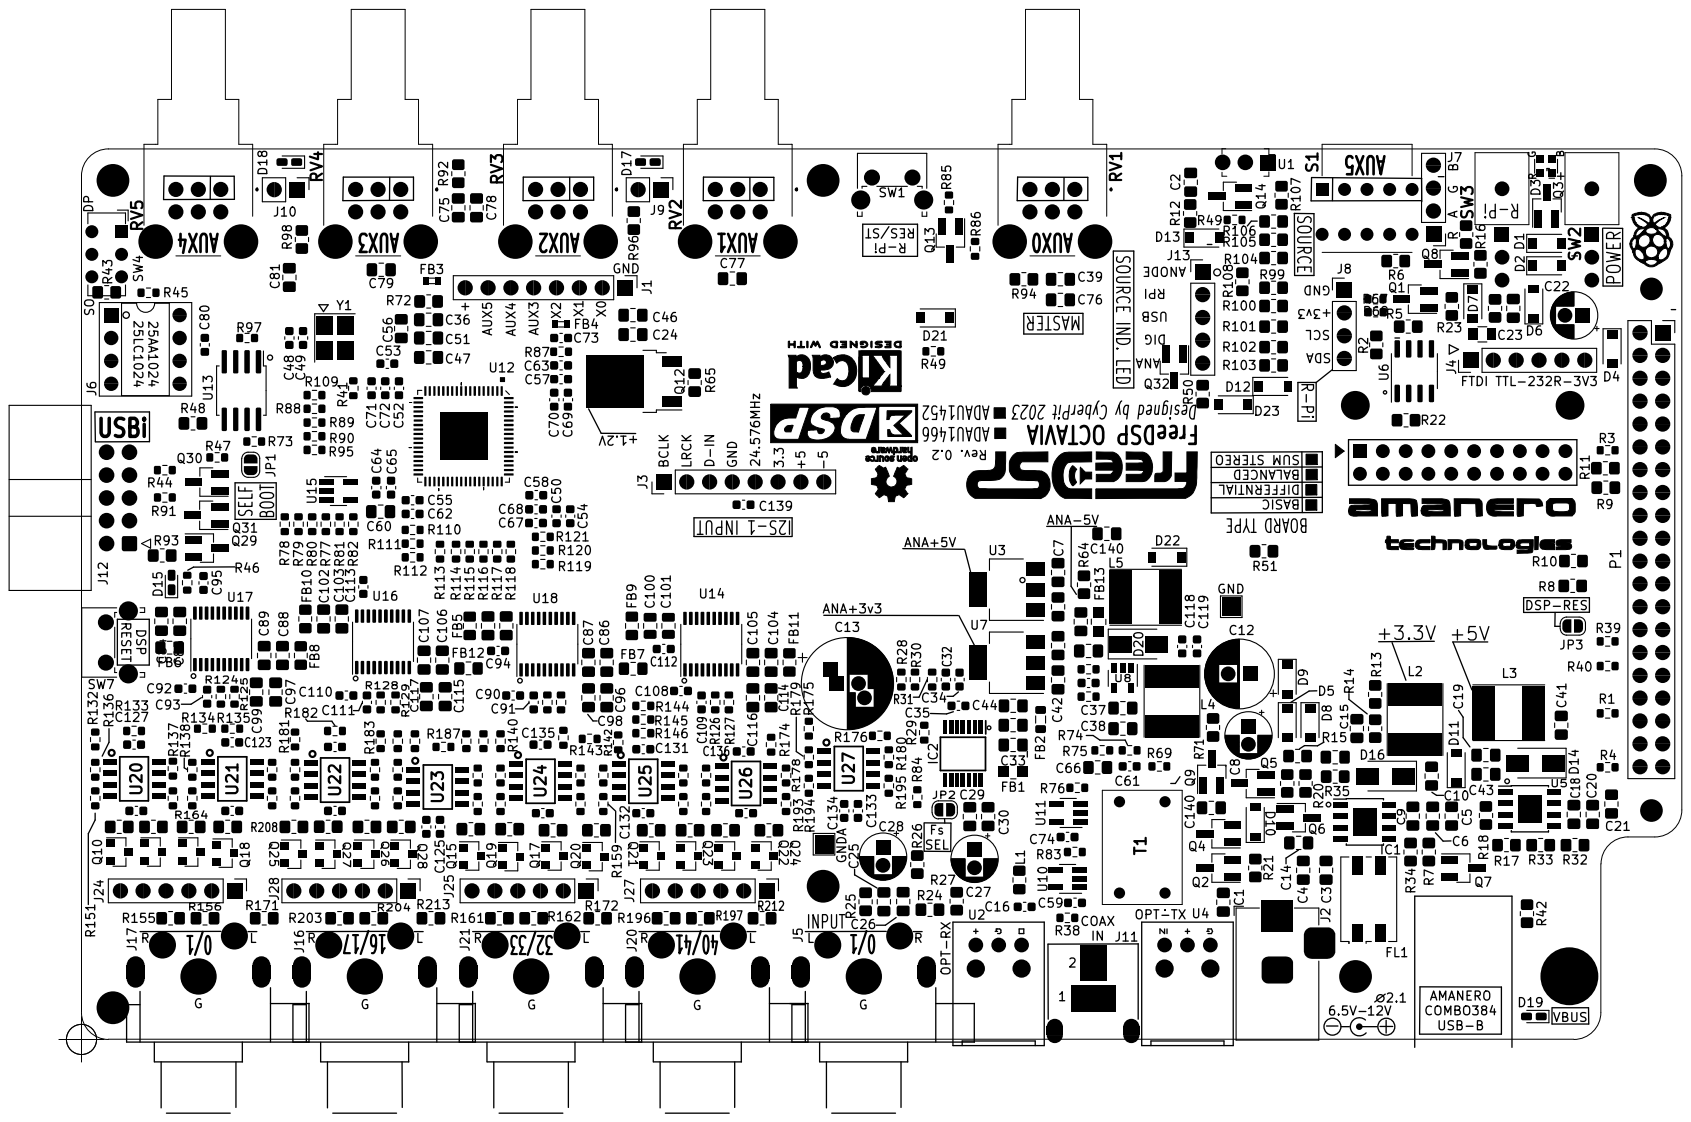
[picture p122: page 1]
