freeDSP/freeDSP-OCTAVIA/SOURCES/Documents/Figures/FreeDSP_OCTAVIA_0v3_TopVIewPlacement.pdf

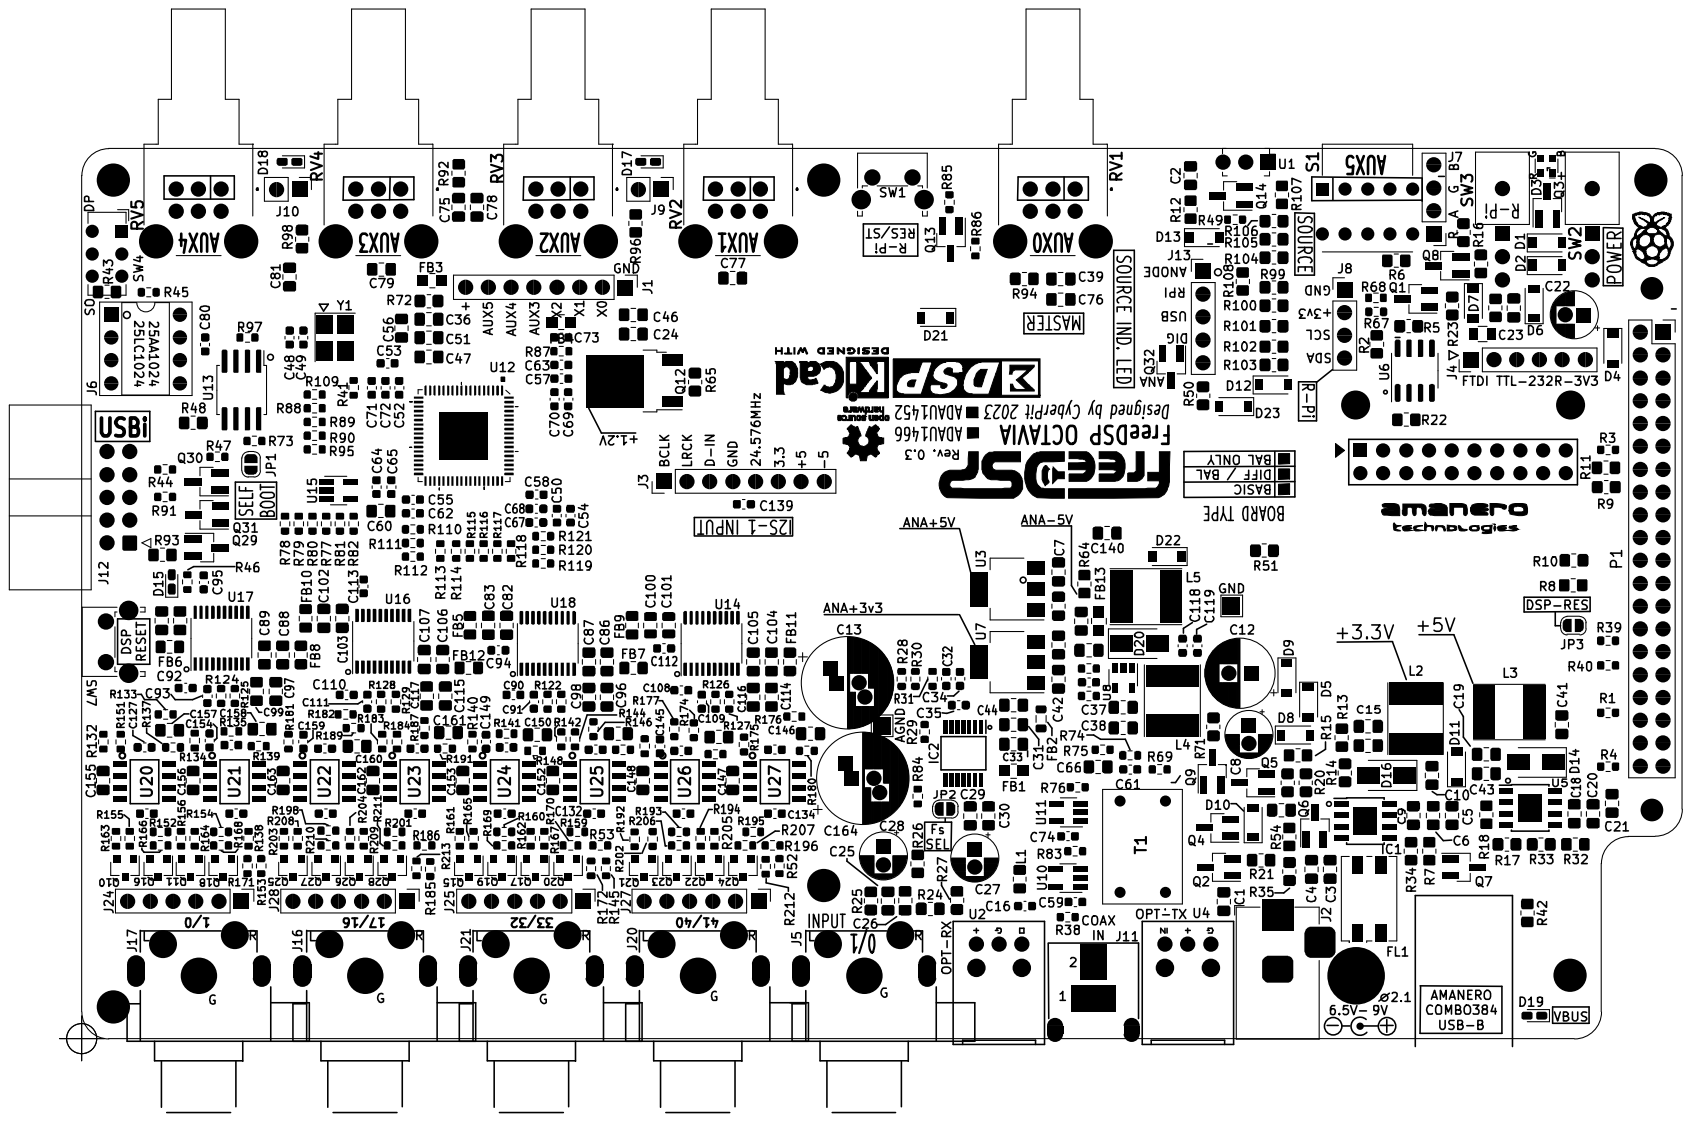
[picture p123: page 1]
