freeDSP/freeDSP-OCTAVIA/SOURCES/Documents/Figures/FreeDSP_OCTAVIA_0v3_TopVIewPatterns.pdf

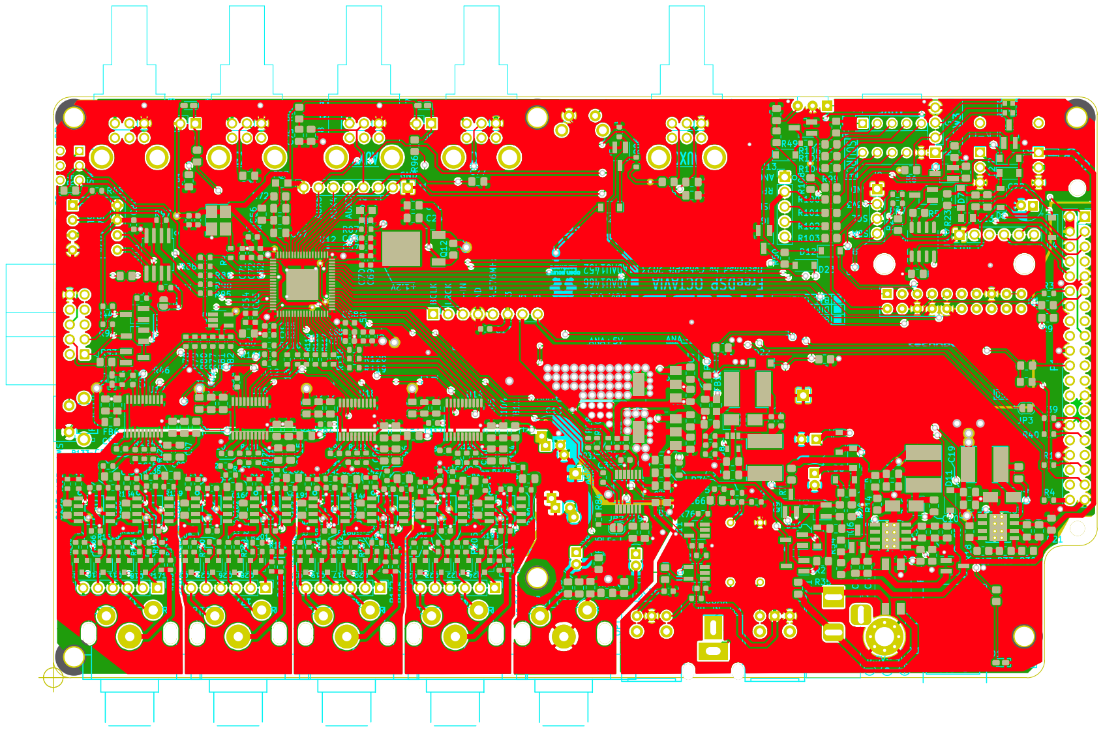
[picture p124: page 1]
